8BitMixtape/8Bit-Mixtape-NEO/boards/8Bit-Mixtape-NEO_v1/DIY_Board/8BitMixtape_ANYMA_Edition_22_MASK.pdf

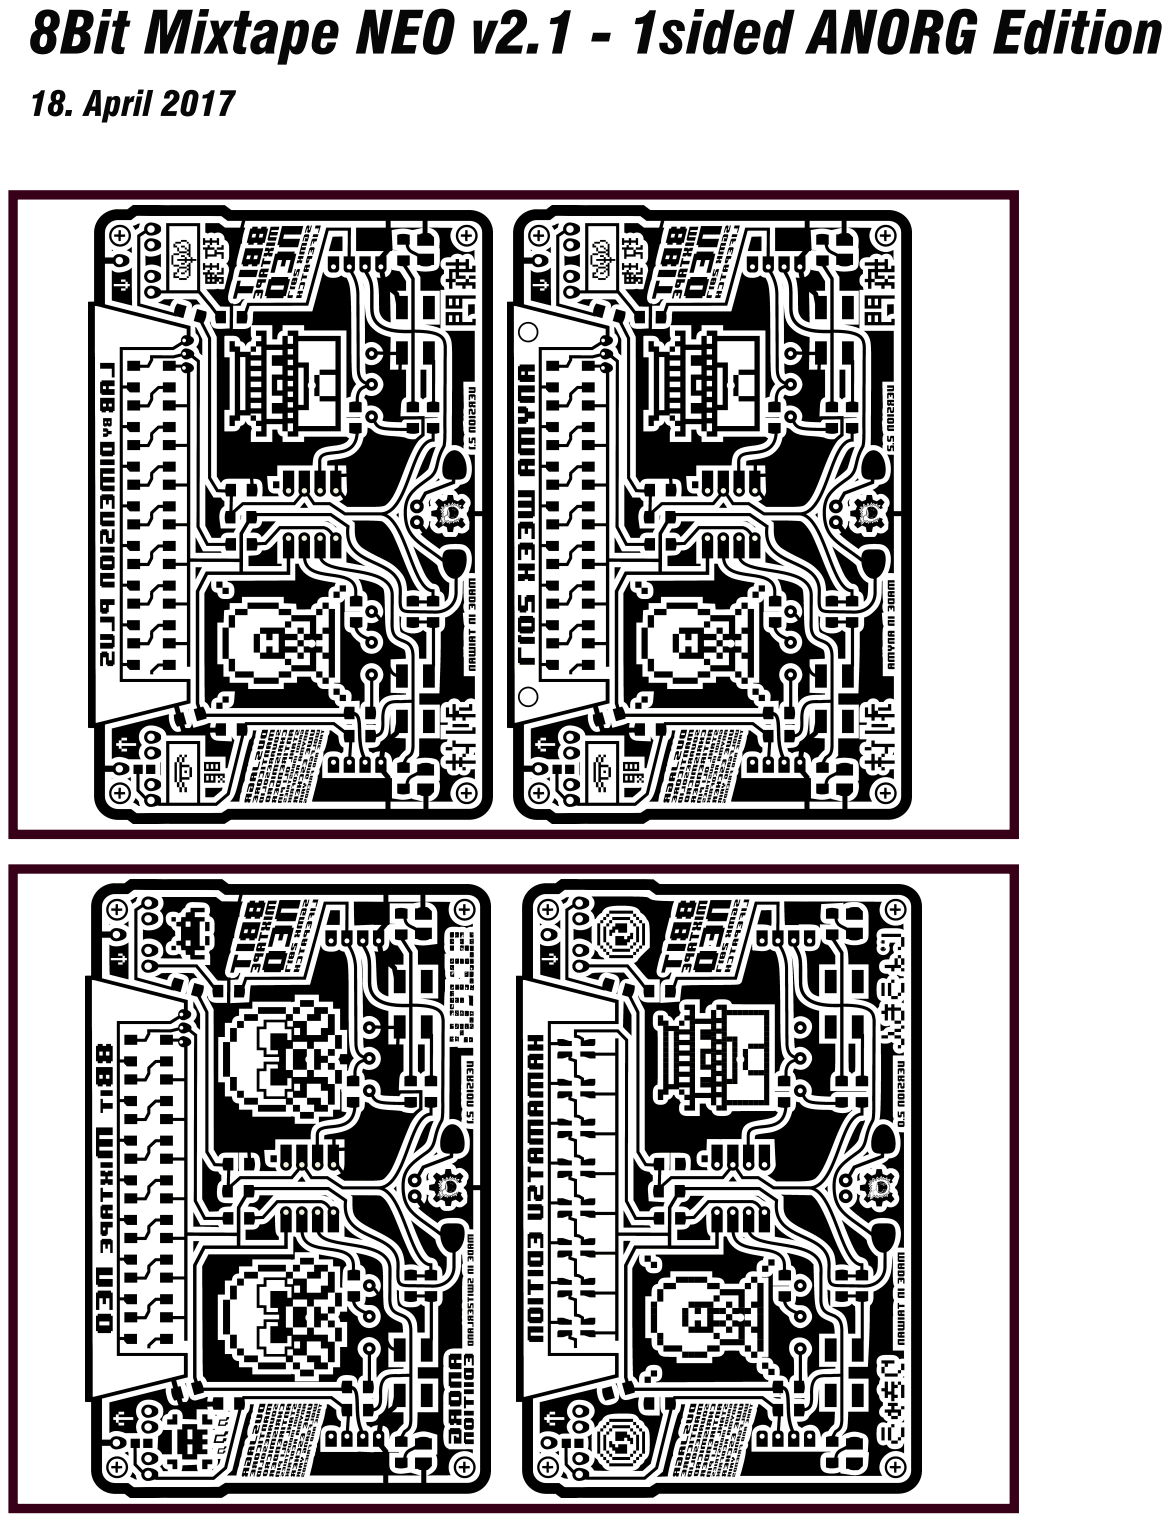
[picture p23: page 1]
