8BitMixtape/8Bit-Mixtape-NEO/boards/8Bit-Mixtape-NEO_v1/DIY_Board/8BitMixtape_Zagreb_Edition_23_MASK.pdf

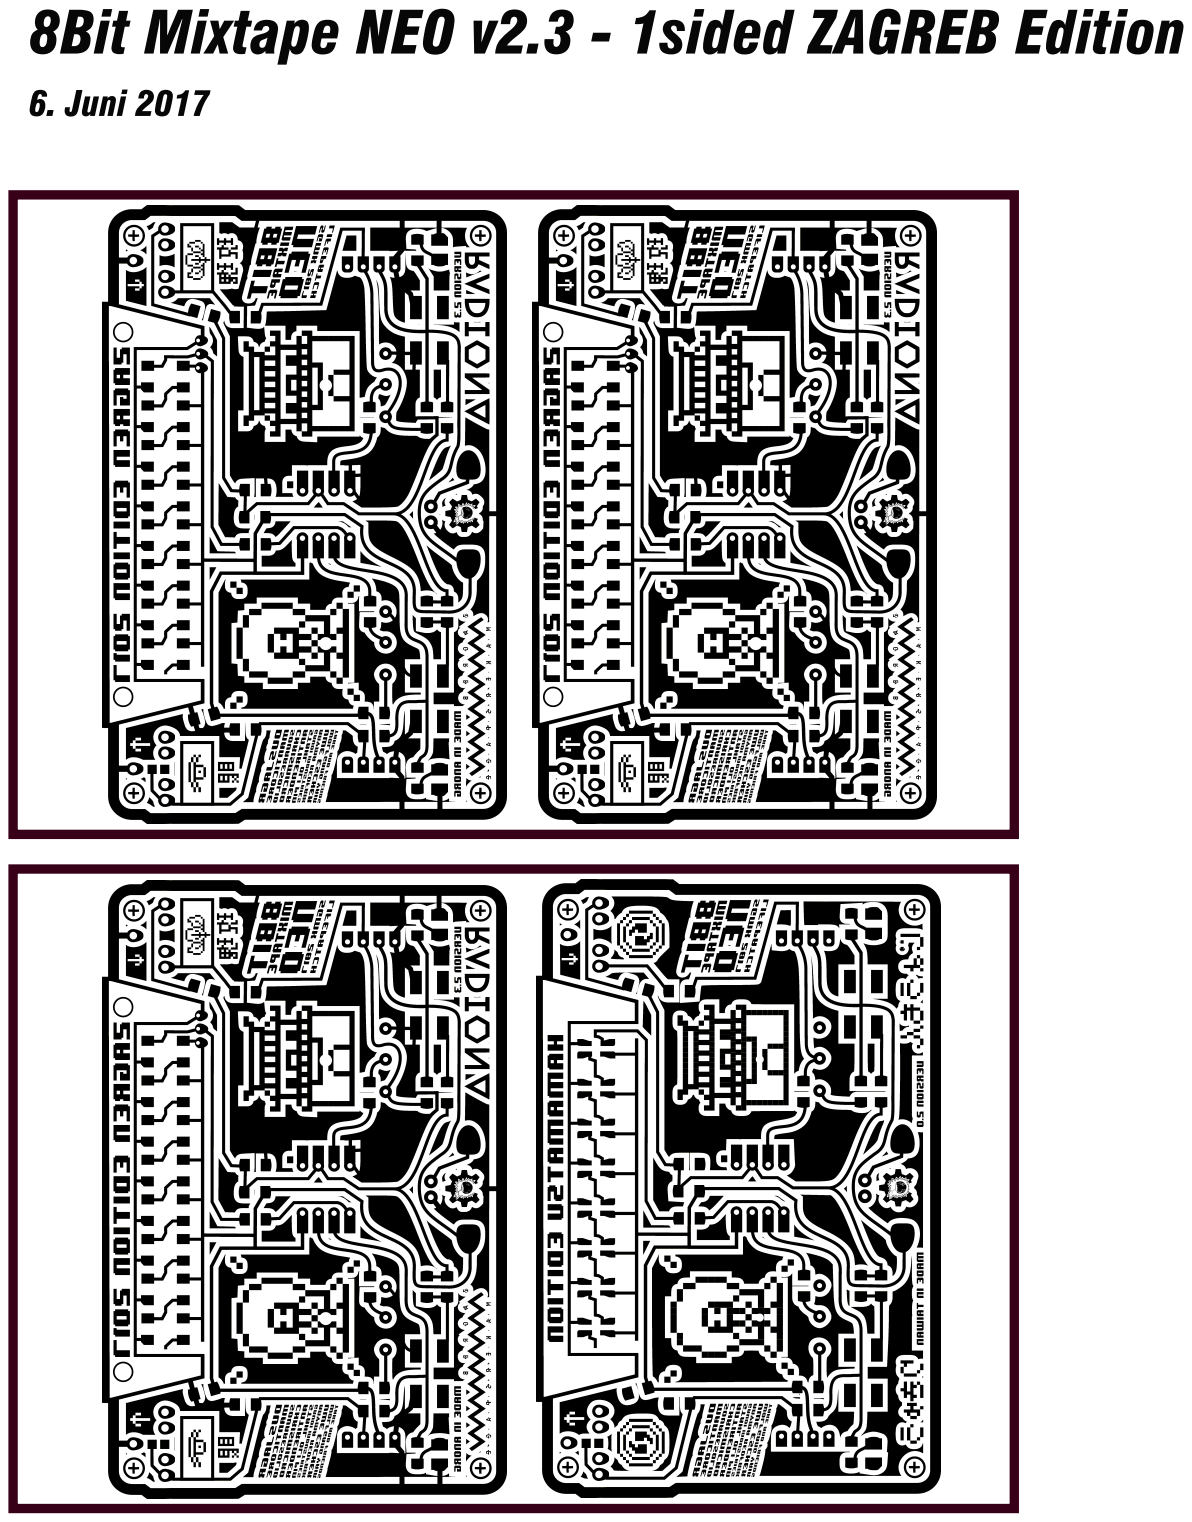
[picture p24: page 1]
