8BitMixtape/8Bit-Mixtape-NEO/boards/8Bit-Mixtape-NEO_v1/DIY_Board/mini_extensions.pdf

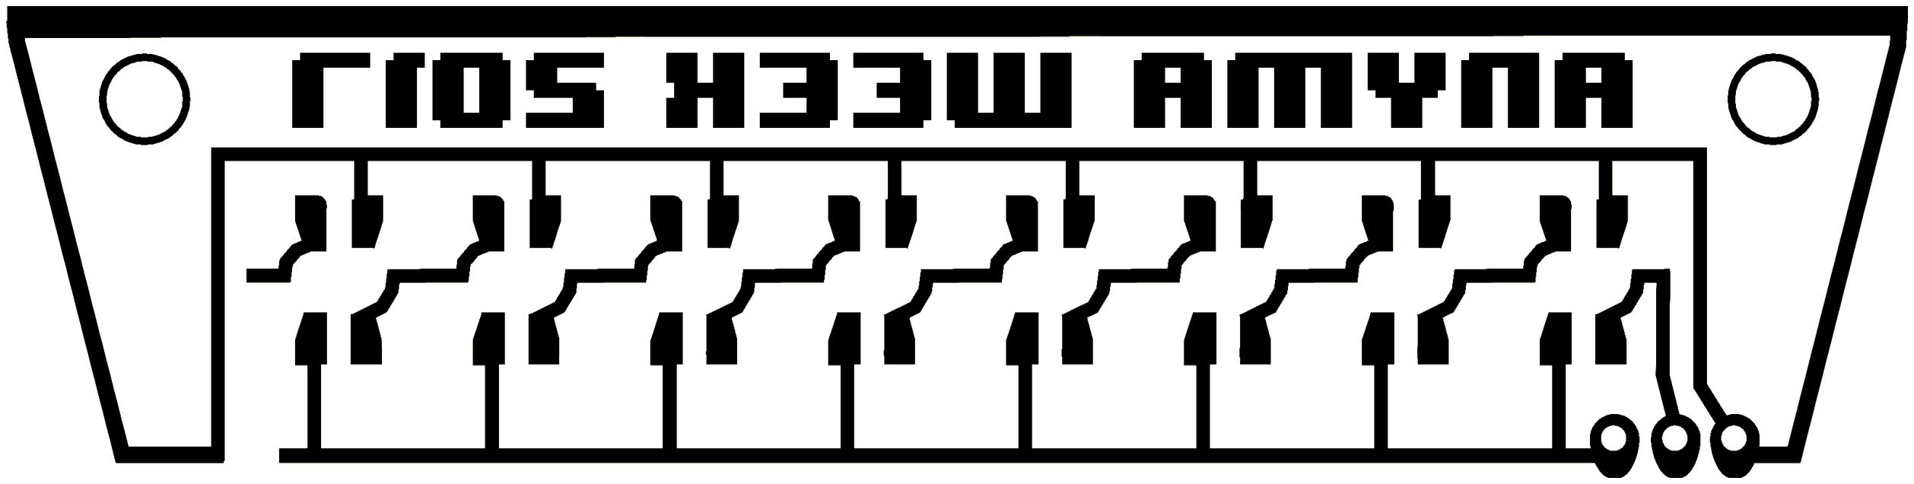
[picture p25: figure]
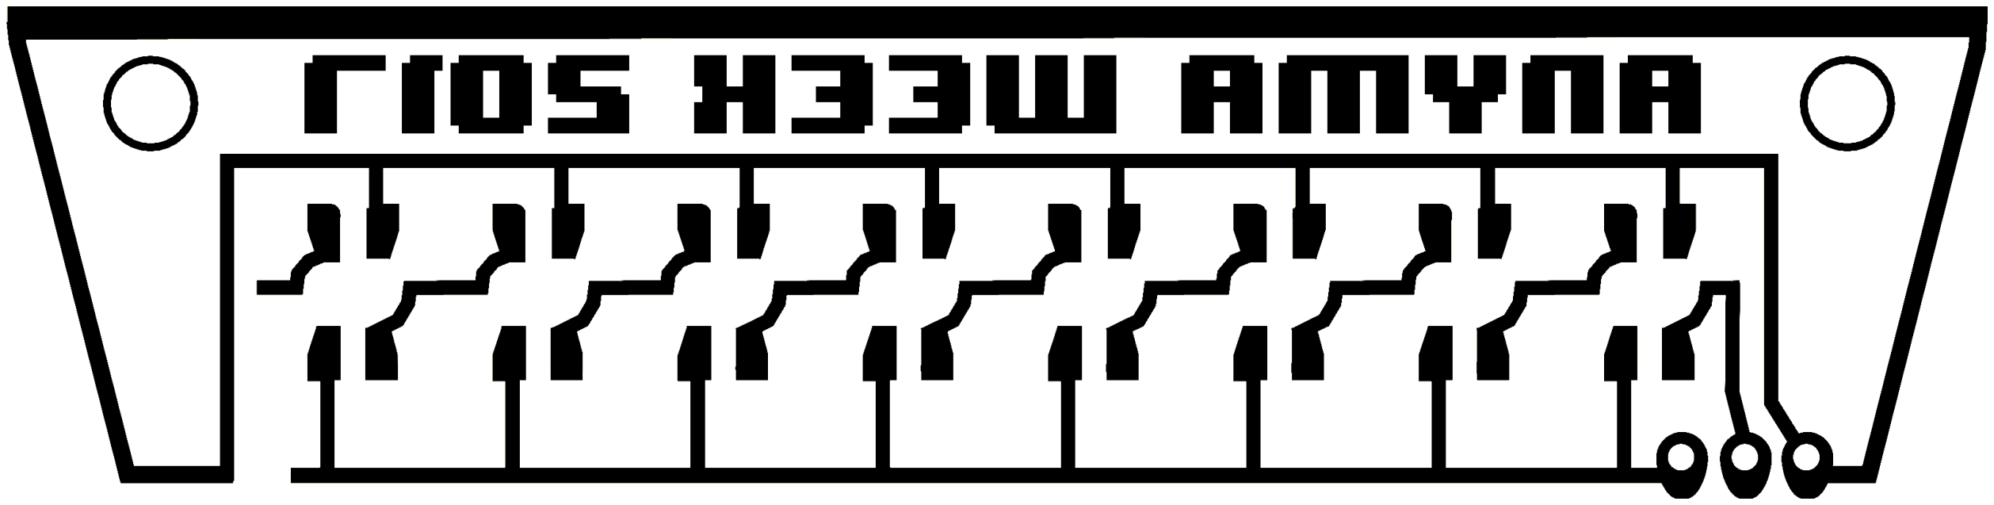
[picture p26: figure]
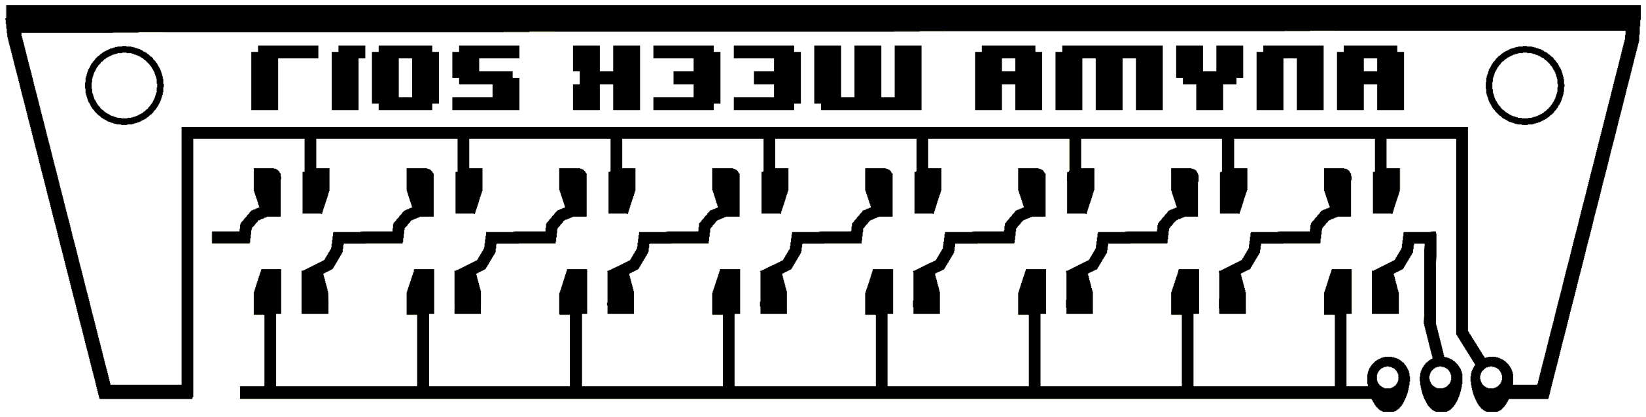
[picture p27: figure]
