8BitMixtape/8Bit-Mixtape-NEO/boards/8Bit-Mixtape-NEO_v1/DIY_Board/8BitMixtape_ANORG_Edition_21_MASK.pdf

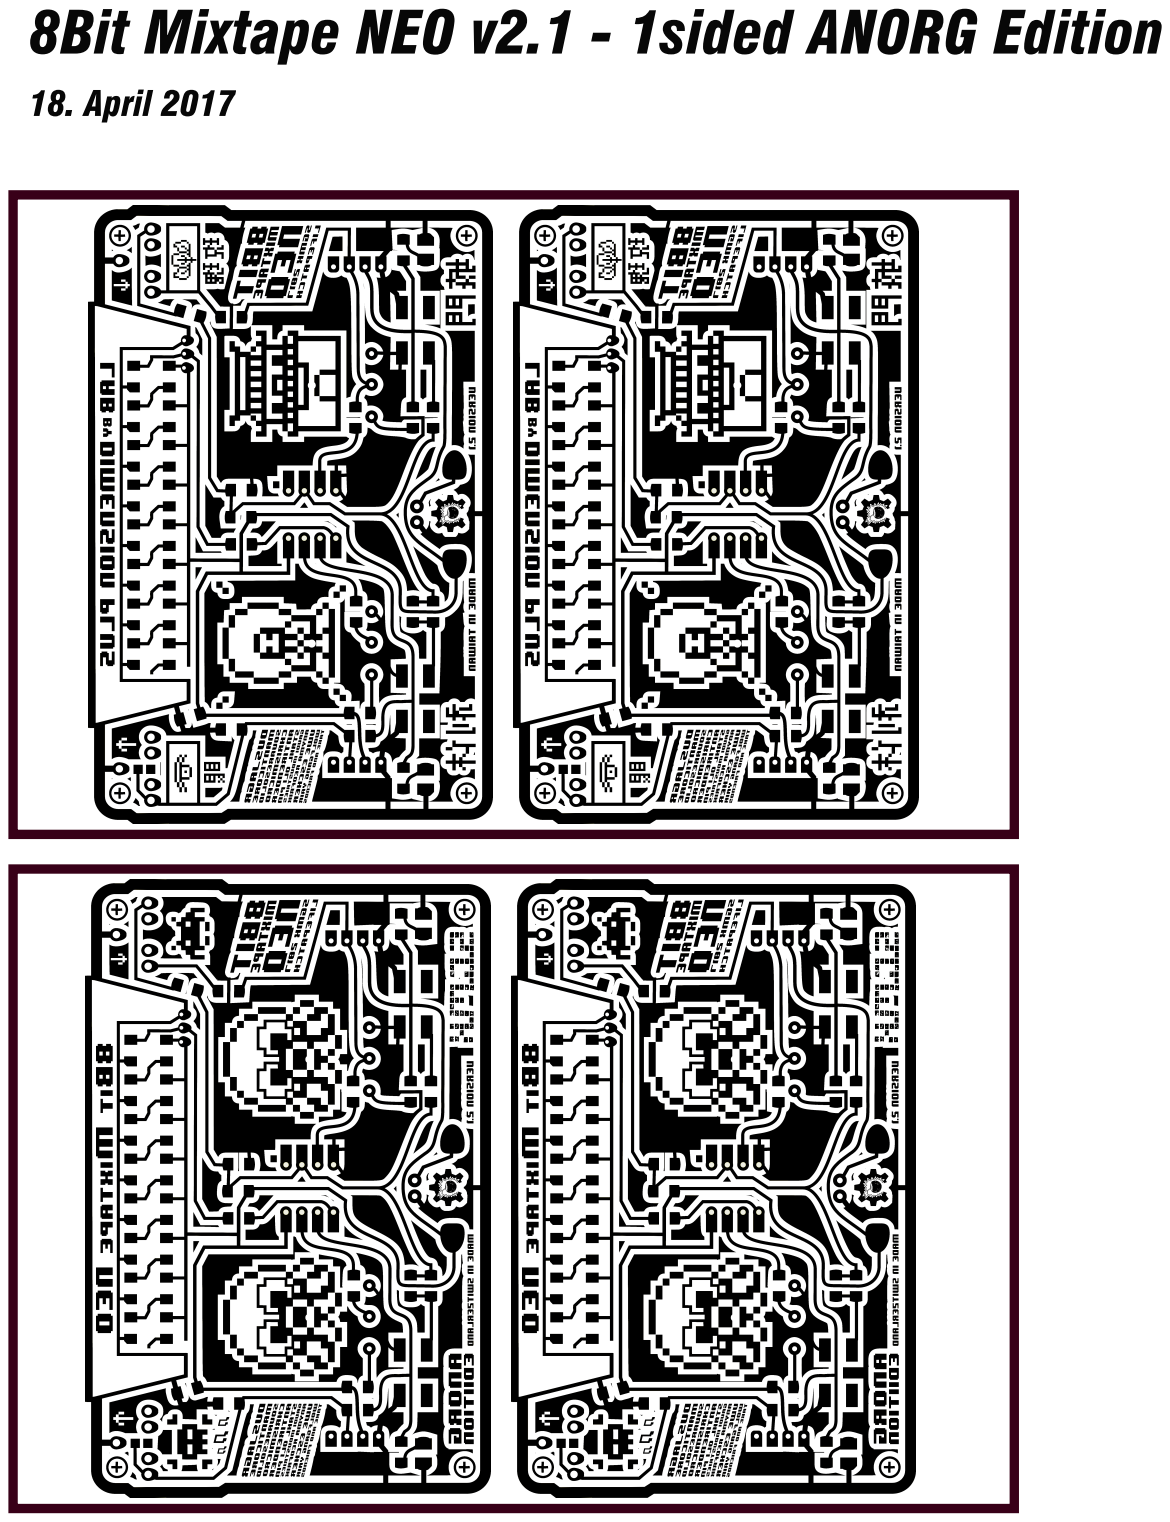
[picture p28: page 1]
