8BitMixtape/8Bit-Mixtape-NEO/boards/8Bit-Mixtape-NEO_v1/DIY_Board/8BitMixtape_Hamamatsu_Edition_20_MASK.pdf

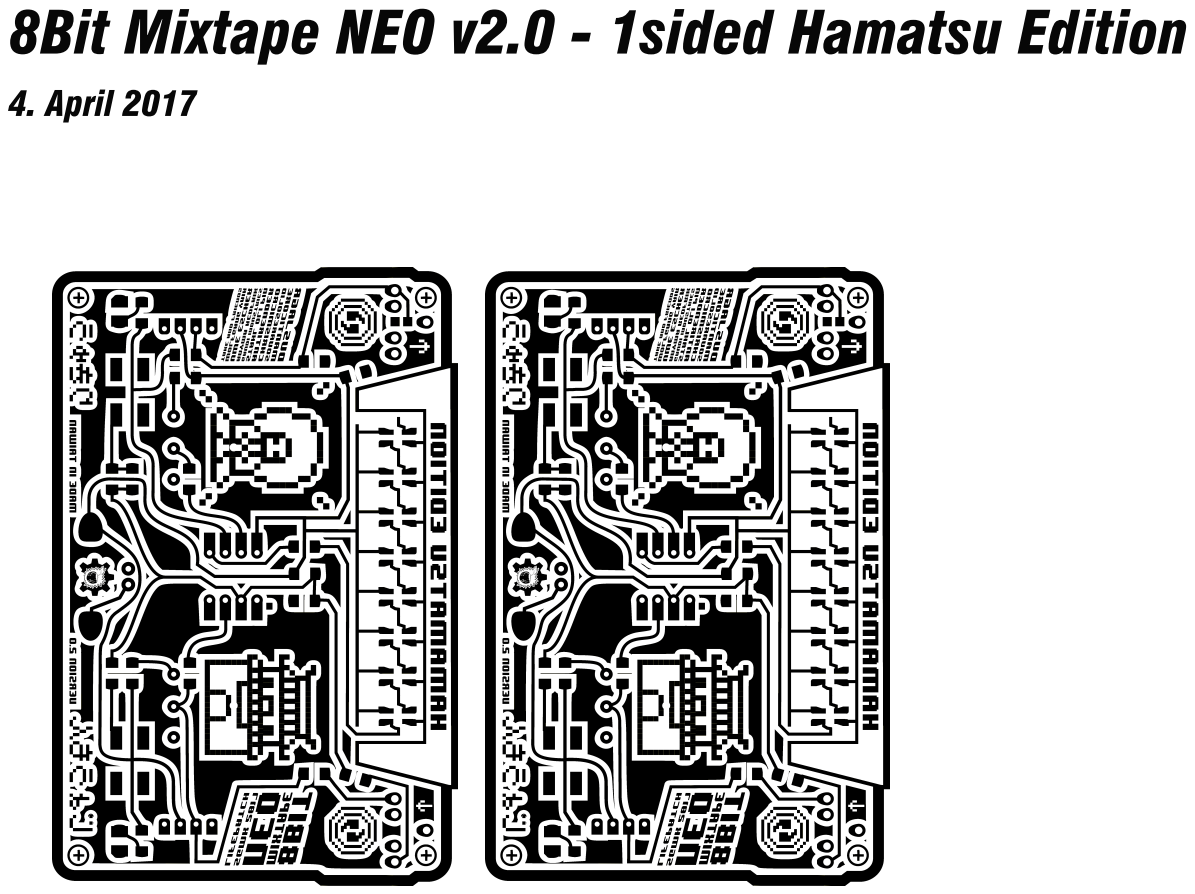
[picture p29: page 1]
