8BitMixtape/8Bit-Mixtape-NEO/boards/8Bit-Mixtape-NEO_v1/DIY_Board/8BitMixtape_Taiwan_Edition_20_MASK.pdf

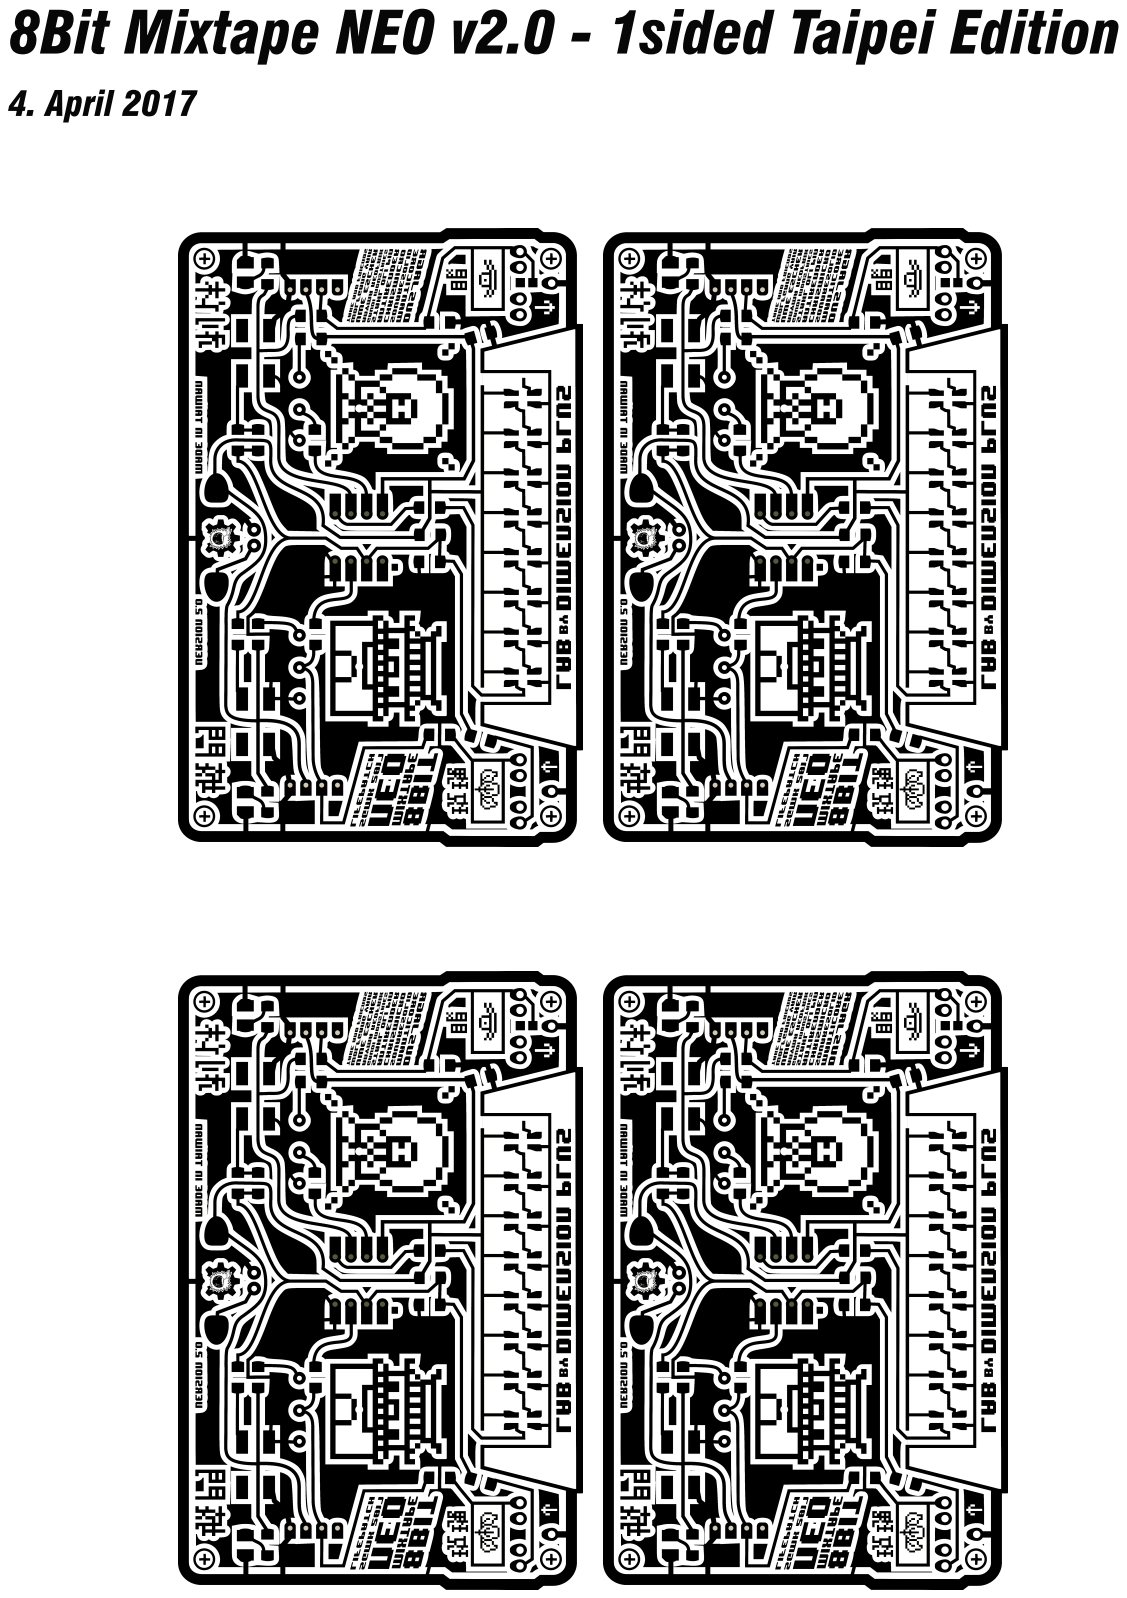
[picture p30: page 1]
