8BitMixtape/8Bit-Mixtape-NEO/boards/8Bit-Mixtape-NEO_v1/DIY_Board/8BitMixtape_Taiwan_Edition_16_MASK.pdf

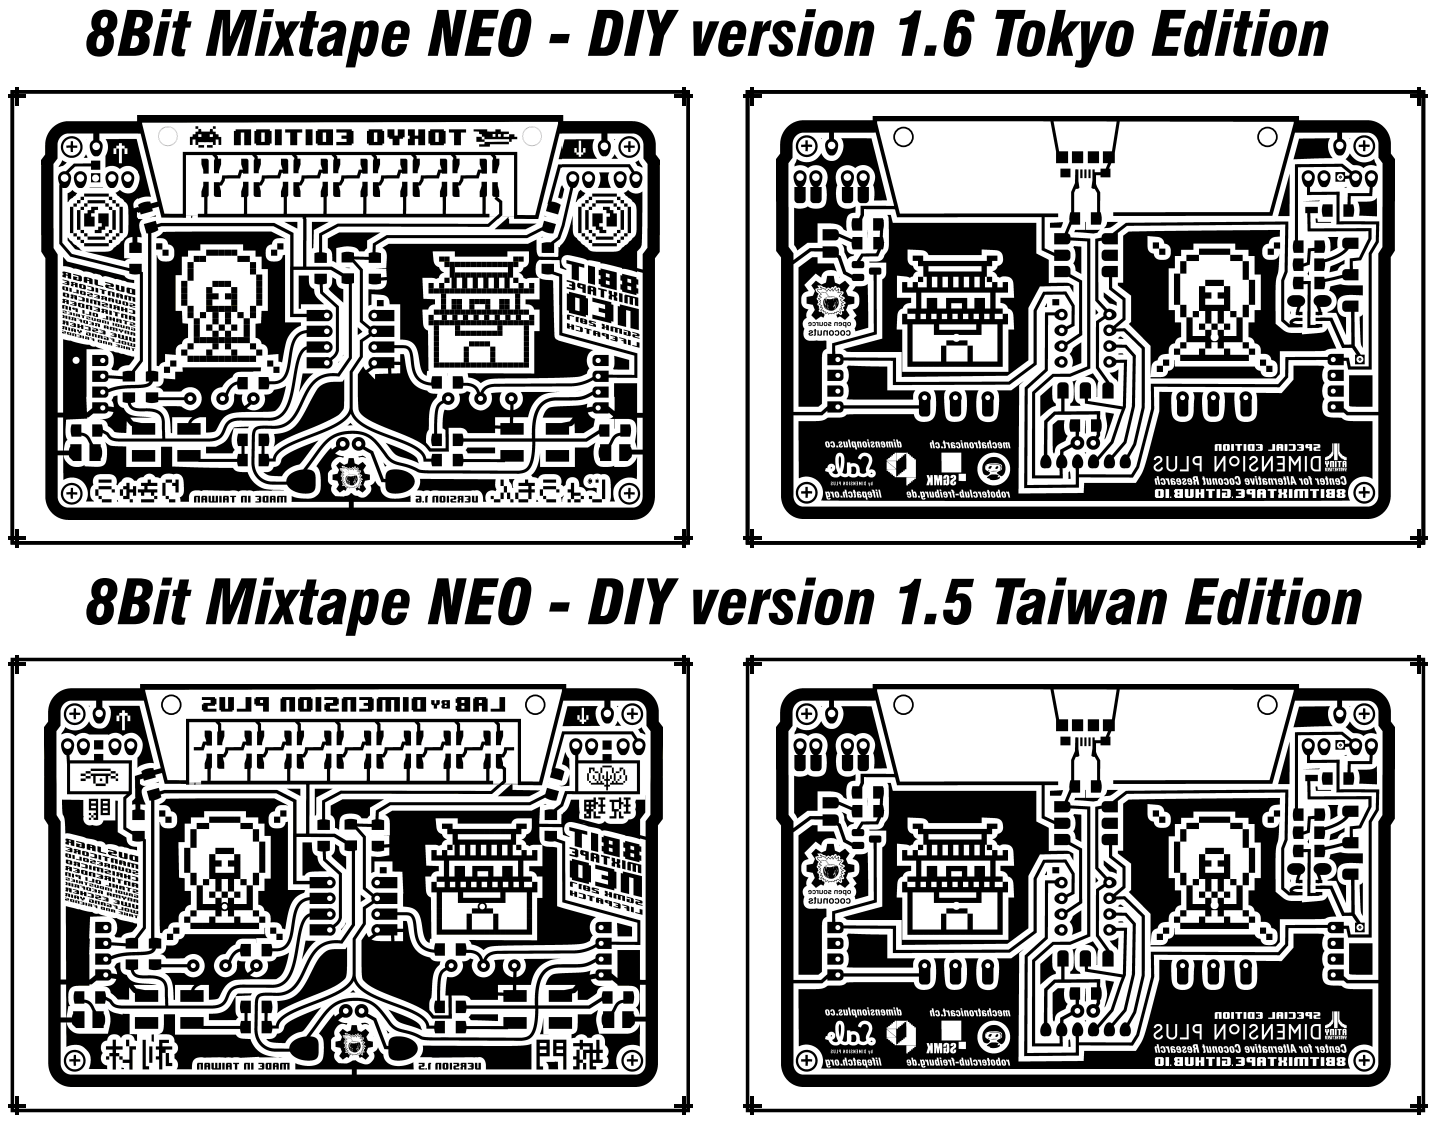
[picture p31: page 1]
