8BitMixtape/8Bit-Mixtape-NEO/boards/8Bit-Mixtape-NEO_v1/DIY_Board/8BitMixtape_Taiwan_Edition_15_MASK.pdf

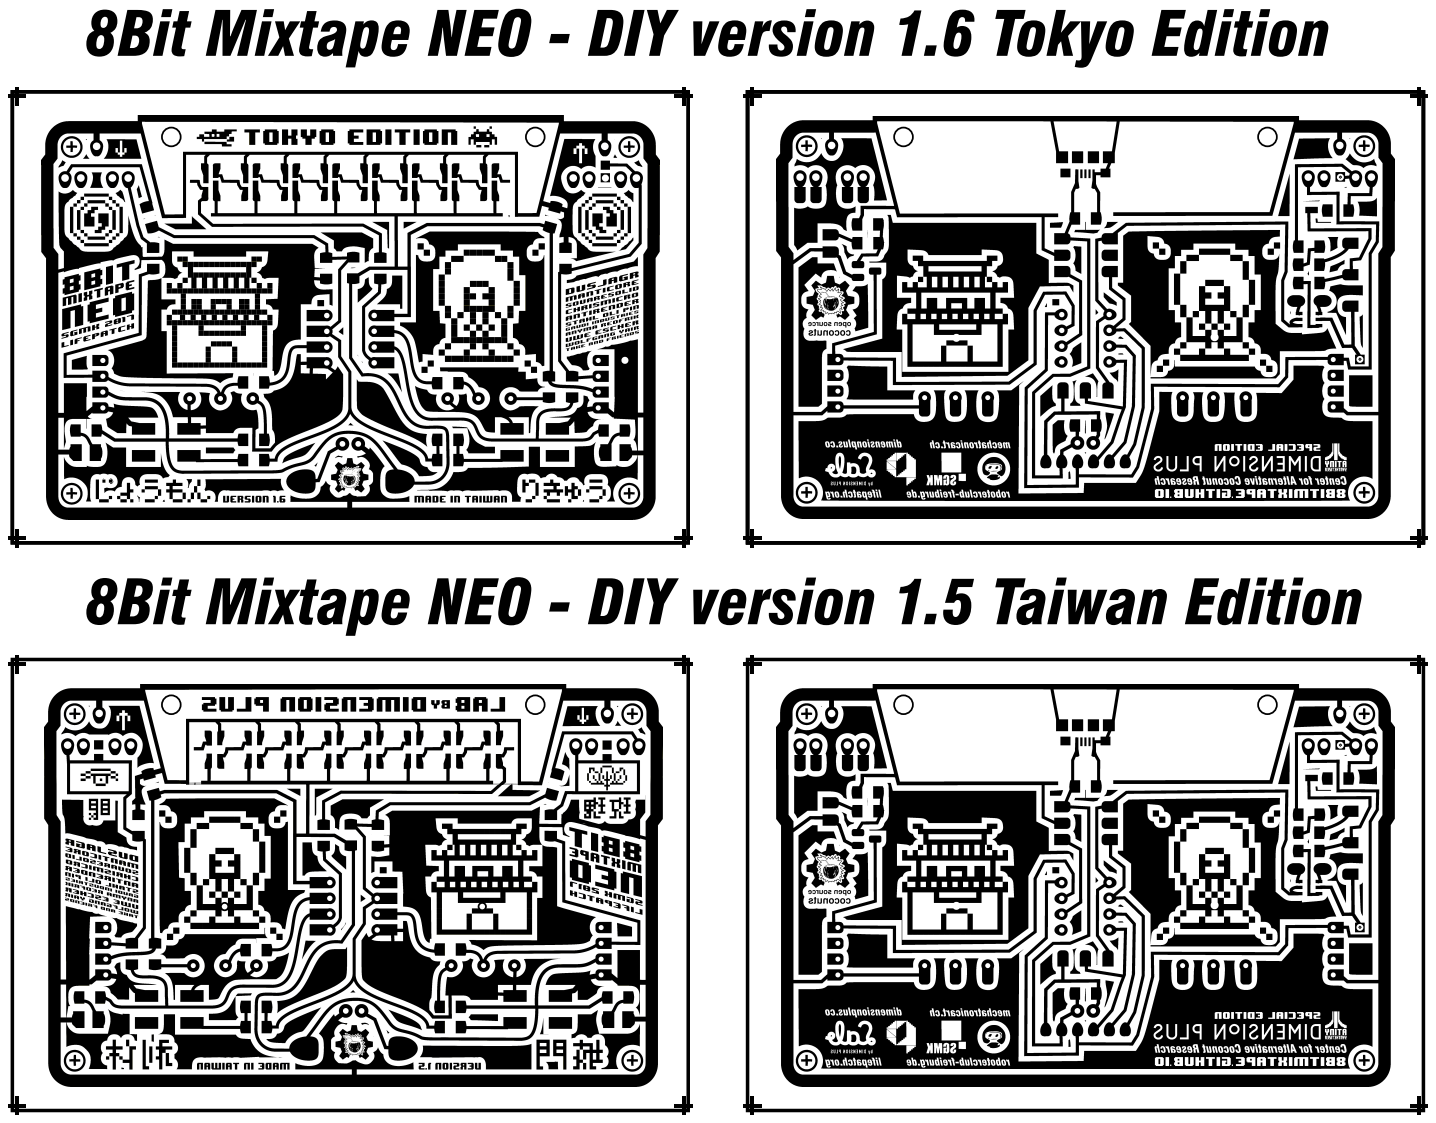
[picture p32: page 1]
