8BitMixtape/8Bit-Mixtape-NEO/boards/8Bit-Mixtape-NEO_v1/DIY_Board/8BitMixtape_Taiwan_Edition_14_MASK.pdf

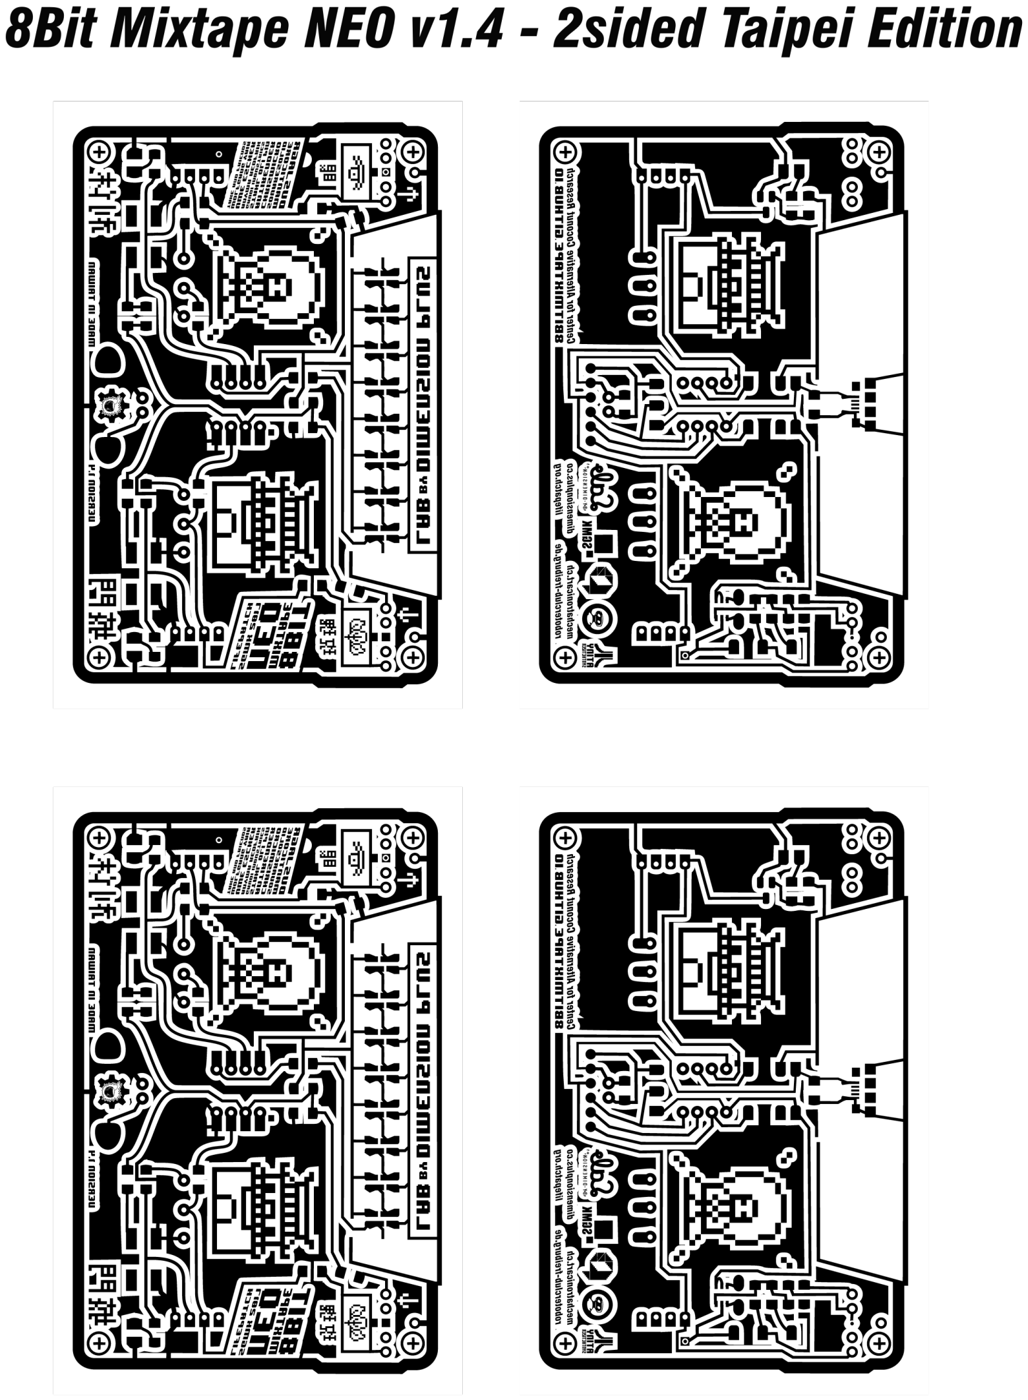
[picture p33: page 1]
