8BitMixtape/8Bit-Mixtape-NEO/8BitMixtapeNEO_v20_TaiwanReady.jpg

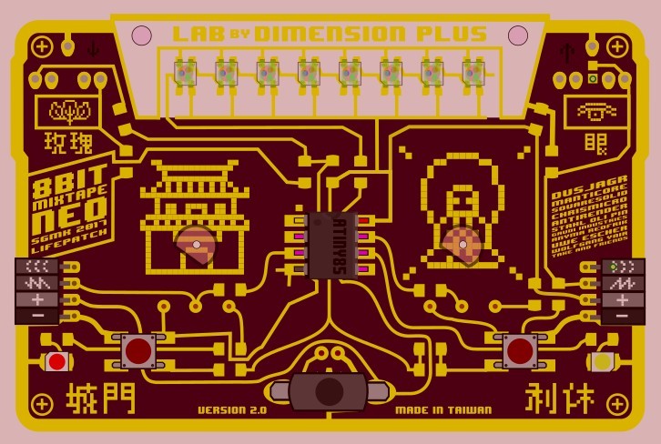
8BitMixtapeNEO_v20_TaiwanReady.jpg
