8BitMixtape/8Bit-Mixtape-NEO/boards/3d-files/Photos/mixTapes_prototypes_cirkulacija2.jpg

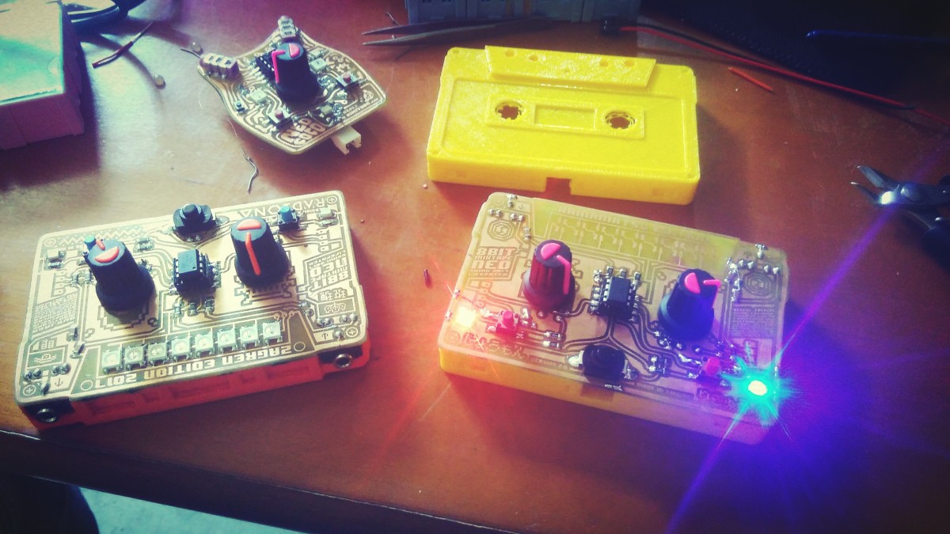
boards/3d-files/Photos/mixTapes_prototypes_cirkulacija2.jpg
