8BitMixtape/8Bit-Mixtape-NEO/boards/3d-files/Photos/Tape_3d_FullCase_Update_v4.jpg

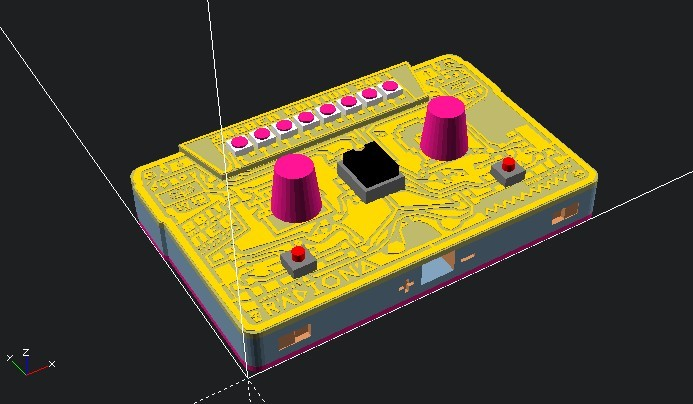
boards/3d-files/Photos/Tape_3d_FullCase_Update_v4.jpg
