8BitMixtape/8Bit-Mixtape-NEO/boards/8Bit-Mixtape-NEO_v1/8BitMixtapeNEO_v10_design.jpg

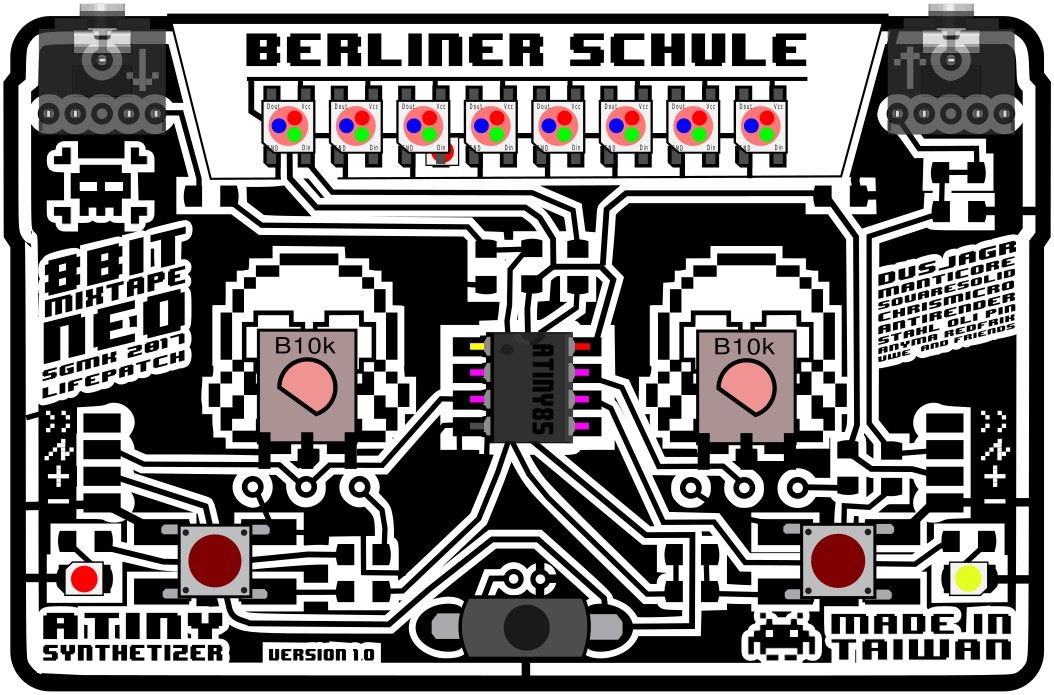
boards/8Bit-Mixtape-NEO_v1/8BitMixtapeNEO_v10_design.jpg
