8BitMixtape/8Bit-Mixtape-NEO/boards/8Bit-Mixtape-NEO_v1/8BitMixtapeNEO_v12_dimension_Black.png

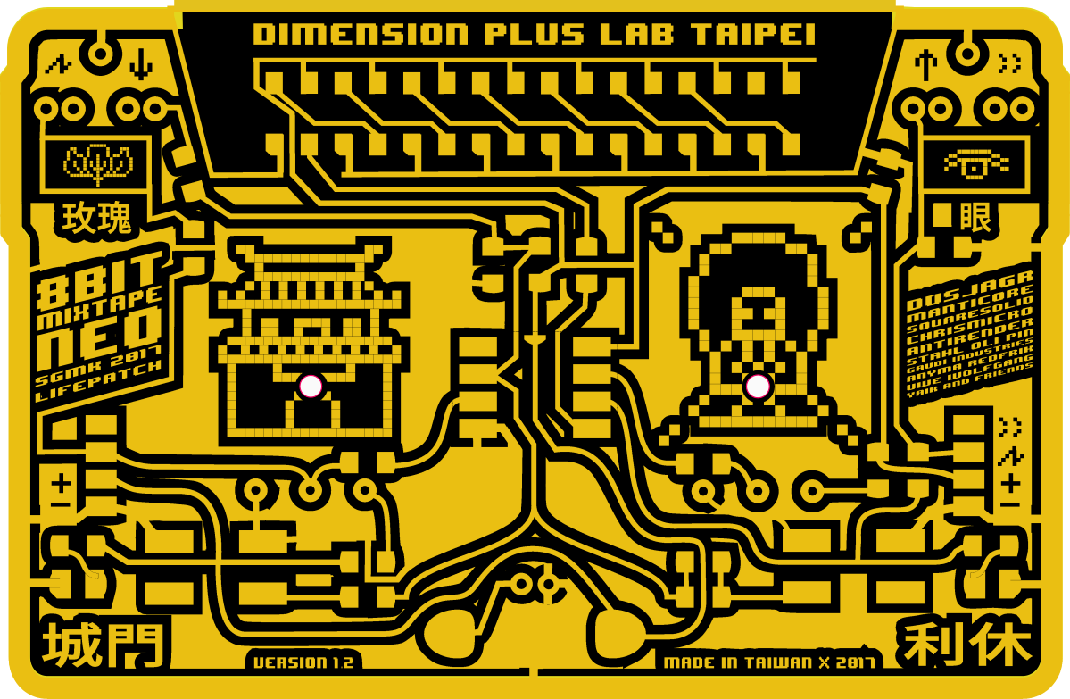
boards/8Bit-Mixtape-NEO_v1/8BitMixtapeNEO_v12_dimension_Black.png
