8BitMixtape/8Bit-Mixtape-NEO/boards/8Bit-Mixtape-NEO_v1/DIY_Board/8BitMixtape_DIY_Edition_27_pure.png

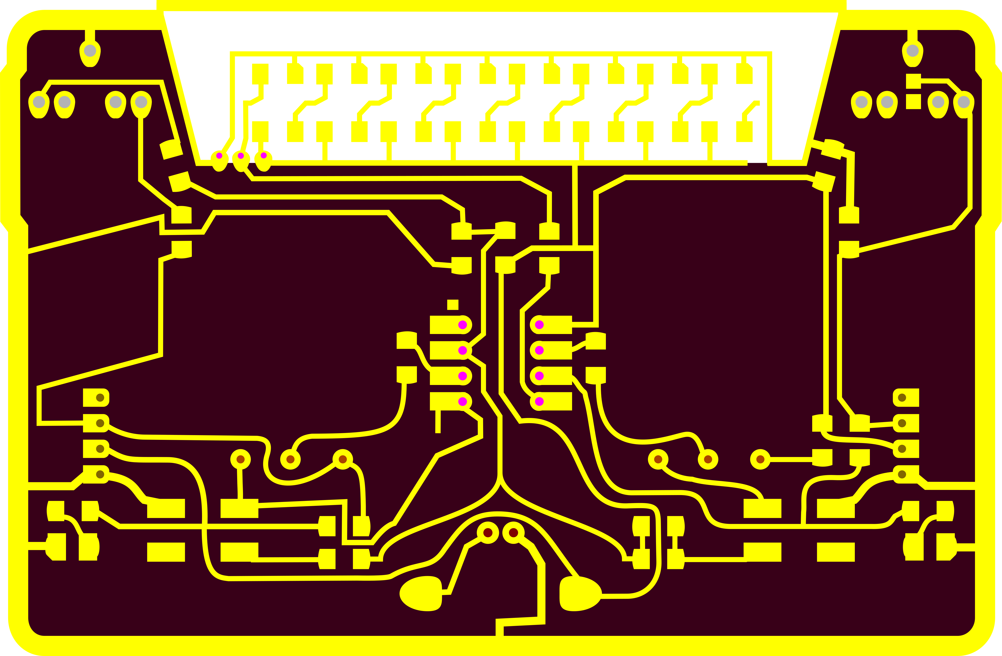
boards/8Bit-Mixtape-NEO_v1/DIY_Board/8BitMixtape_DIY_Edition_27_pure.png
