8BitMixtape/8Bit-Mixtape-NEO/boards/8Bit-Mixtape-NEO_v1/DIY_Board/8BitMixtape_Ucok.png

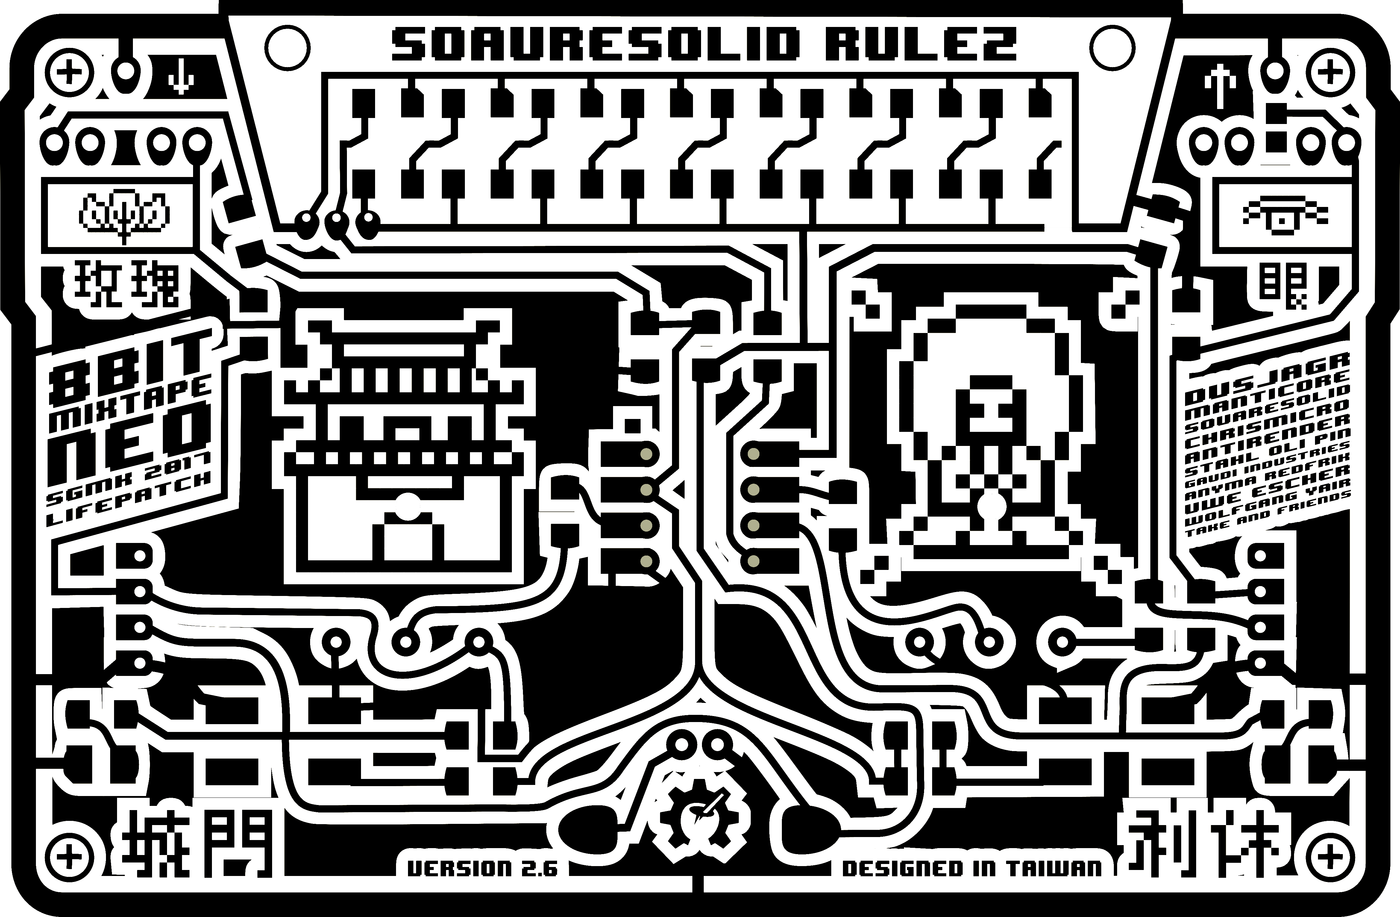
boards/8Bit-Mixtape-NEO_v1/DIY_Board/8BitMixtape_Ucok.png
