8BitMixtape/8Bit-Mixtape-NEO/boards/8Bit-Mixtape-NEO_v1/DIY_Board/MixTape_DP-Style_v20_MASK.png

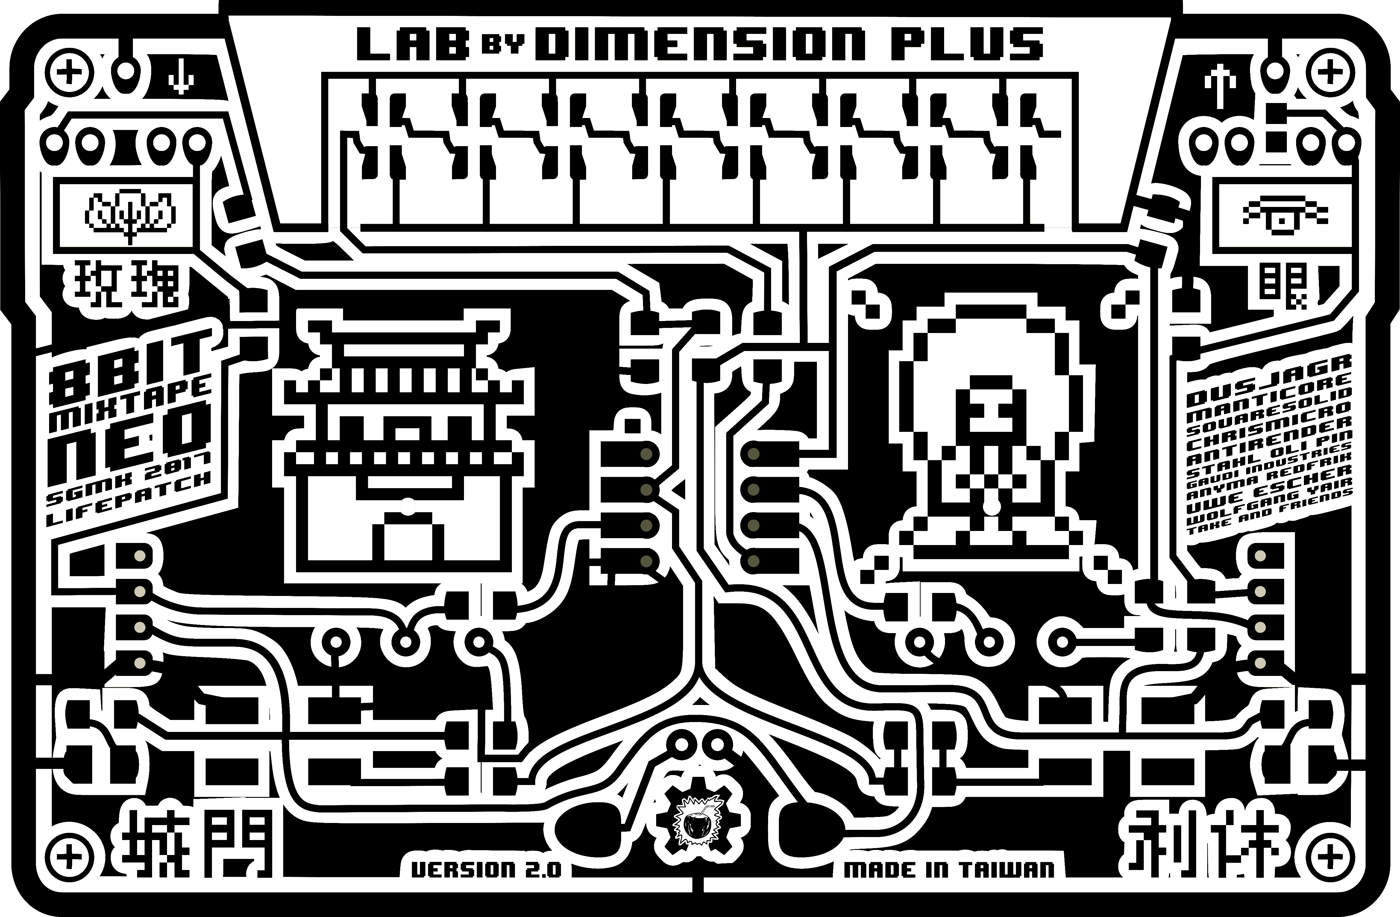
boards/8Bit-Mixtape-NEO_v1/DIY_Board/MixTape_DP-Style_v20_MASK.png
