8BitMixtape/8Bit-Mixtape-NEO/boards/8Bit-Mixtape-NEO_v1/DIY_Board/MixTape_NoStyle_v20.png

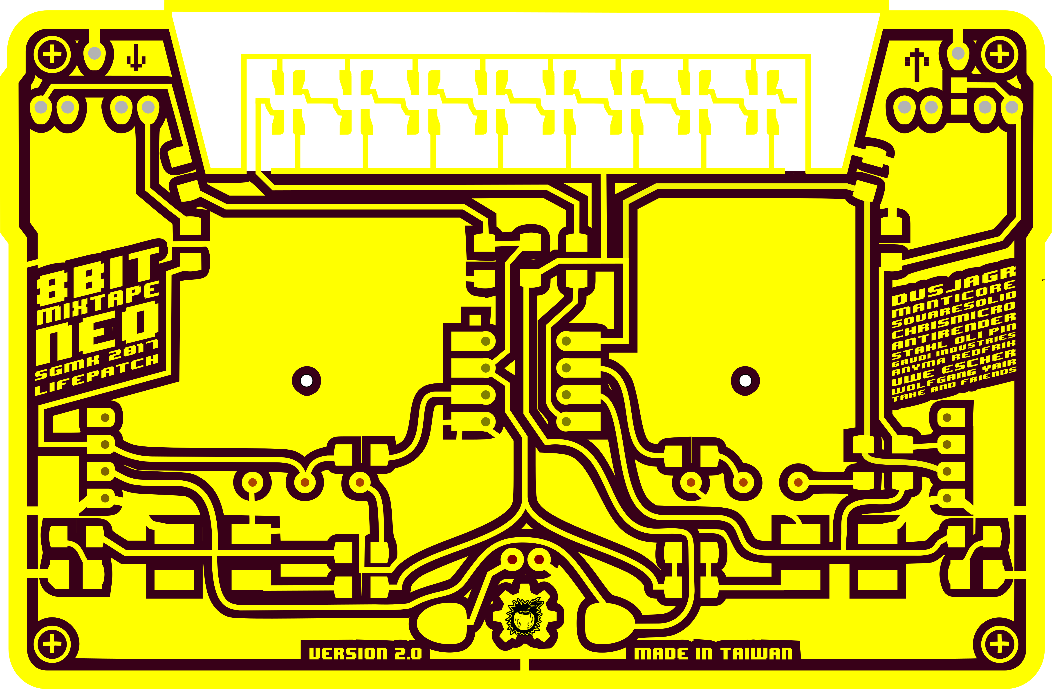
boards/8Bit-Mixtape-NEO_v1/DIY_Board/MixTape_NoStyle_v20.png
