8BitMixtape/8Bit-Mixtape-NEO/boards/8Bit-Mixtape-NEO_v1/DIY_Board/MixTape_Zagreb-Style_v23.png

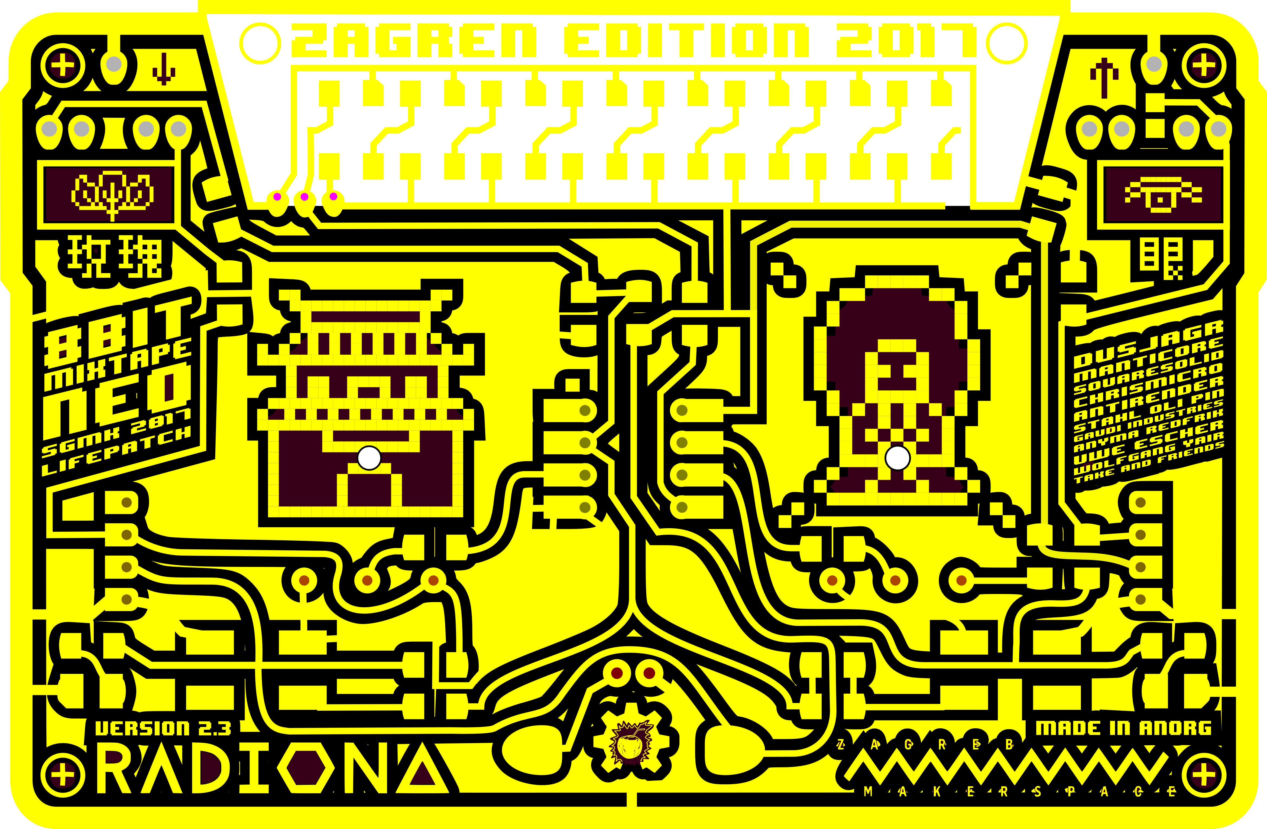
boards/8Bit-Mixtape-NEO_v1/DIY_Board/MixTape_Zagreb-Style_v23.png
