8BitMixtape/8Bit-Mixtape-NEO/boards/8Bit-Mixtape-NEO_v1/DIY_Board/NEO-Mixtape_PixelExtension.png

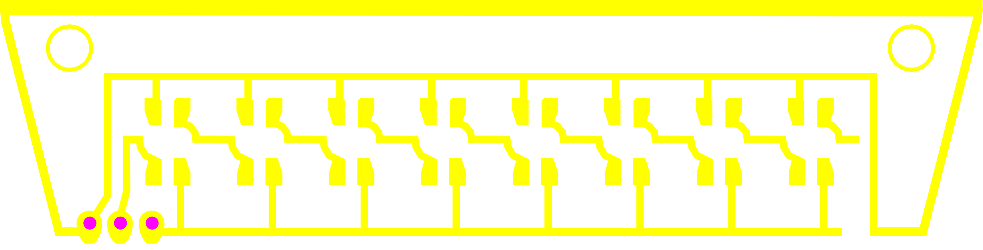
boards/8Bit-Mixtape-NEO_v1/DIY_Board/NEO-Mixtape_PixelExtension.png
