8BitMixtape/8Bit-Mixtape-NEO/boards/8Bit-Mixtape-NEO_v1/MixTape_BackSide_Copper_v20.png

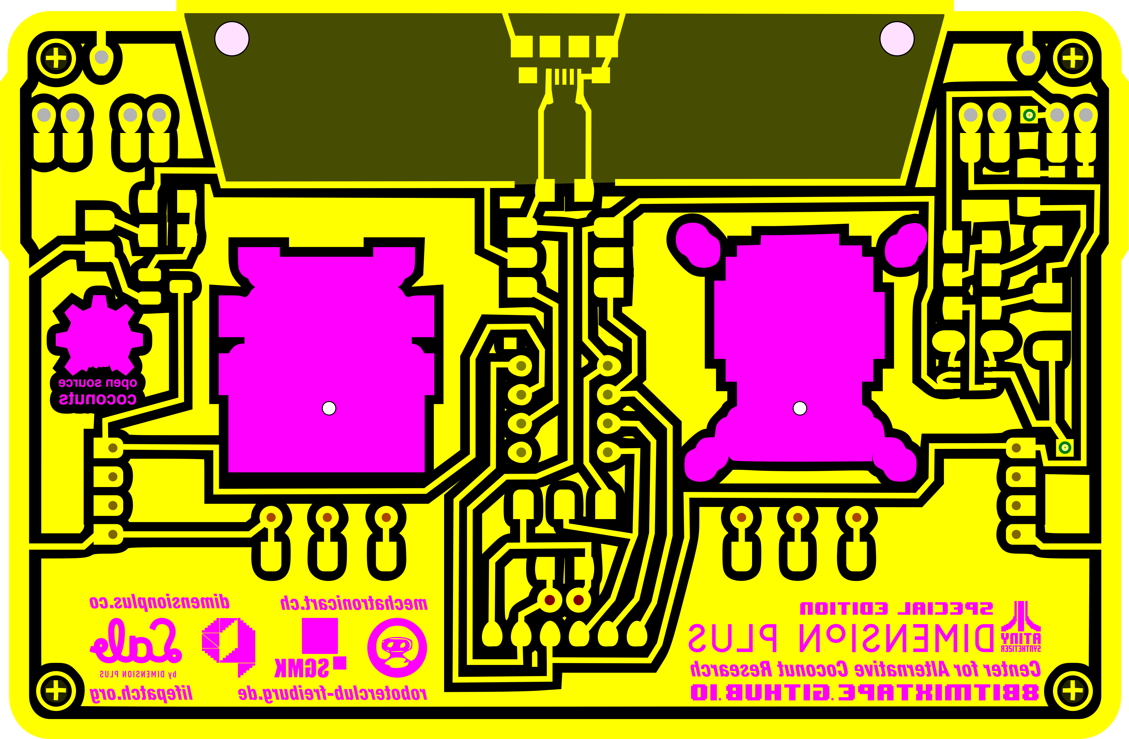
boards/8Bit-Mixtape-NEO_v1/MixTape_BackSide_Copper_v20.png
