8BitMixtape/8Bit-Mixtape-NEO/boards/8Bit-Mixtape-NEO_v1/Robertos_DIL_board.jpg

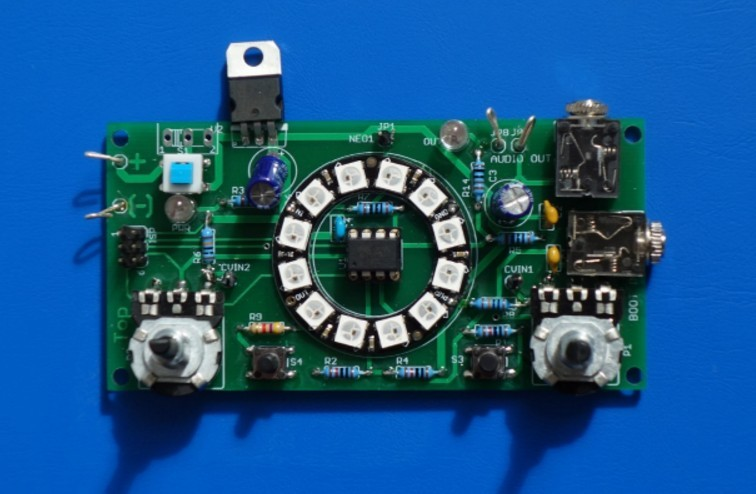
boards/8Bit-Mixtape-NEO_v1/Robertos_DIL_board.jpg
