8BitMixtape/8Bit-Mixtape-NEO/boards/8Bit-Mixtape-NEO_v1/ShenzhenReady/8BitMixtape-NEO_Backside_v10.png

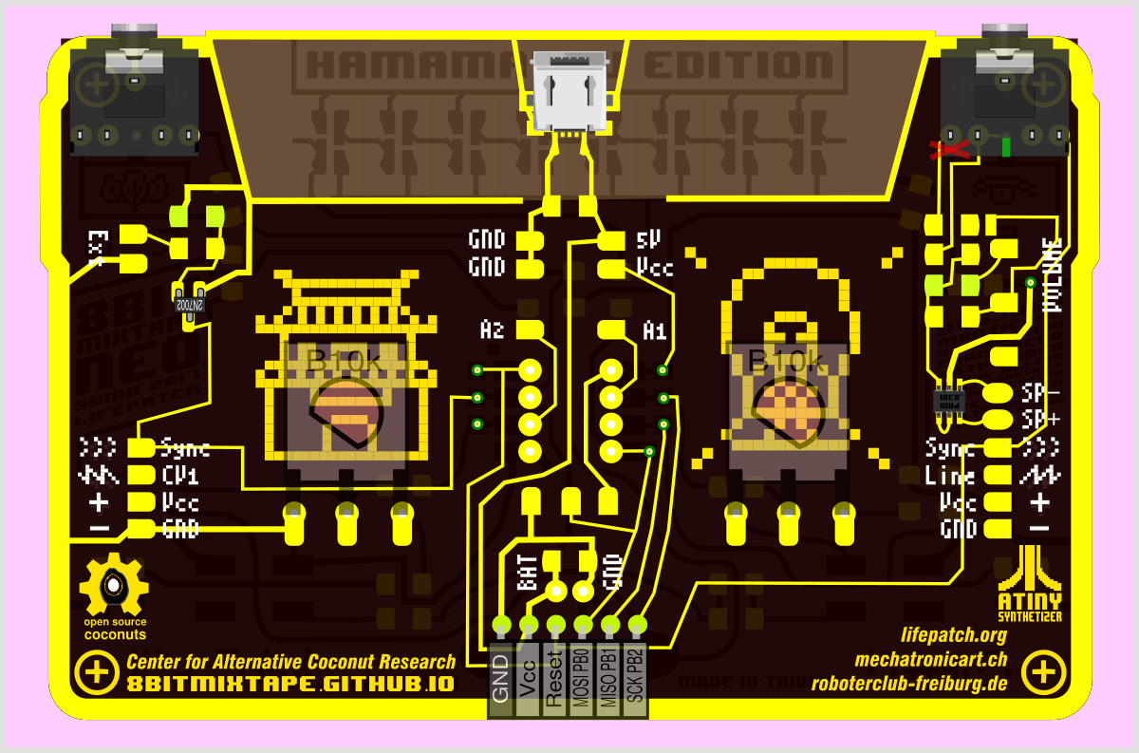
boards/8Bit-Mixtape-NEO_v1/ShenzhenReady/8BitMixtape-NEO_Backside_v10.png
