8BitMixtape/8Bit-Mixtape-NEO/boards/8Bit-Mixtape-NEO_v1/ShenzhenReady/8BitMixtapeNEO_v20_Minimal.jpg

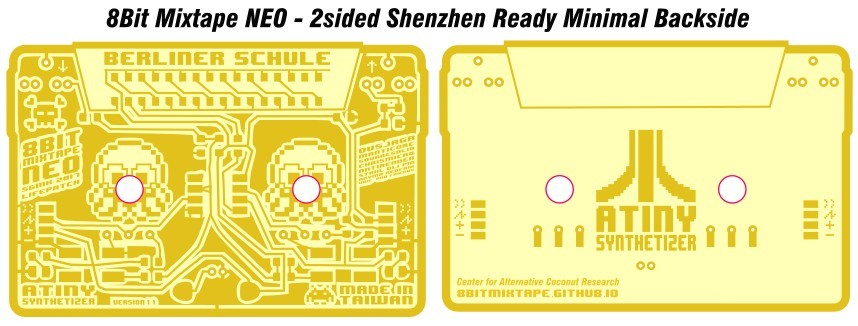
boards/8Bit-Mixtape-NEO_v1/ShenzhenReady/8BitMixtapeNEO_v20_Minimal.jpg
