8BitMixtape/8Bit-Mixtape-NEO/boards/8Bit-Mixtape-NEO_v1/ShenzhenReady/3535_NEO-pixel_Footprint.jpg

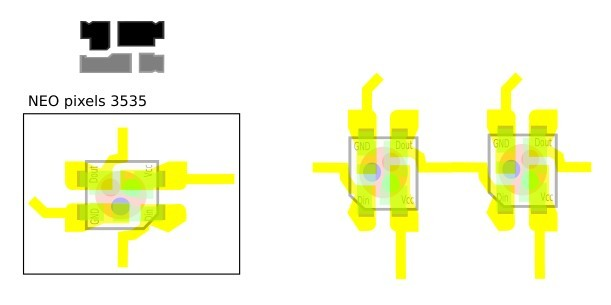
boards/8Bit-Mixtape-NEO_v1/ShenzhenReady/3535_NEO-pixel_Footprint.jpg
