8BitMixtape/8Bit-Mixtape-NEO/boards/8Bit-Mixtape-NEO_v1/ShenzhenReady/BackSide_features_Mixtape-NEO.jpg

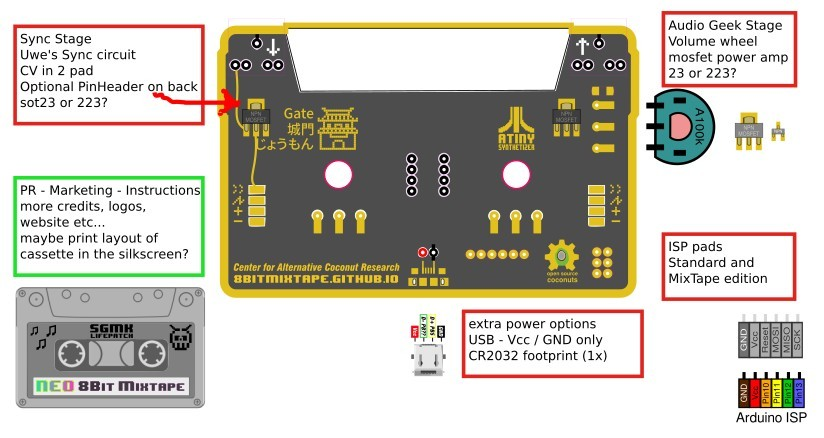
boards/8Bit-Mixtape-NEO_v1/ShenzhenReady/BackSide_features_Mixtape-NEO.jpg
