8BitMixtape/8Bit-Mixtape-NEO/boards/8Bit-Mixtape-NEO_v1/ShenzhenReady/backyard_brains_plug.jpg

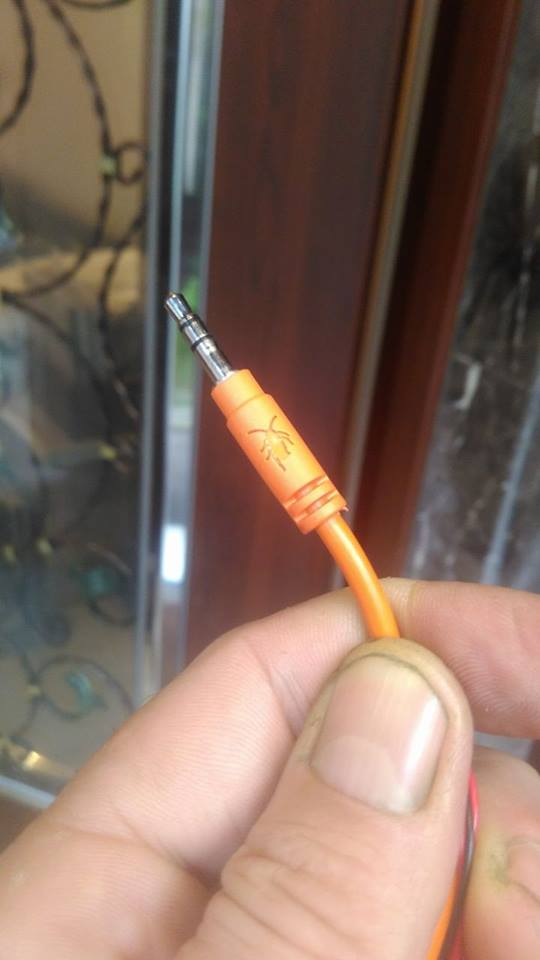
boards/8Bit-Mixtape-NEO_v1/ShenzhenReady/backyard_brains_plug.jpg
