8BitMixtape/8Bit-Mixtape-NEO/boards/8Bit-Mixtape-NEO_v1/ShenzhenReady/Batch003_Berlin/B03_8BitMixtape_BRL_bCu.png

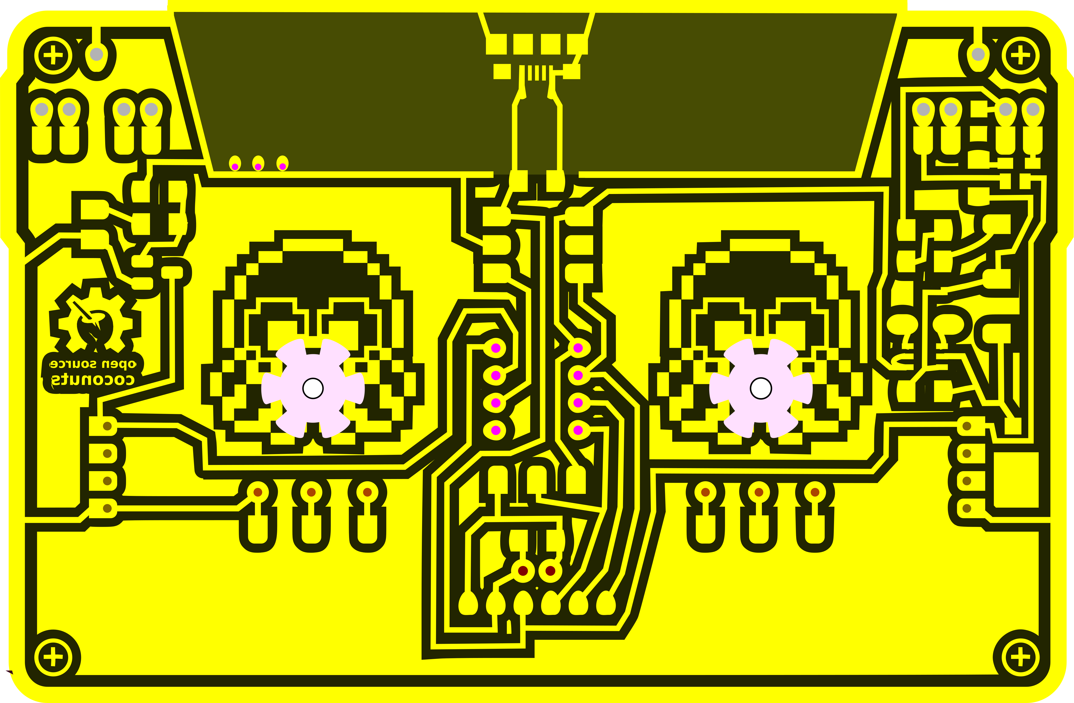
boards/8Bit-Mixtape-NEO_v1/ShenzhenReady/Batch003_Berlin/B03_8BitMixtape_BRL_bCu.png
