8BitMixtape/8Bit-Mixtape-NEO/boards/8Bit-Mixtape-NEO_v1/ShenzhenReady/Cable-geeking_hmmmm.jpg

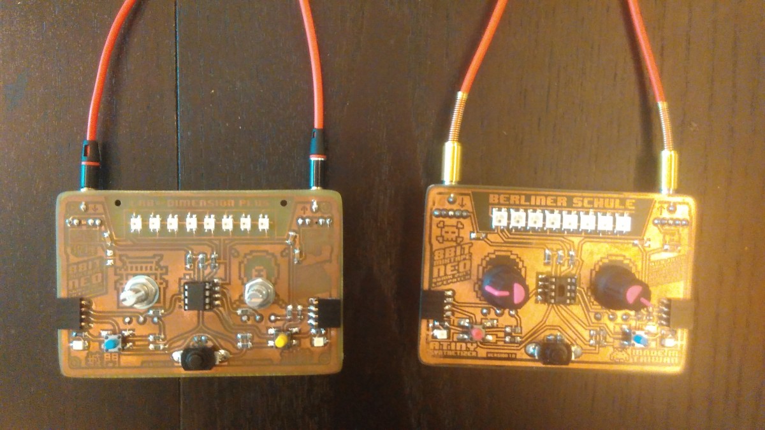
boards/8Bit-Mixtape-NEO_v1/ShenzhenReady/Cable-geeking_hmmmm.jpg
