8BitMixtape/8Bit-Mixtape-NEO/boards/8Bit-Mixtape-NEO_v1/ShenzhenReady/credits_section.jpg

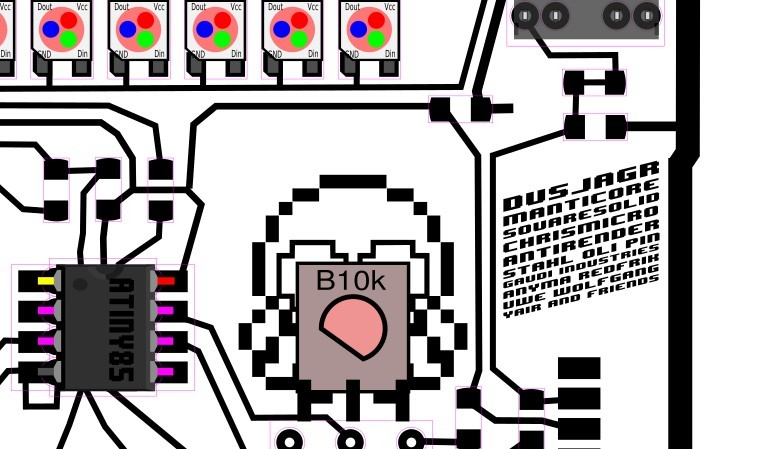
boards/8Bit-Mixtape-NEO_v1/ShenzhenReady/credits_section.jpg
