8BitMixtape/8Bit-Mixtape-NEO/boards/8Bit-Mixtape-NEO_v1/ShenzhenReady/IMG_20170319_165920.jpg

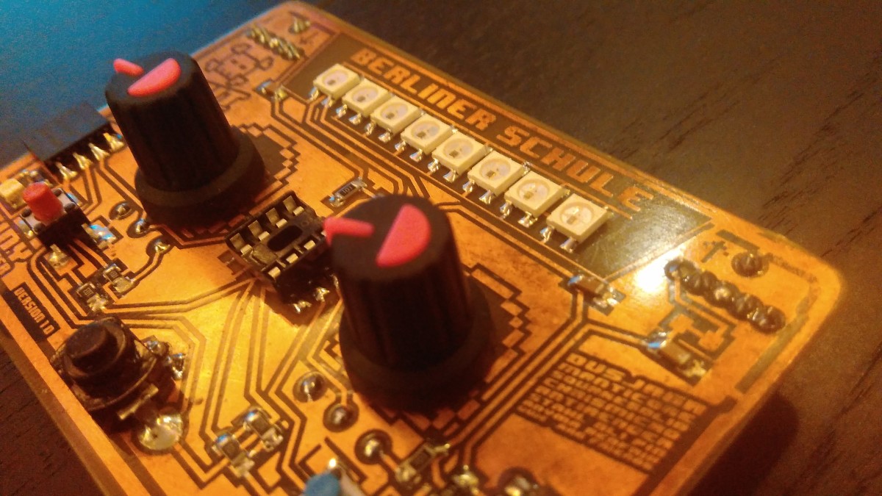
boards/8Bit-Mixtape-NEO_v1/ShenzhenReady/IMG_20170319_165920.jpg
