8BitMixtape/8Bit-Mixtape-NEO/boards/8Bit-Mixtape-NEO_v1/ShenzhenReady/Pad_Size_comparison_overview.jpg

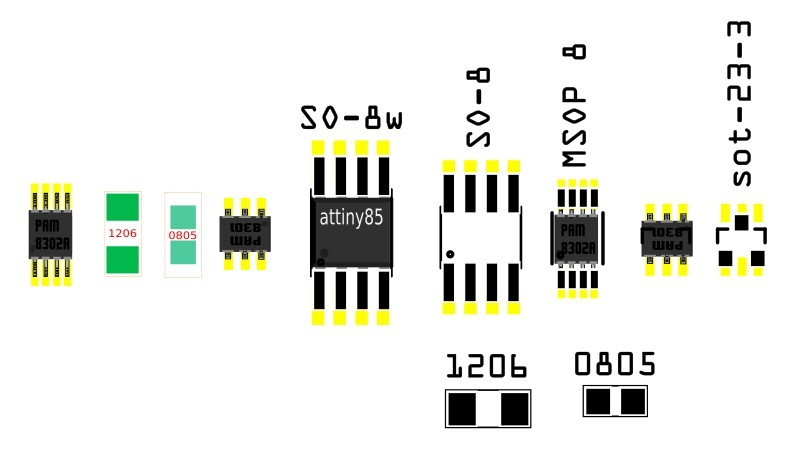
boards/8Bit-Mixtape-NEO_v1/ShenzhenReady/Pad_Size_comparison_overview.jpg
