8BitMixtape/8Bit-Mixtape-NEO/boards/8Bit-Mixtape-NEO_v1/ShenzhenReady/PCBway_settings.jpg

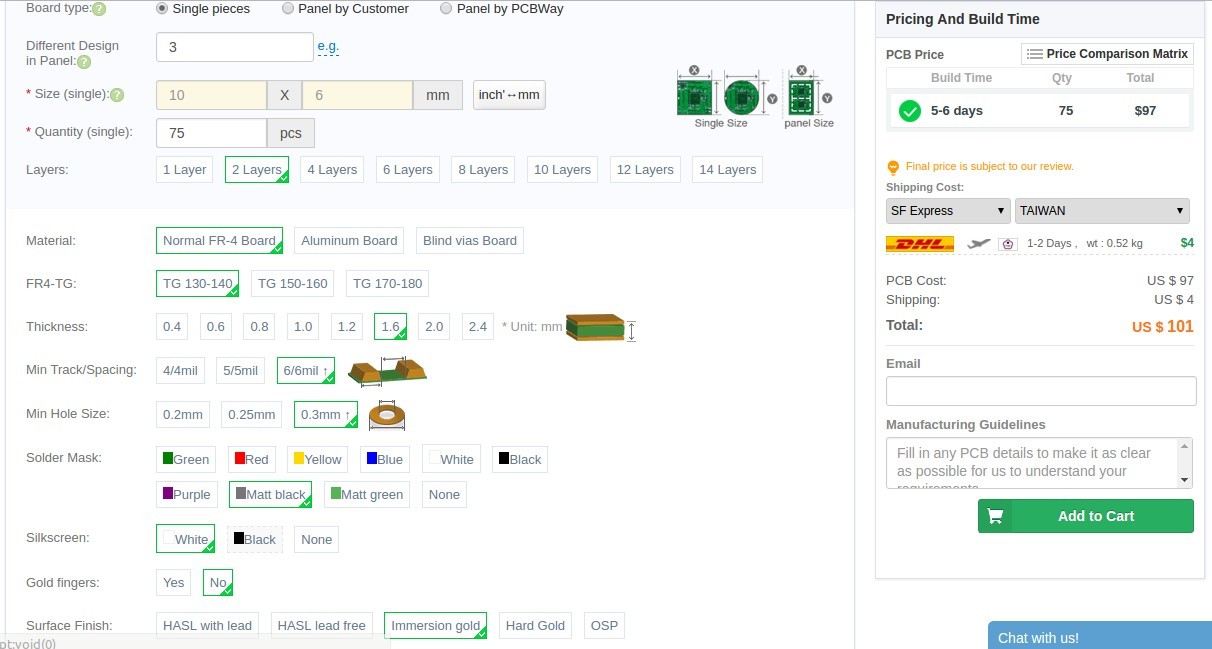
boards/8Bit-Mixtape-NEO_v1/ShenzhenReady/PCBway_settings.jpg
