8BitMixtape/8Bit-Mixtape-NEO/boards/8Bit-Mixtape-NEO_v1/ShenzhenReady/plugology_in_colors_30cents.jpg

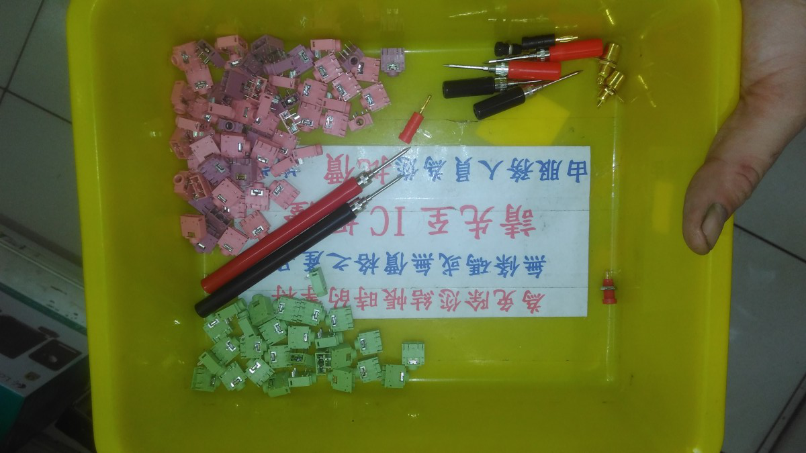
boards/8Bit-Mixtape-NEO_v1/ShenzhenReady/plugology_in_colors_30cents.jpg
