8BitMixtape/8Bit-Mixtape-NEO/boards/8Bit-Mixtape-NEO_v1/ShenzhenReady/ShinY-PCB.jpg

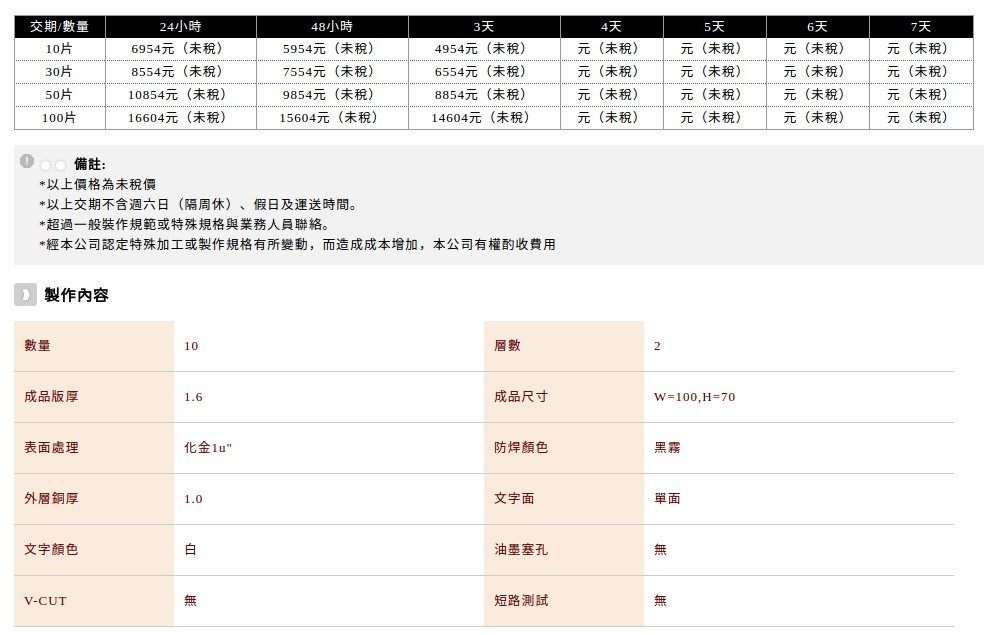
boards/8Bit-Mixtape-NEO_v1/ShenzhenReady/ShinY-PCB.jpg
