8BitMixtape/8Bit-Mixtape-NEO/boards/8Bit-Mixtape-NEO_v1/TaiwanReady/MixTape_BackSide_Copper_v20_Inv_export.png

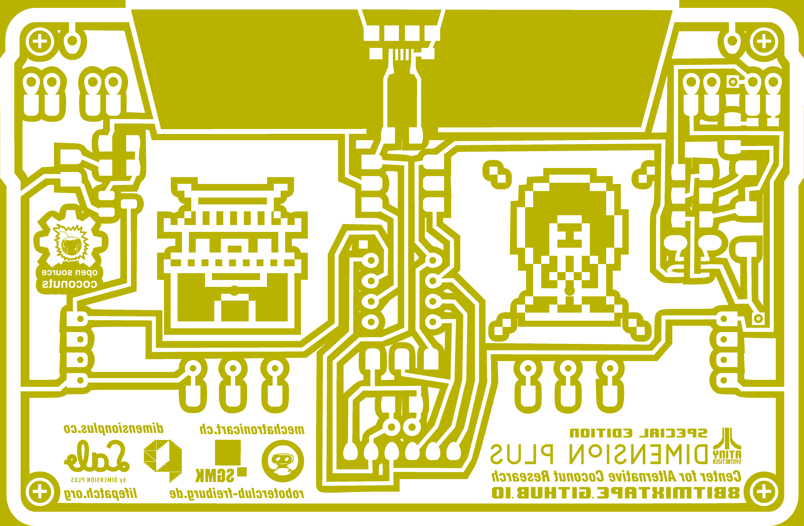
boards/8Bit-Mixtape-NEO_v1/TaiwanReady/MixTape_BackSide_Copper_v20_Inv_export.png
