8BitMixtape/8Bit-Mixtape-NEO/boards/8Bit-NEO_Euro-Rack/8Bit-NEO_EuroRack_designDraft_01.png

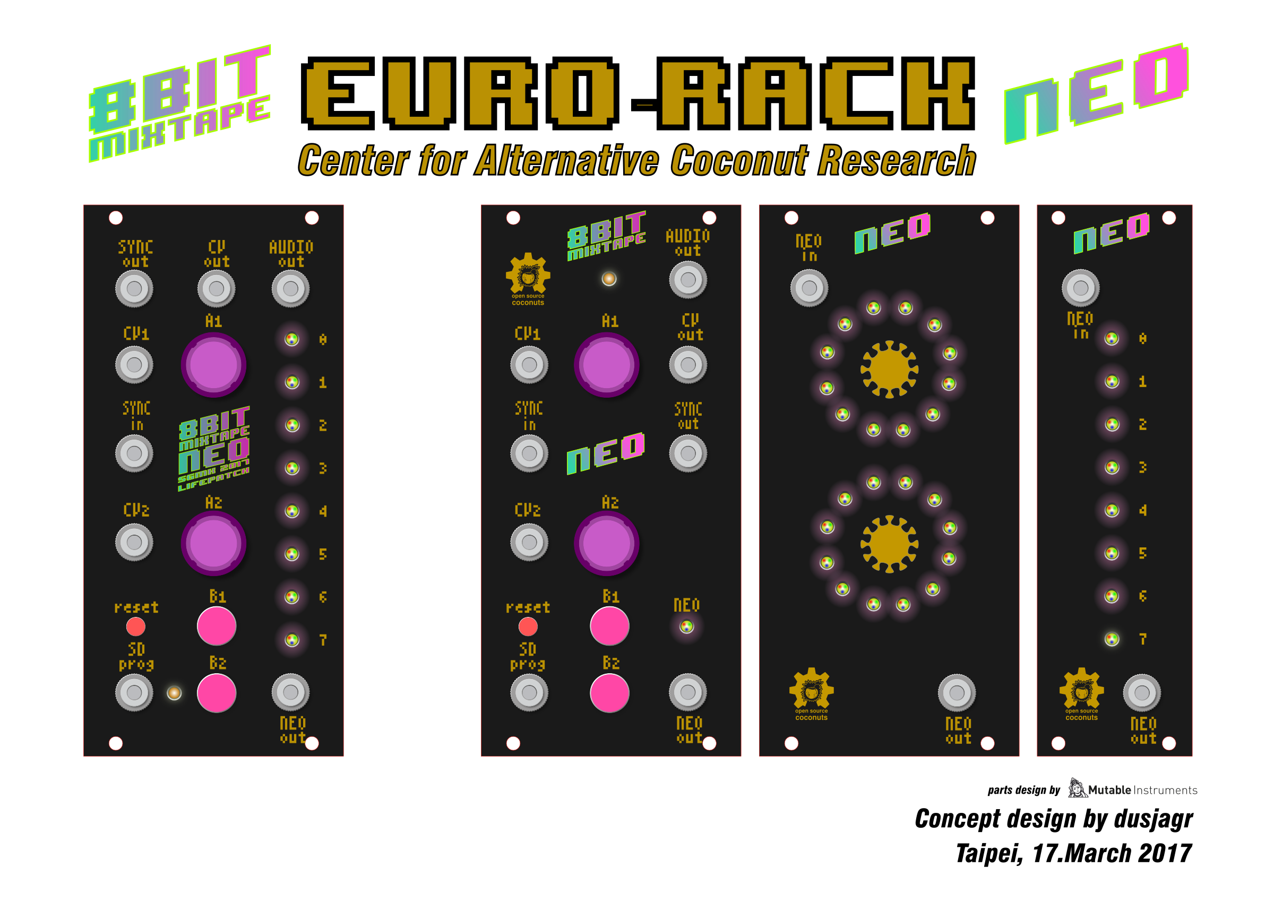
boards/8Bit-NEO_Euro-Rack/8Bit-NEO_EuroRack_designDraft_01.png
