8BitMixtape/8Bit-Mixtape-NEO/boards/DIMI-8/DIMI-8_chistli.png

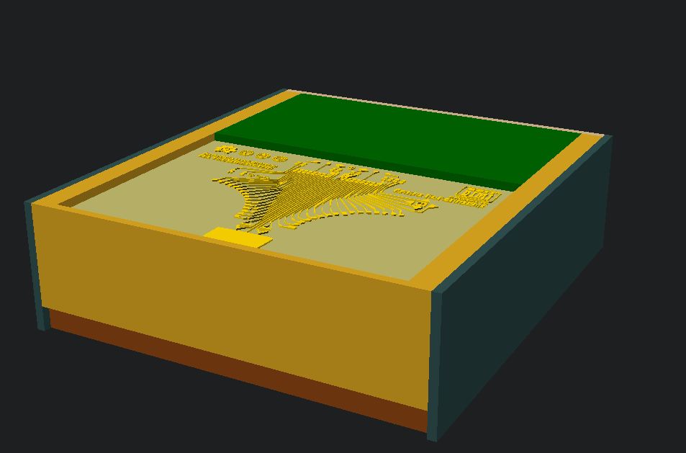
boards/DIMI-8/DIMI-8_chistli.png
