8BitMixtape/8Bit-Mixtape-NEO/boards/DIMI-8/DIMI-8_chistli_1stPrototype.jpg

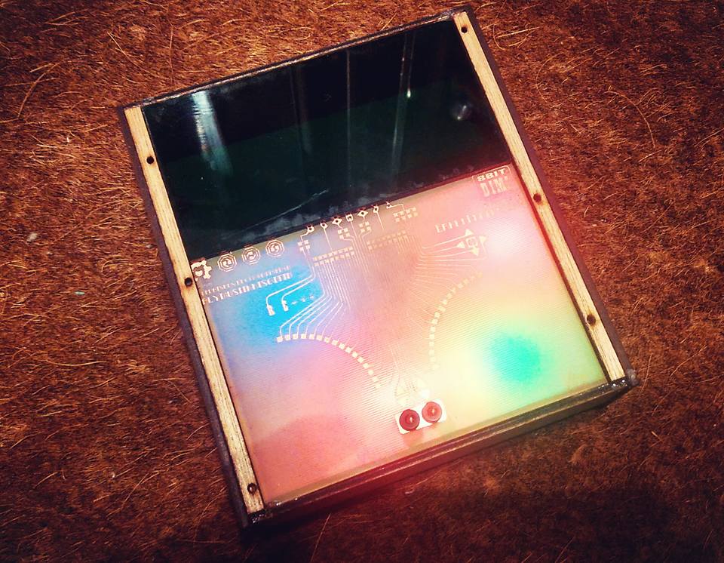
boards/DIMI-8/DIMI-8_chistli_1stPrototype.jpg
