8BitMixtape/8Bit-Mixtape-NEO/boards/DIMI-8/DIMI-8_draft_v03.png

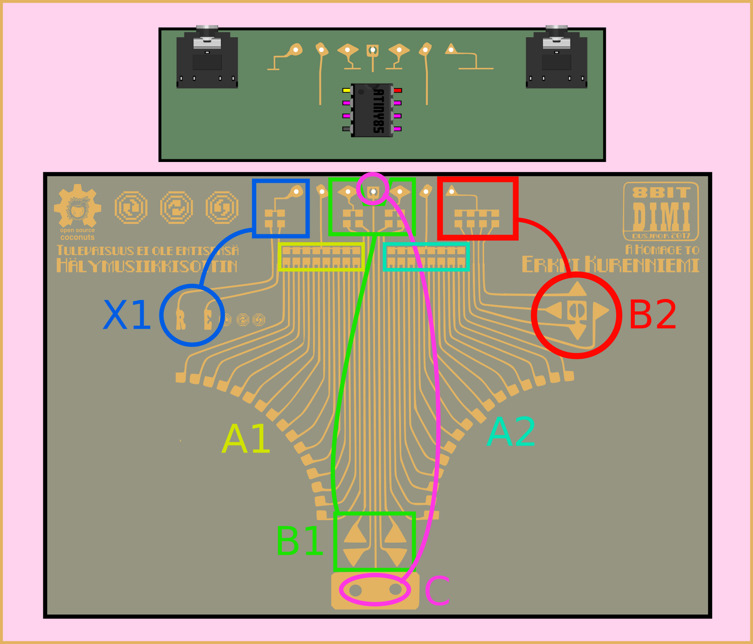
boards/DIMI-8/DIMI-8_draft_v03.png
