8BitMixtape/8Bit-Mixtape-NEO/boards/DIMI-8/DIMI-8_MASK_v02.png

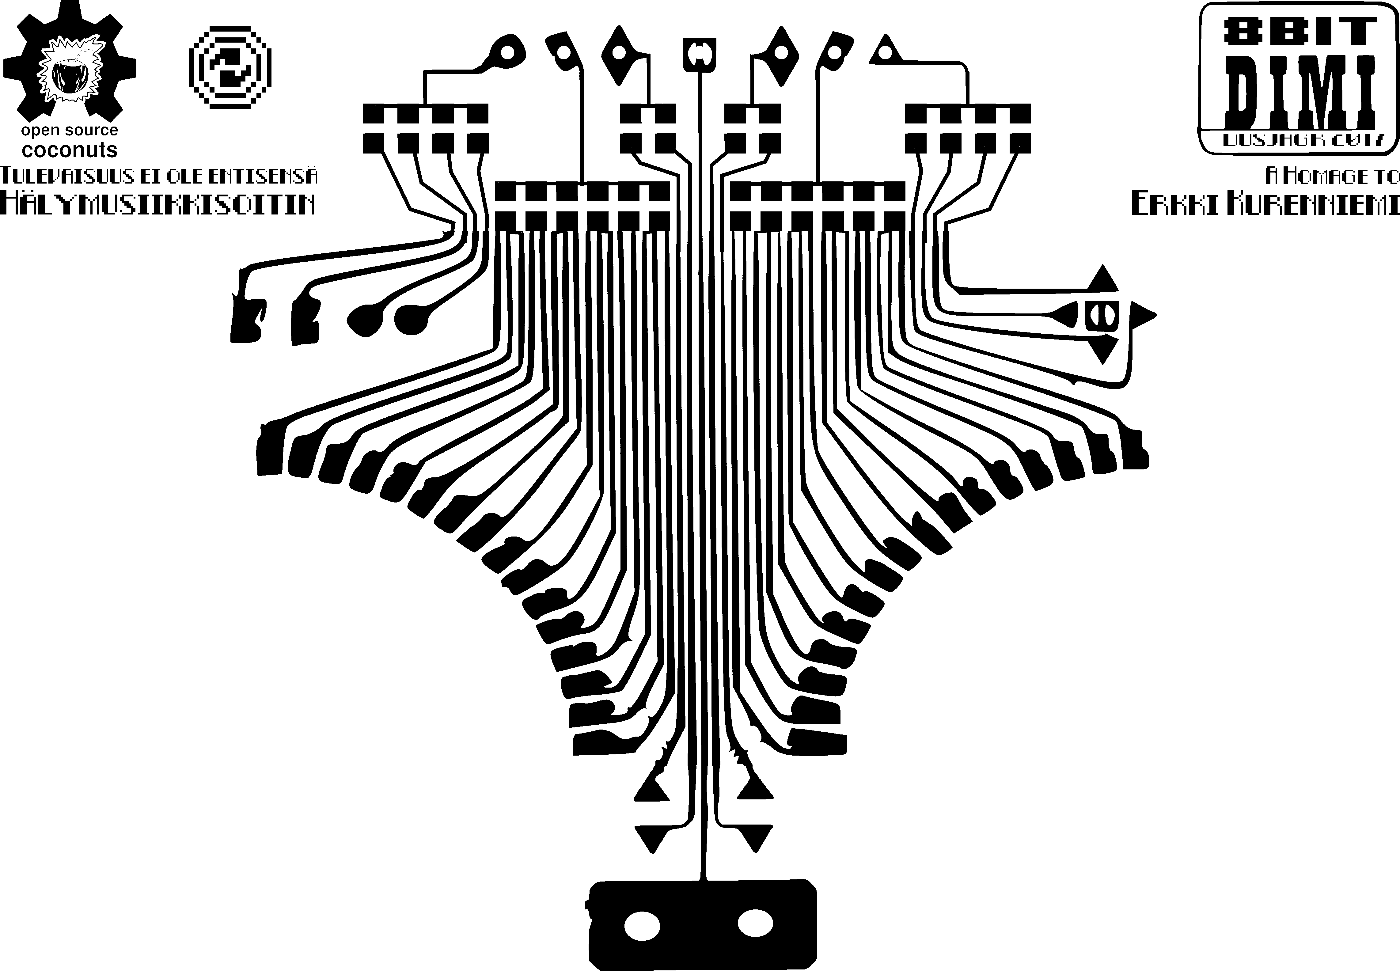
boards/DIMI-8/DIMI-8_MASK_v02.png
