8BitMixtape/8Bit-Mixtape-NEO/boards/DIMI-8/DIMI-original.jpg

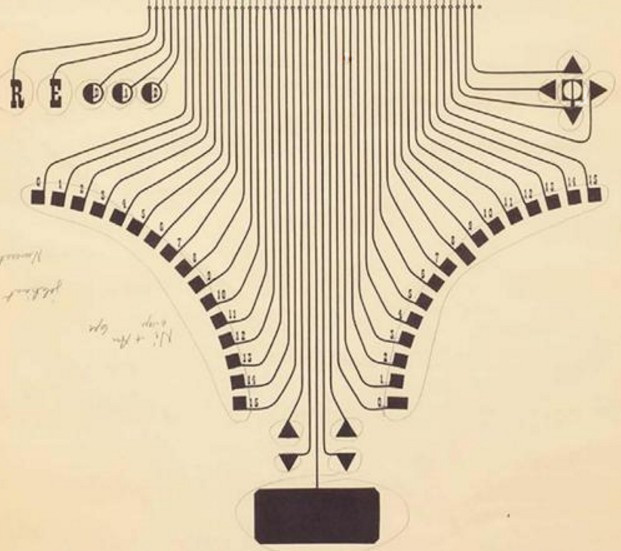
boards/DIMI-8/DIMI-original.jpg
