8BitMixtape/8Bit-Mixtape-NEO/boards/DIMI-8/DIMIs_Secret.png

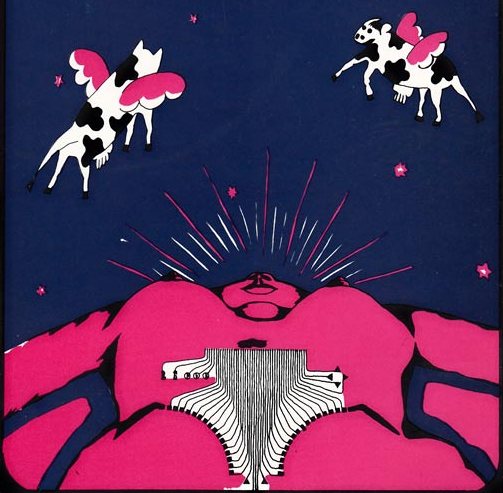
boards/DIMI-8/DIMIs_Secret.png
