8BitMixtape/8Bit-Mixtape-NEO/boards/DIMI-8/Erkki_06.jpg

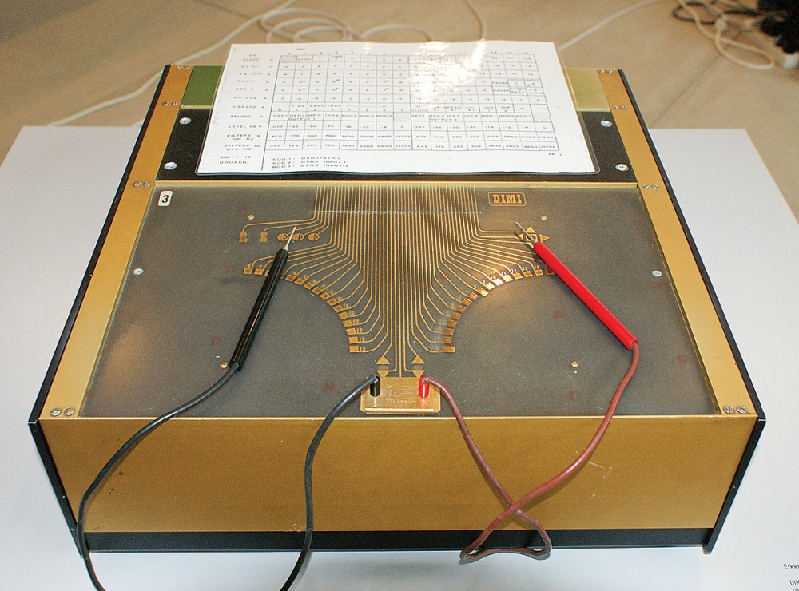
boards/DIMI-8/Erkki_06.jpg
