8BitMixtape/8Bit-Mixtape-NEO/boards/DIMI-8/juuso-erkki.jpg

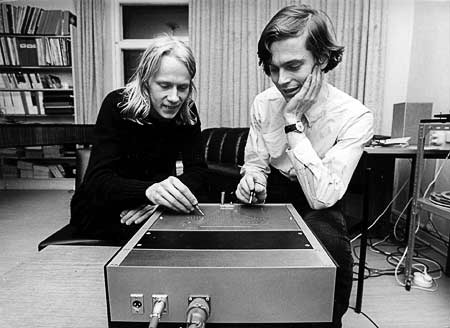
boards/DIMI-8/juuso-erkki.jpg
