8BitMixtape/8Bit-Mixtape-NEO/boards/DIMI-8/PAM8302_diagram.jpg

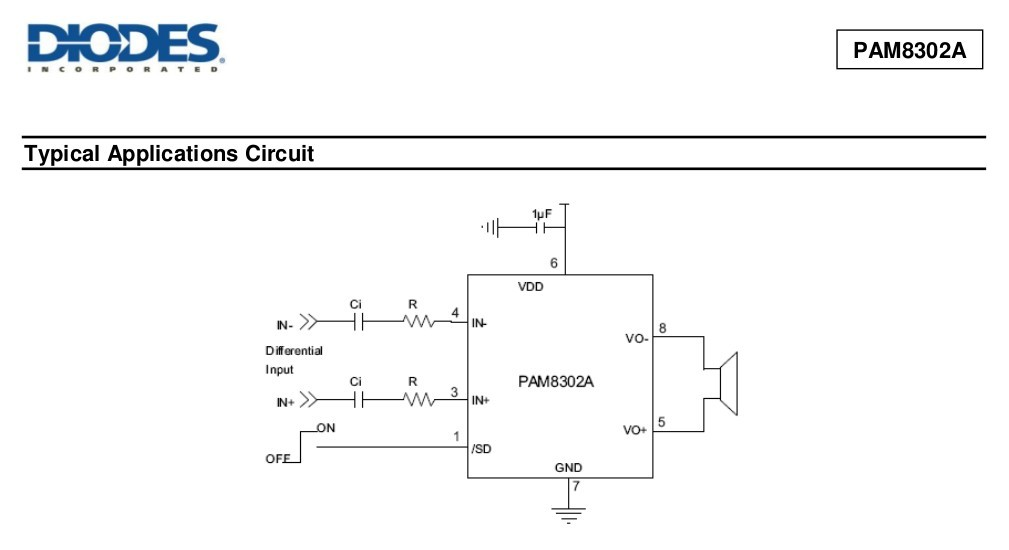
boards/DIMI-8/PAM8302_diagram.jpg
