8BitMixtape/8Bit-Mixtape-NEO/boards/DIMI-8/X5176_label_01.jpg

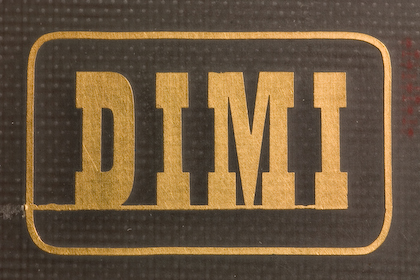
boards/DIMI-8/X5176_label_01.jpg
