8BitMixtape/8Bit-Mixtape-NEO/boards/DIMI-8/youtube_pinkSynth.jpg

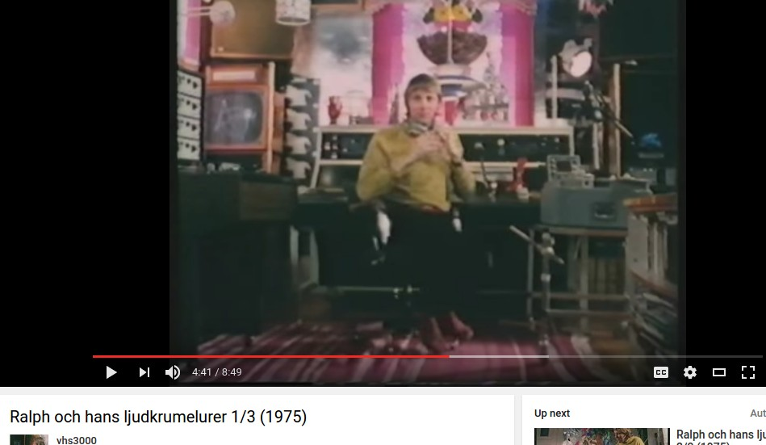
boards/DIMI-8/youtube_pinkSynth.jpg
