8BitMixtape/8Bit-Mixtape-NEO/boards/FirstPrototype_Neo03/attiny_prototyping_tokyoHotel.jpg

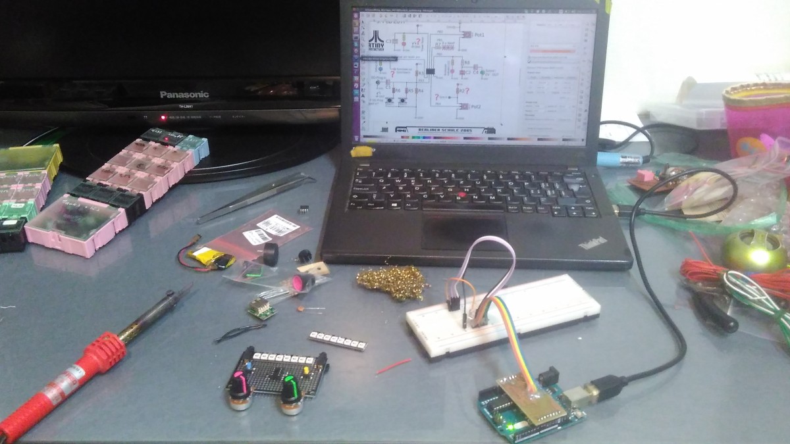
boards/FirstPrototype_Neo03/attiny_prototyping_tokyoHotel.jpg
