8BitMixtape/8Bit-Mixtape-NEO/boards/images_schematics/8Bit-MixTape_schematics2.png

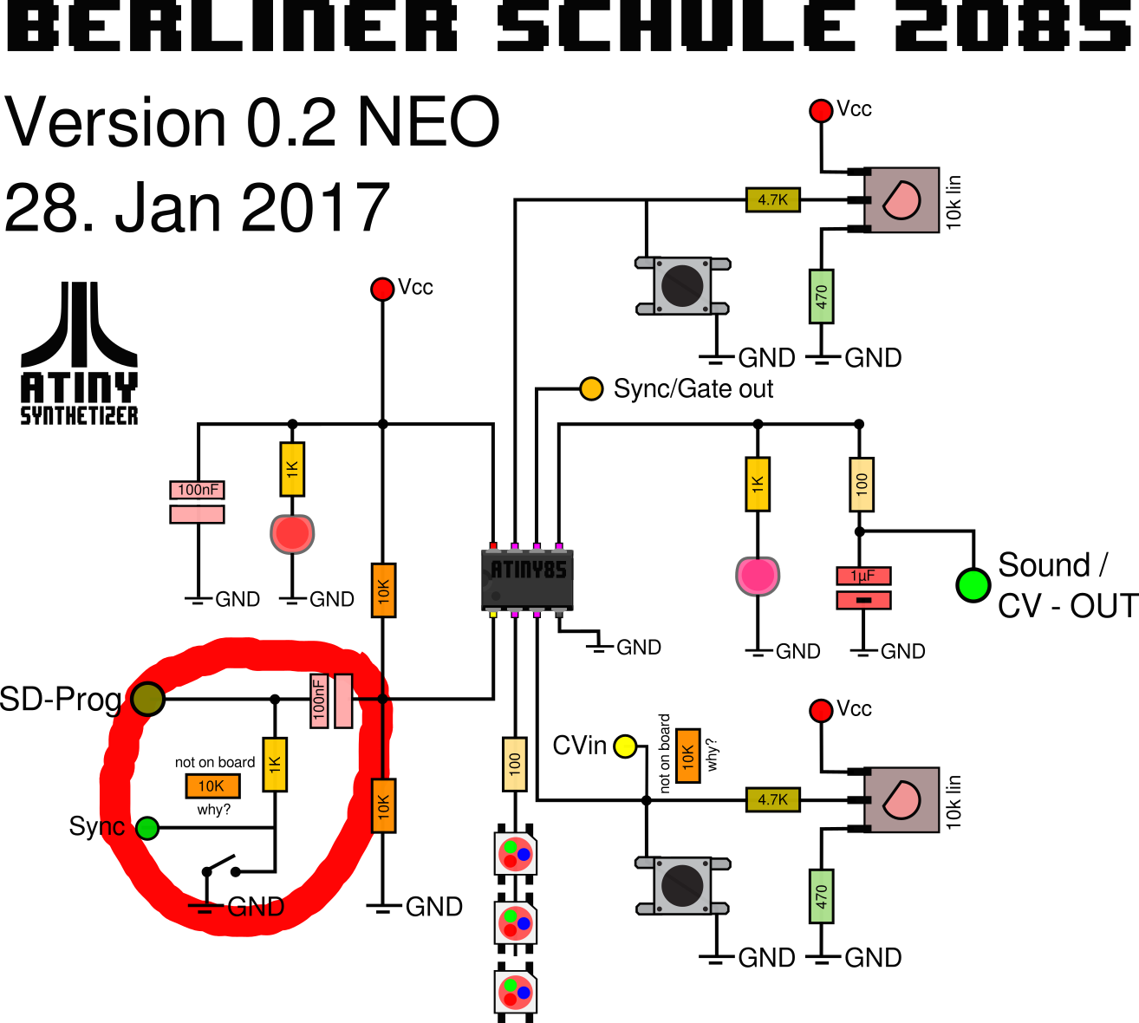
boards/images_schematics/8Bit-MixTape_schematics2.png
