8BitMixtape/8Bit-Mixtape-NEO/boards/images_schematics/8BitMixTapeClone.PNG

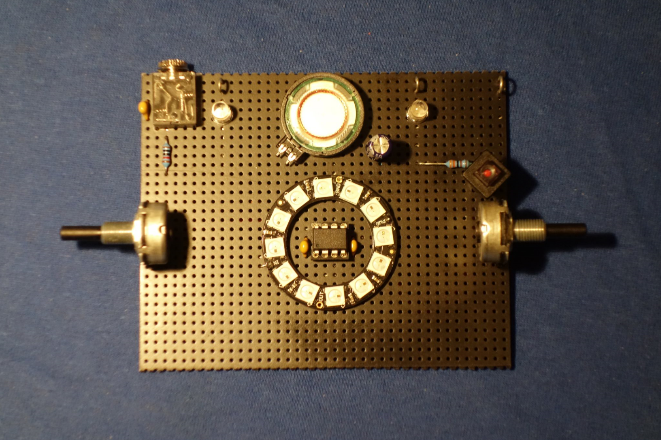
boards/images_schematics/8BitMixTapeClone.PNG
