8BitMixtape/8Bit-Mixtape-NEO/boards/images_schematics/85SoundProg_MixTape_V03-NEO_RedChicken.jpg

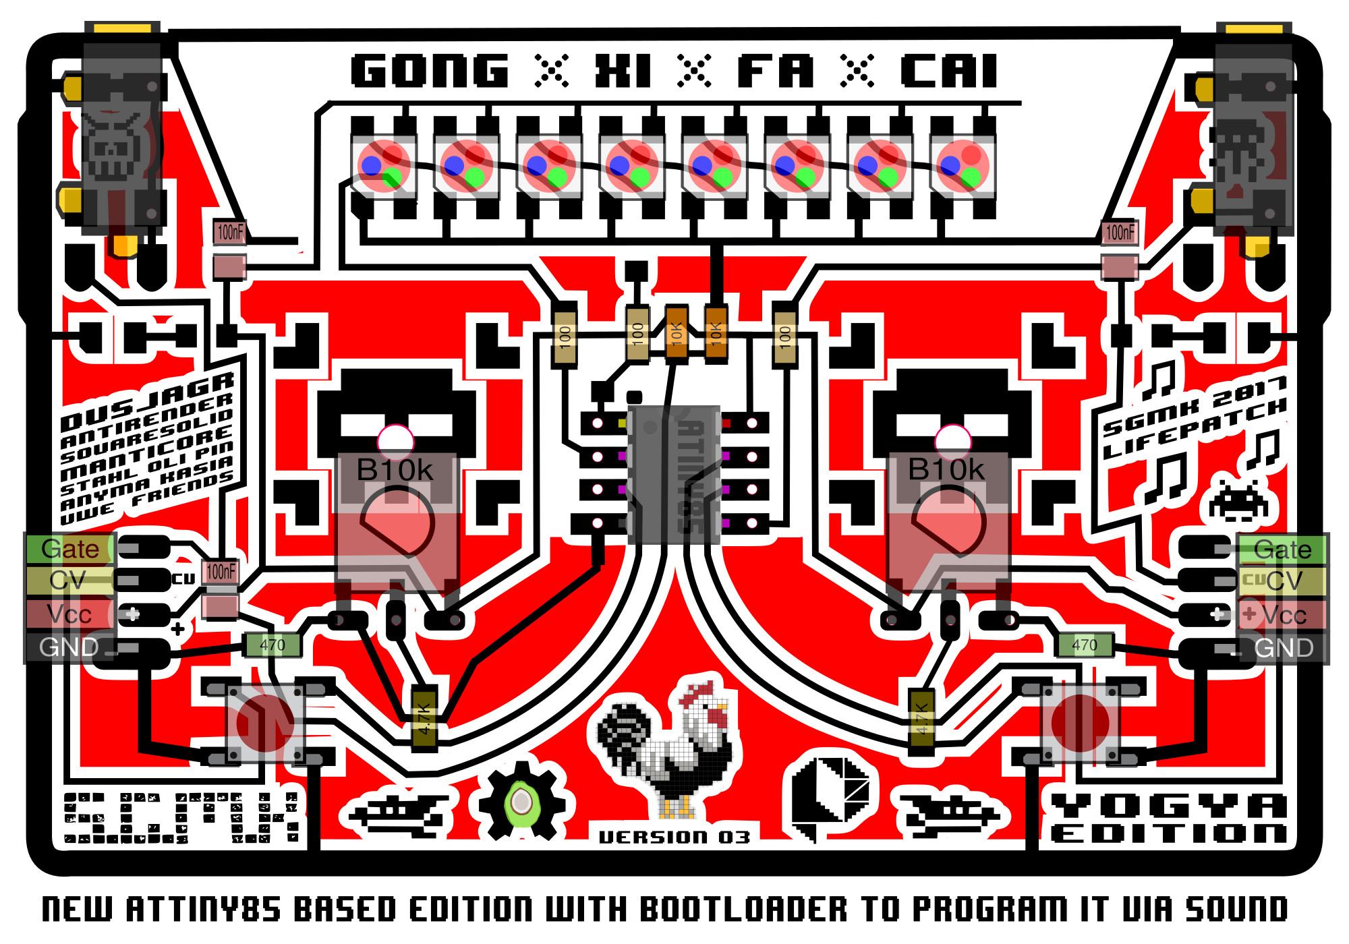
boards/images_schematics/85SoundProg_MixTape_V03-NEO_RedChicken.jpg
