8BitMixtape/8Bit-Mixtape-NEO/boards/images_schematics/advanced_plugology_breakfast.jpg

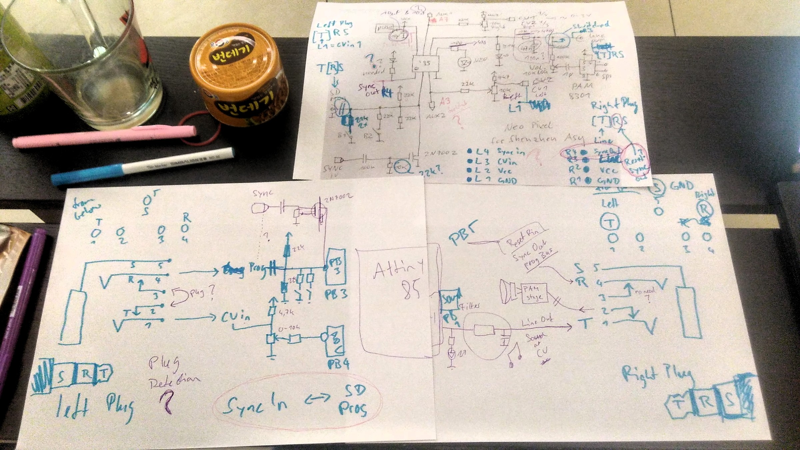
boards/images_schematics/advanced_plugology_breakfast.jpg
