8BitMixtape/8Bit-Mixtape-NEO/boards/images_schematics/advanced_plugology_v13.jpg

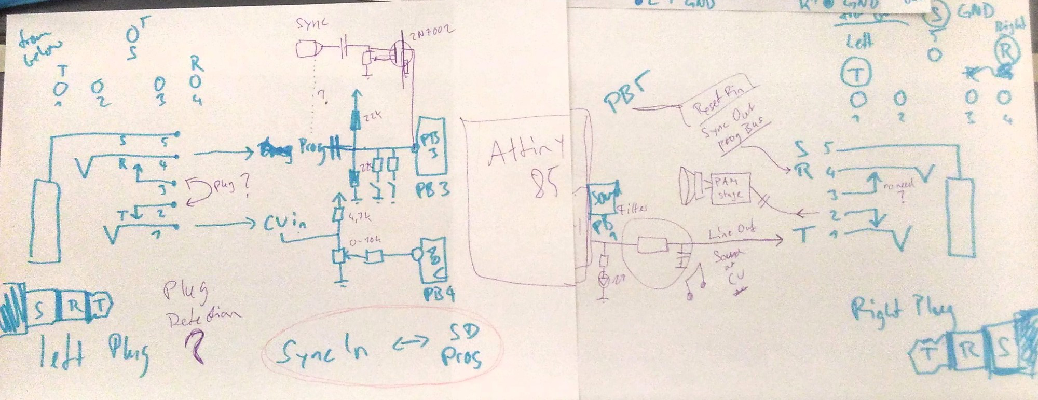
boards/images_schematics/advanced_plugology_v13.jpg
