8BitMixtape/8Bit-Mixtape-NEO/boards/images_schematics/dusjagr_prototype_tokyo.jpg

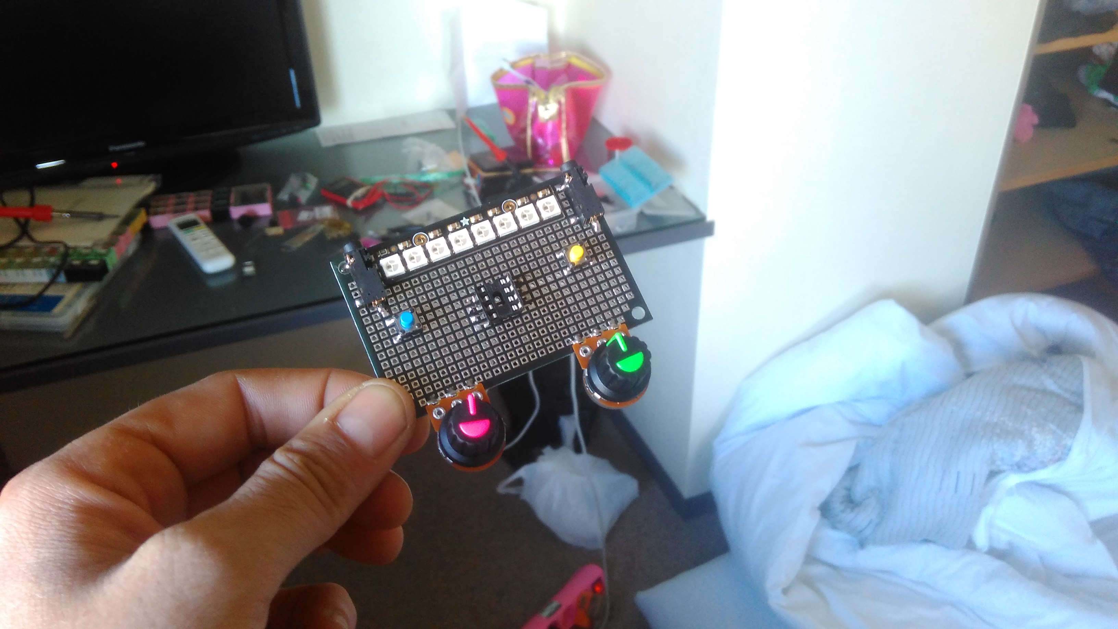
boards/images_schematics/dusjagr_prototype_tokyo.jpg
