8BitMixtape/8Bit-Mixtape-NEO/boards/images_schematics/EtchingBoards_ChineseStyle.jpg

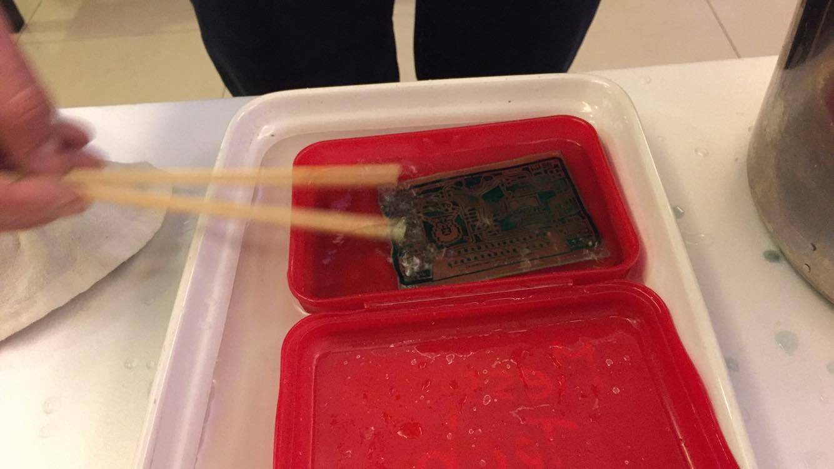
boards/images_schematics/EtchingBoards_ChineseStyle.jpg
