8BitMixtape/8Bit-Mixtape-NEO/boards/images_schematics/kicad_geeking.jpg

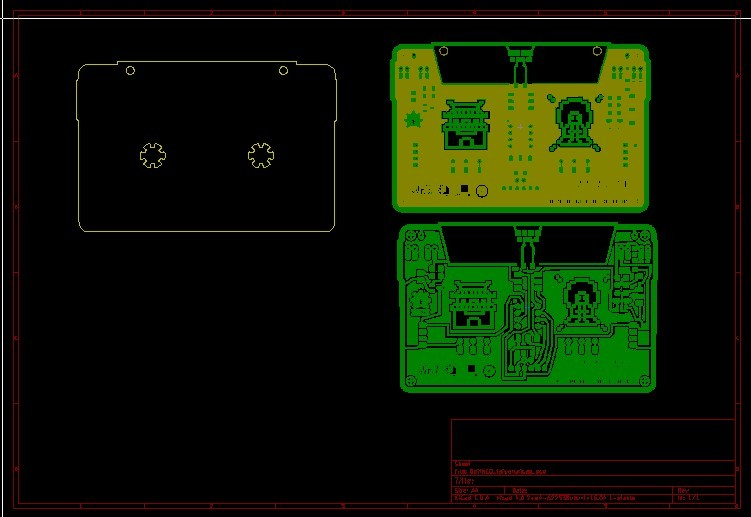
boards/images_schematics/kicad_geeking.jpg
