8BitMixtape/8Bit-Mixtape-NEO/boards/images_schematics/NeoCoco_ZagrebPride.jpg

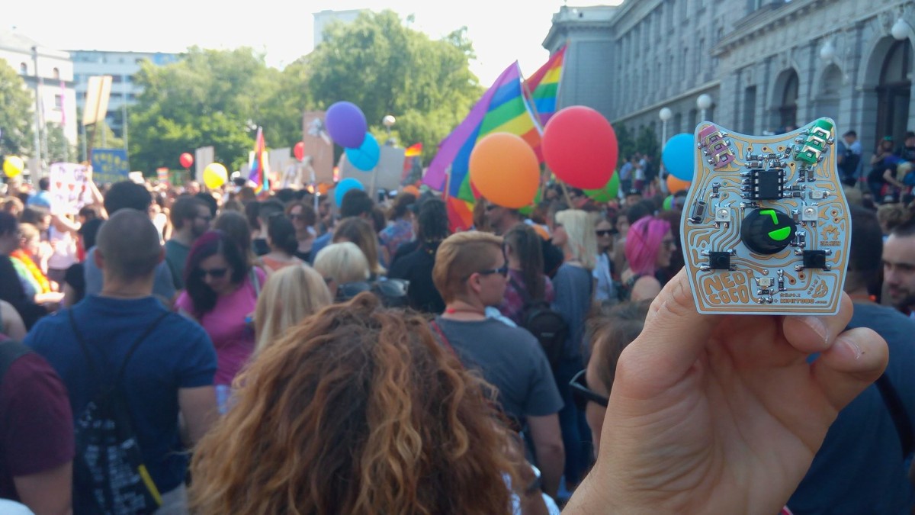
boards/images_schematics/NeoCoco_ZagrebPride.jpg
