8BitMixtape/8Bit-Mixtape-NEO/boards/images_schematics/NeopixelV095_uwe_updates.jpg

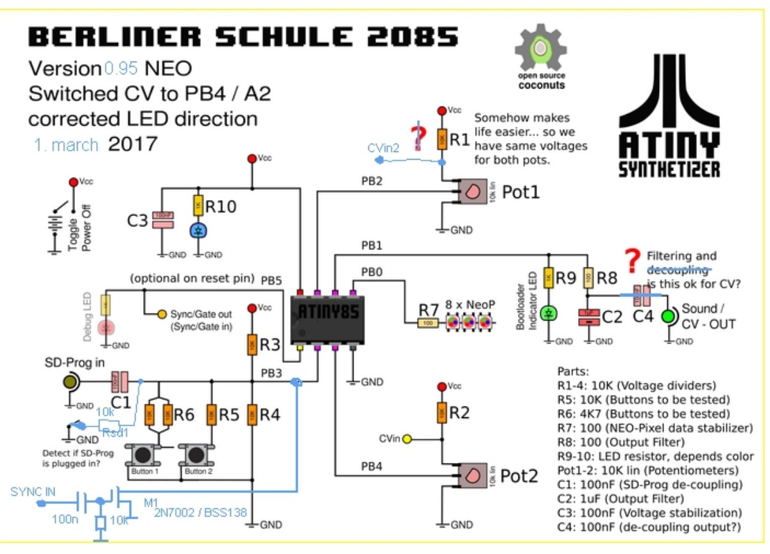
boards/images_schematics/NeopixelV095_uwe_updates.jpg
