8BitMixtape/8Bit-Mixtape-NEO/boards/images_schematics/NeopixelV096_schematics.jpg

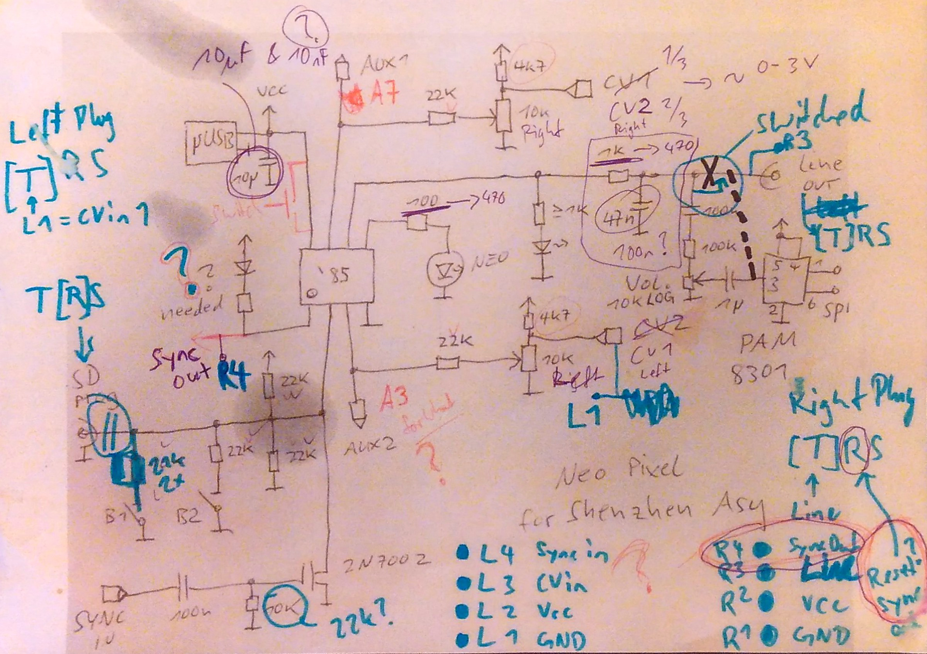
boards/images_schematics/NeopixelV096_schematics.jpg
