8BitMixtape/8Bit-Mixtape-NEO/boards/images_schematics/NEOshenzSCH_Uwe_v1_2.jpg

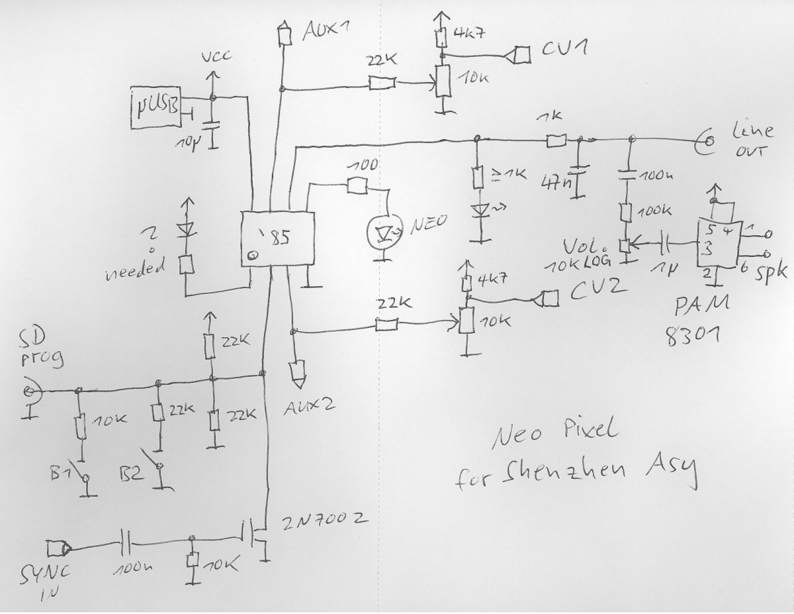
boards/images_schematics/NEOshenzSCH_Uwe_v1_2.jpg
