8BitMixtape/8Bit-Mixtape-NEO/boards/images_schematics/Schematic_v096_8BitMixtape-NEO.png

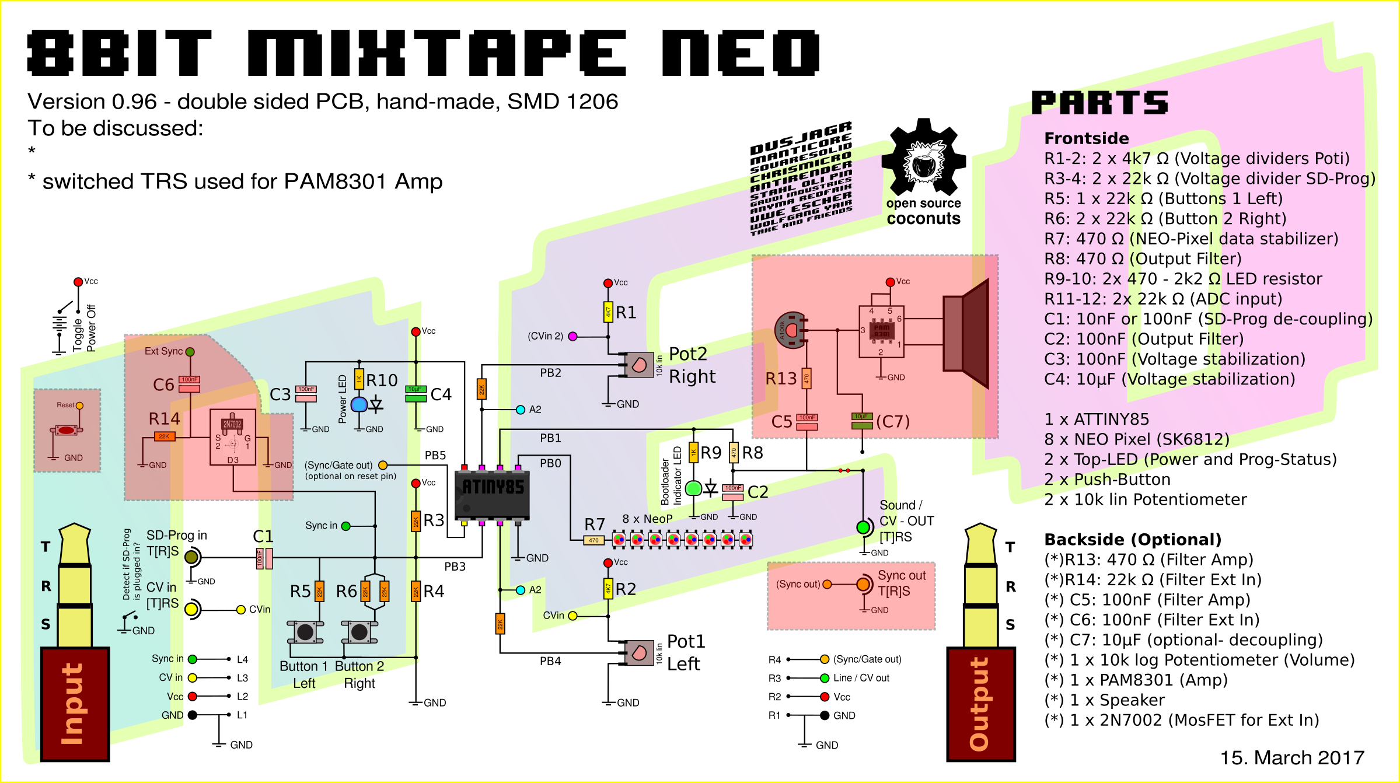
boards/images_schematics/Schematic_v096_8BitMixtape-NEO.png
