8BitMixtape/8Bit-Mixtape-NEO/boards/images_schematics/Schematics_85SoundProg_MixTape_V09.png

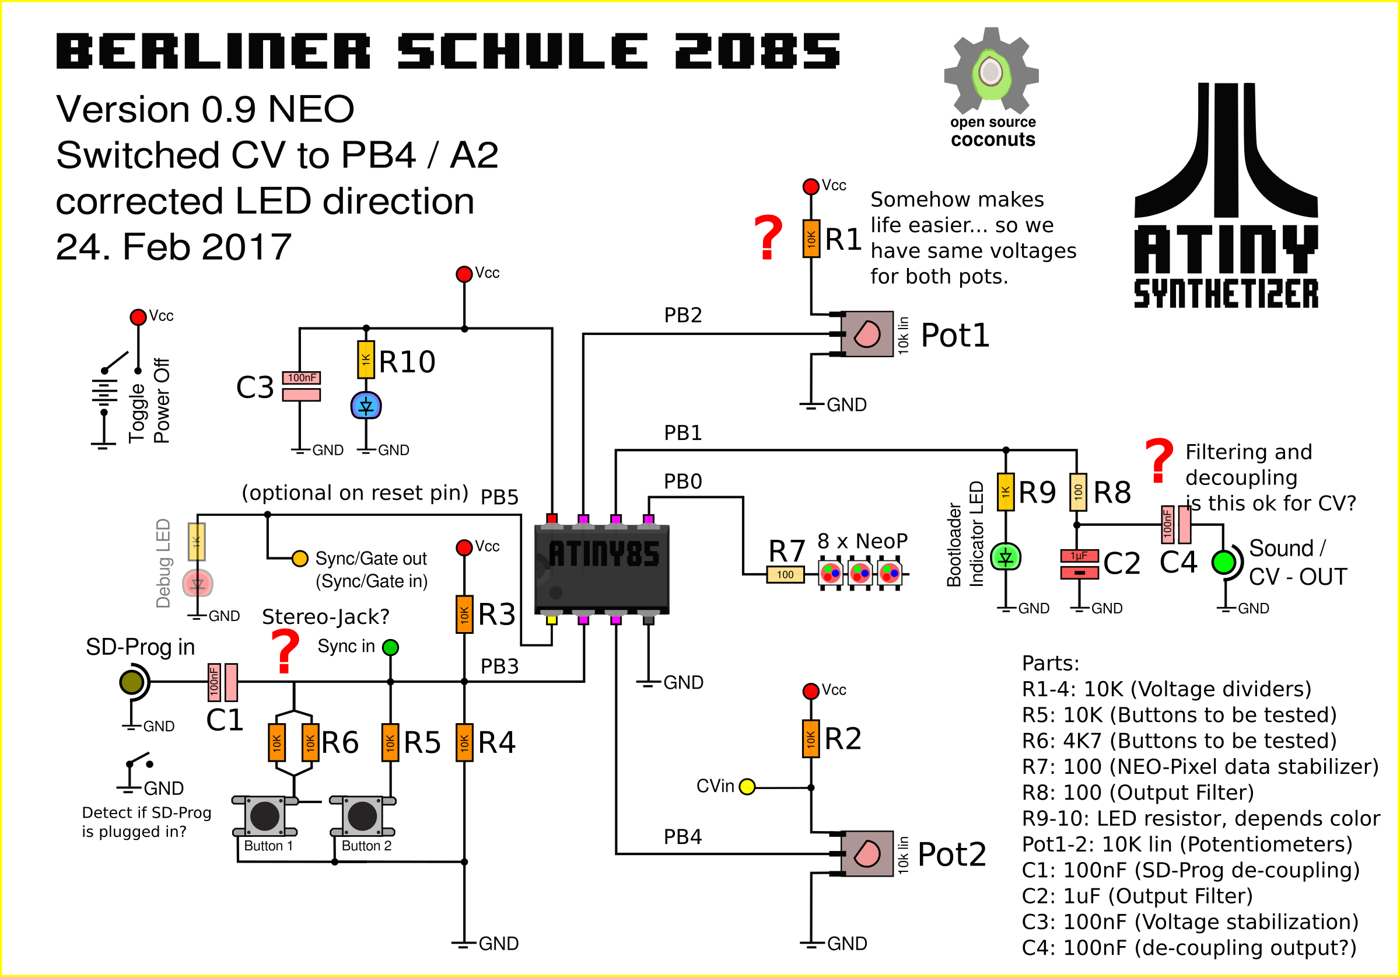
boards/images_schematics/Schematics_85SoundProg_MixTape_V09.png
