8BitMixtape/8Bit-Mixtape-NEO/boards/images_schematics/SelfMade_NEO-Coconnuts.png

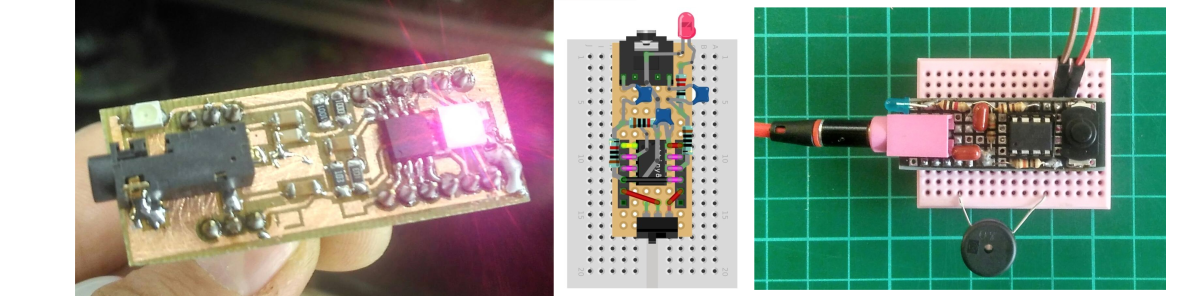
boards/images_schematics/SelfMade_NEO-Coconnuts.png
