8BitMixtape/8Bit-Mixtape-NEO/boards/NEO-Coconut/Eschers_garlampli_gold.png

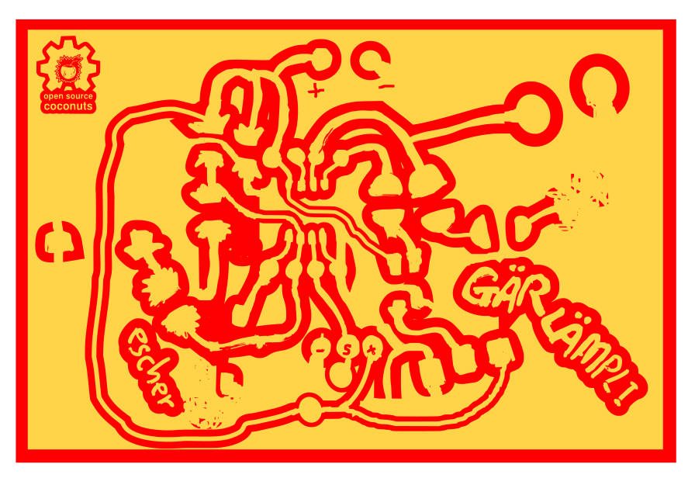
boards/NEO-Coconut/Eschers_garlampli_gold.png
