8BitMixtape/8Bit-Mixtape-NEO/boards/NEO-Coconut/Eschers_GärLämpli.jpg

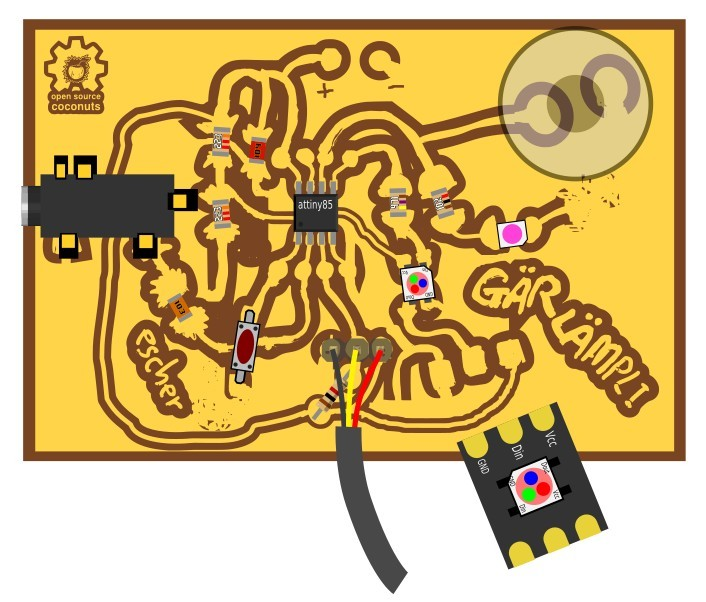
boards/NEO-Coconut/Eschers_GärLämpli.jpg
