8BitMixtape/8Bit-Mixtape-NEO/boards/NEO-Coconut/Gär_Lämpli_prototype.jpg

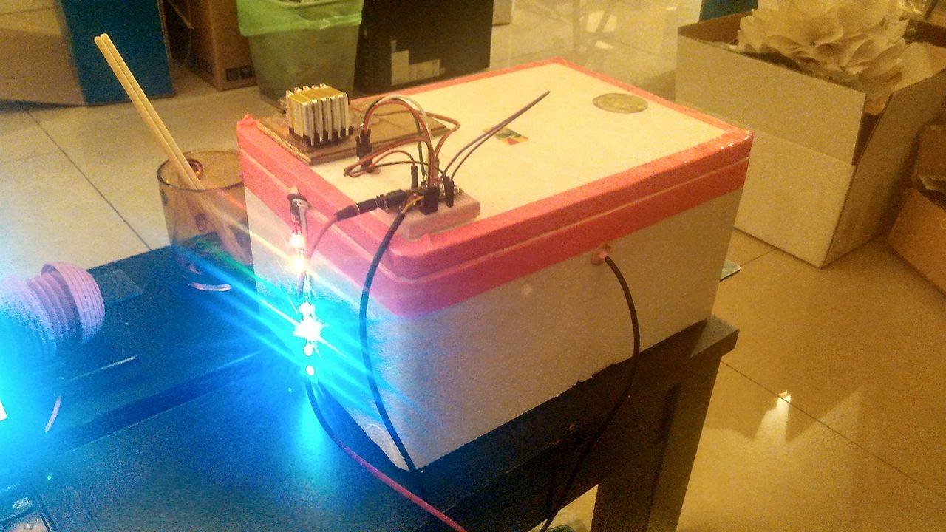
boards/NEO-Coconut/Gär_Lämpli_prototype.jpg
