8BitMixtape/8Bit-Mixtape-NEO/boards/NEO-Coconut/GärLämpli_laminates_schematics.png

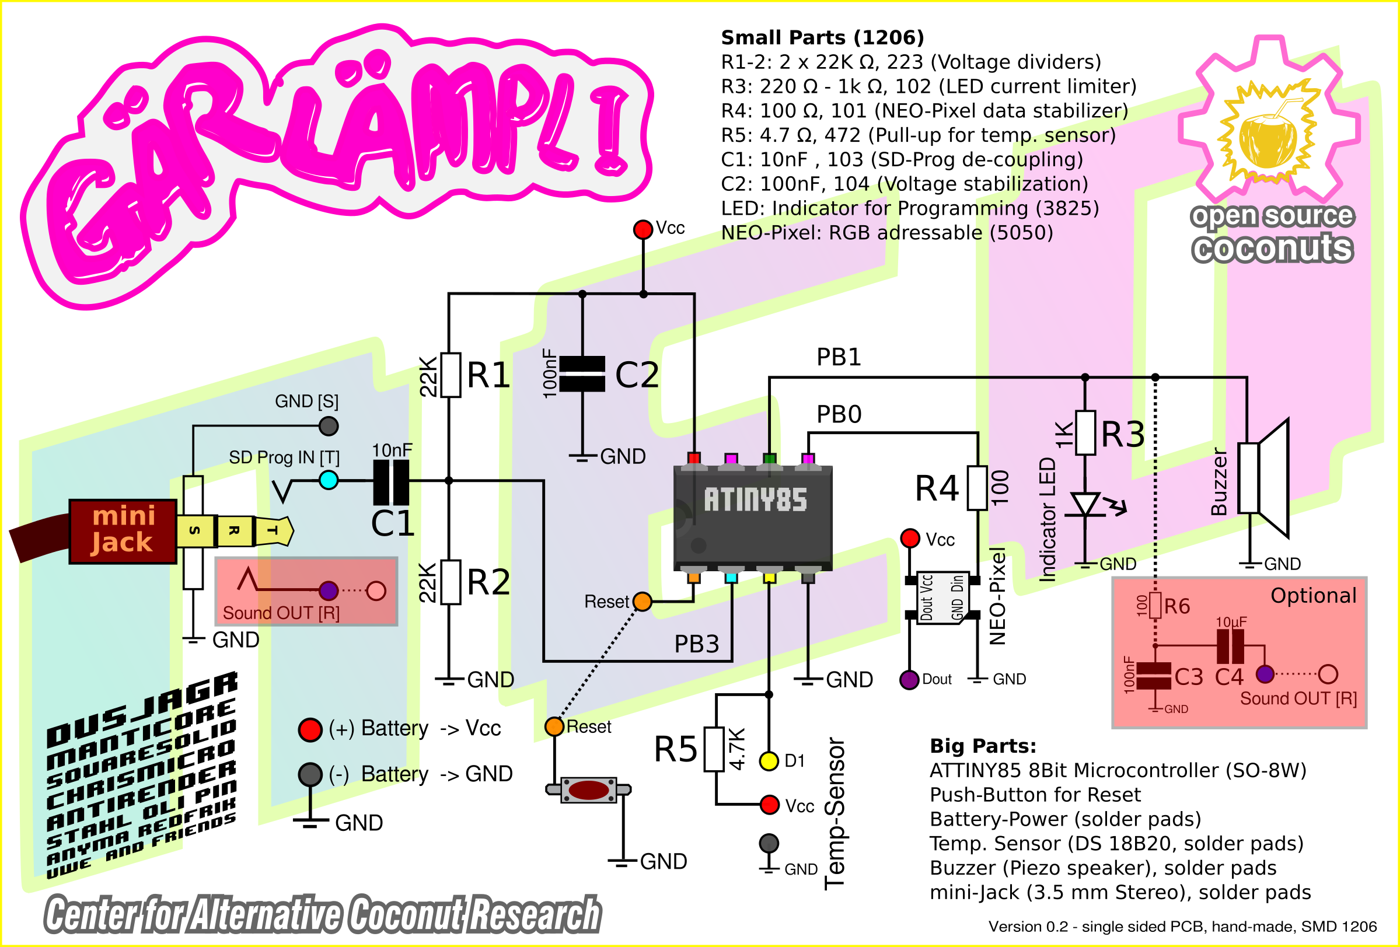
boards/NEO-Coconut/GärLämpli_laminates_schematics.png
