8BitMixtape/8Bit-Mixtape-NEO/boards/NEO-Coconut/GärLämpli_rescalings.png

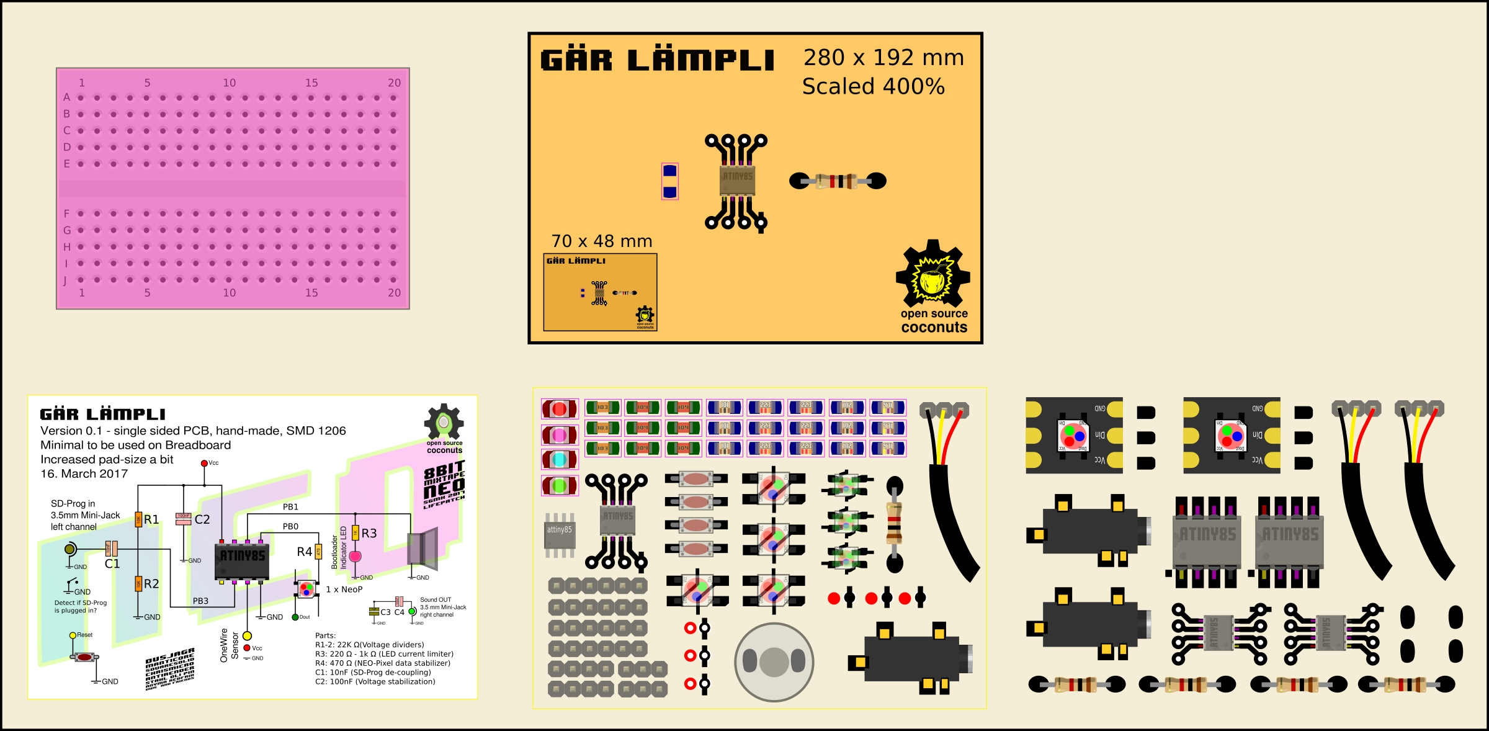
boards/NEO-Coconut/GärLämpli_rescalings.png
