8BitMixtape/8Bit-Mixtape-NEO/boards/NEO-Coconut/Jessies_garlampli_MASK.jpg

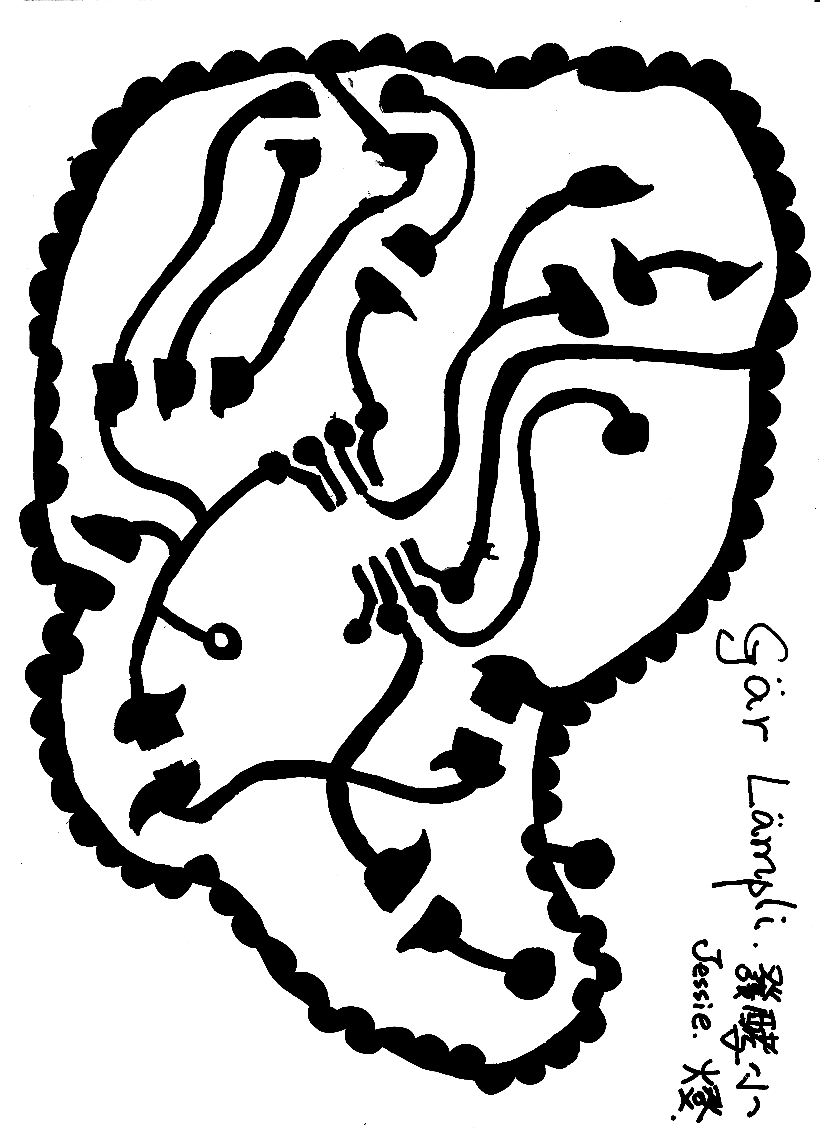
boards/NEO-Coconut/Jessies_garlampli_MASK.jpg
