8BitMixtape/8Bit-Mixtape-NEO/boards/NEO_overview_boards.jpg

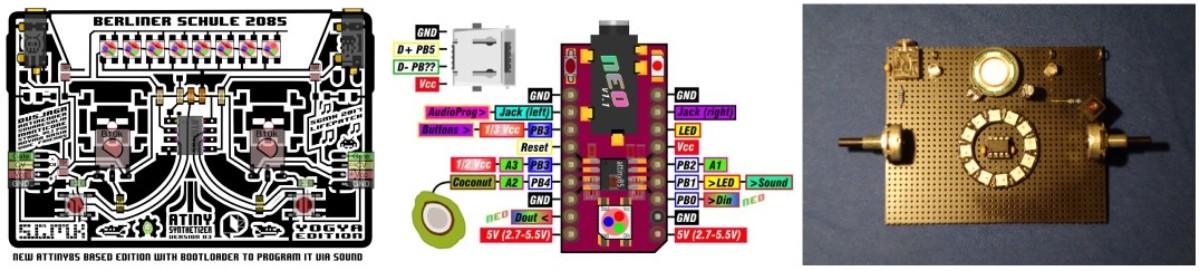
boards/NEO_overview_boards.jpg
