8BitMixtape/8Bit-Mixtape-NEO/boards/packaging/mixtape_packaging_box_02.jpg

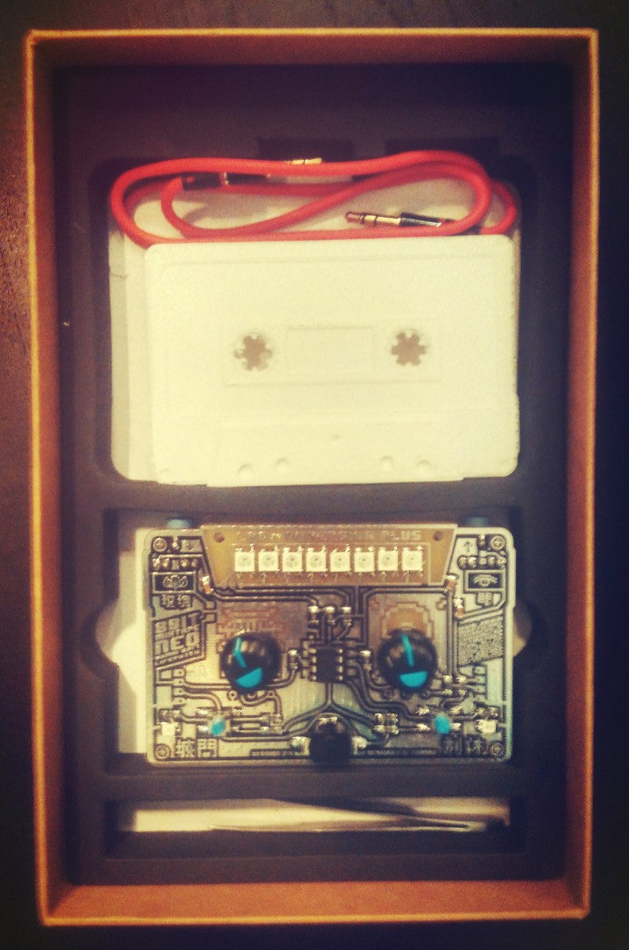
boards/packaging/mixtape_packaging_box_02.jpg
