8BitMixtape/8Bit-Mixtape-NEO/boards/packaging/mixtape_SMD-Kit_package.jpg

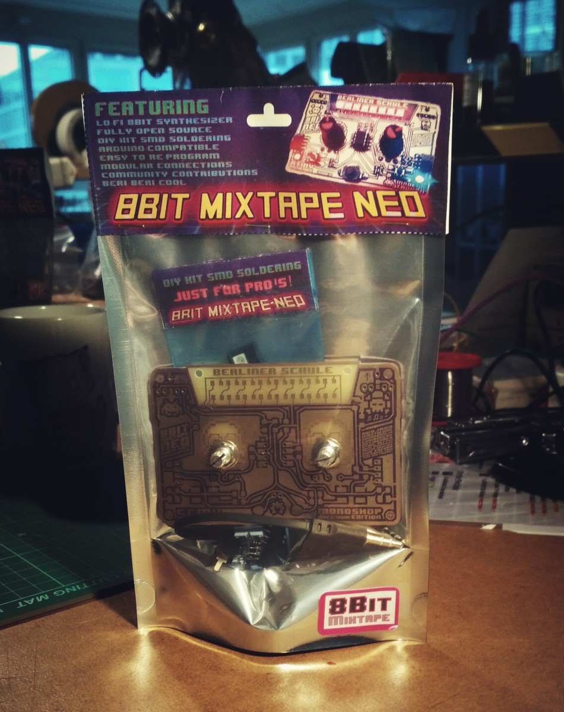
boards/packaging/mixtape_SMD-Kit_package.jpg
