8BitMixtape/8Bit-Mixtape-NEO/boards/packaging/Mixtape_TutliTopSleeve.jpg

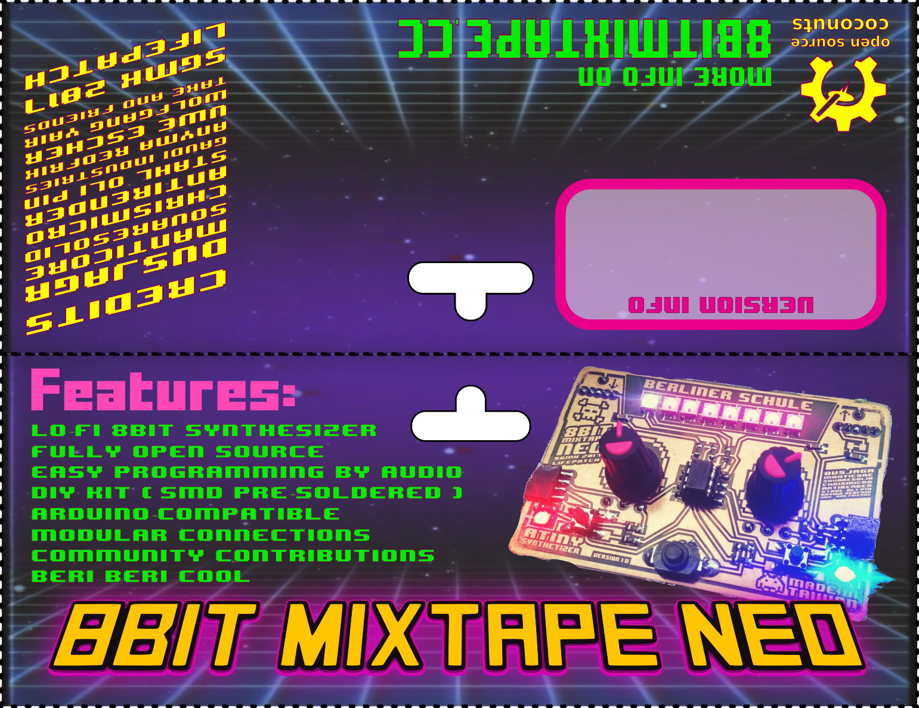
boards/packaging/Mixtape_TutliTopSleeve.jpg
