8BitMixtape/8Bit-Mixtape-NEO/Code/_053_IrqPcControlSynth/java/miniSynth.PNG

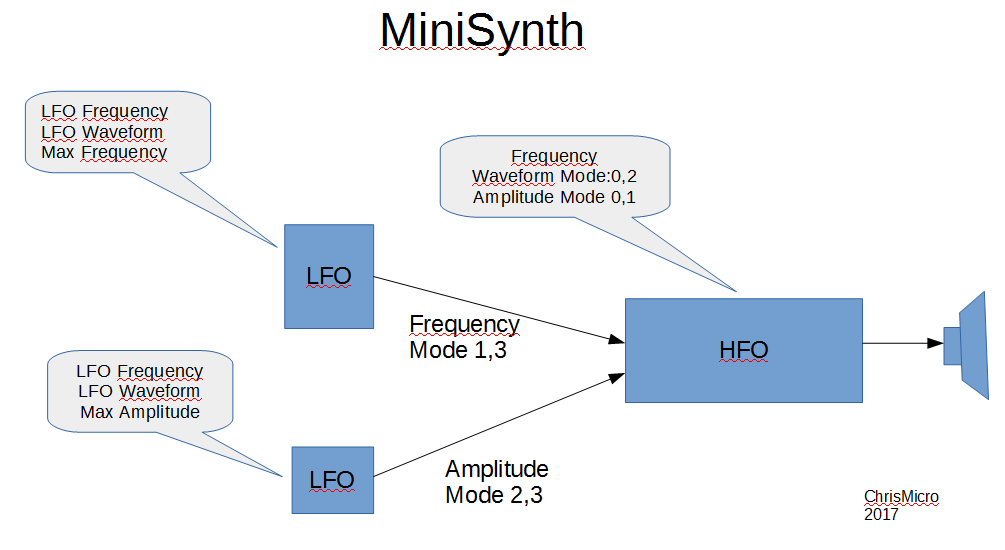
Code/_053_IrqPcControlSynth/java/miniSynth.PNG
