8BitMixtape/8Bit-Mixtape-NEO/Code/hex2wav_asciiART2.jpg

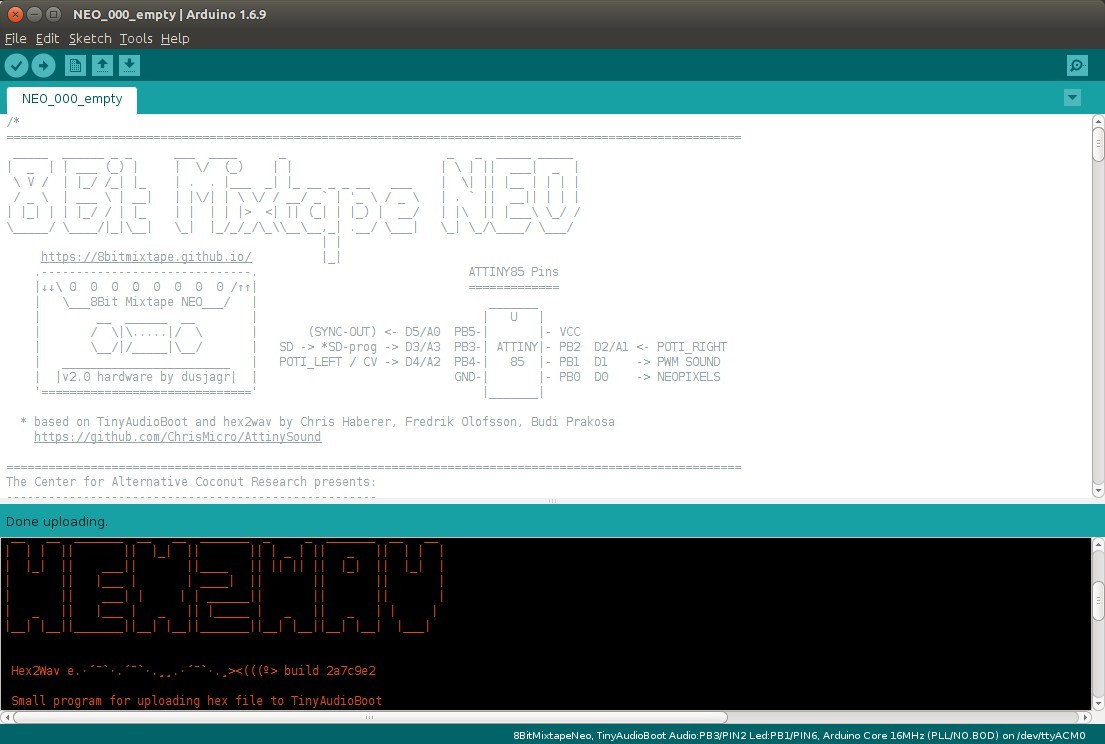
Code/hex2wav_asciiART2.jpg
