8BitMixtape/8Bit-Mixtape-NEO/Code/hex2wav_asciiART.png

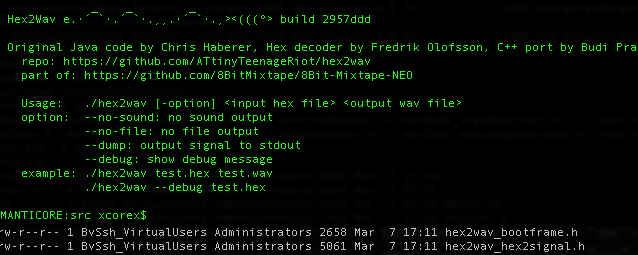
Code/hex2wav_asciiART.png
