8BitMixtape/8Bit-Mixtape-NEO/boards/3d-files/MixTape_Case_VerMar19_05.stl

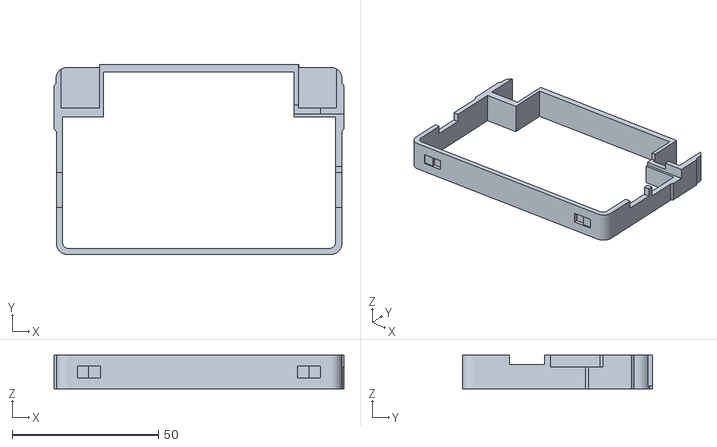
[picture p160: CAD file, 2019-04-11]
boards/3d-files/MixTape_Case_VerMar19_05.stl
99.0 x 64.8 x 11.5
