8BitMixtape/8Bit-Mixtape-NEO/boards/8Bit-NEO-Casing-Manticore-Build/3D_mixTape_Rahmli top.stl

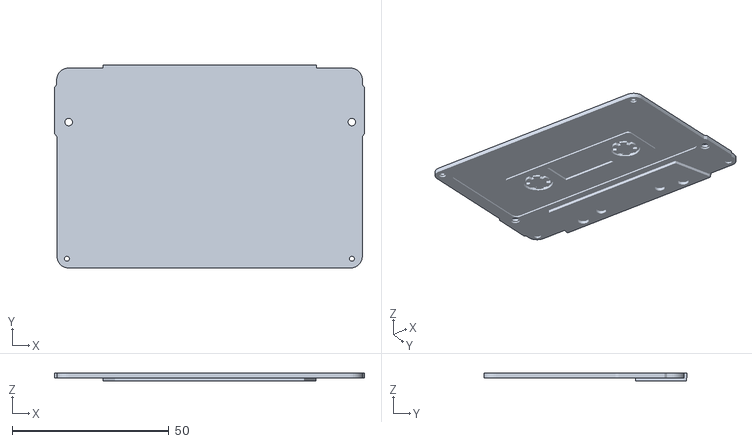
[picture p161: CAD file, 2018-01-22]
boards/8Bit-NEO-Casing-Manticore-Build/3D_mixTape_Rahmli top.stl
99.0 x 64.8 x 2.60
