8BitMixtape/8Bit-Mixtape-NEO/boards/DIMI-8/interace_anyma.dxf

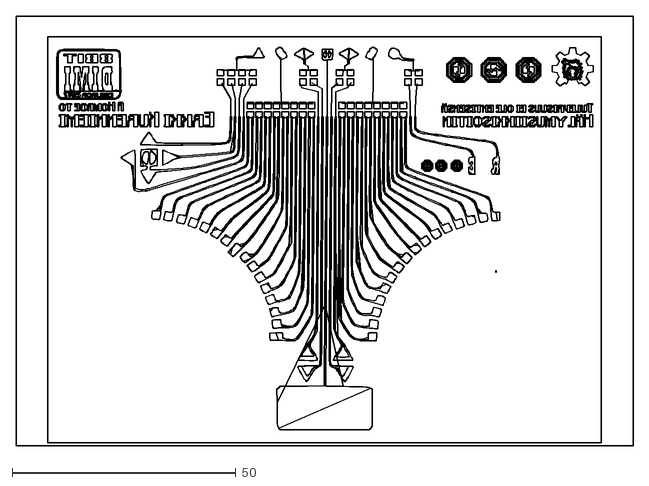
[picture p162: CAD file, 2017-06-10]
boards/DIMI-8/interace_anyma.dxf
138.0 x 96.0
