8BitMixtape/8Bit-Mixtape-NEO/boards/DIMI-8/unagi_border.dxf

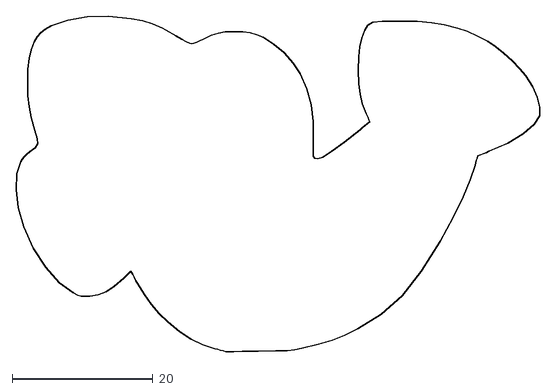
[picture p163: CAD file, 2017-04-11]
boards/DIMI-8/unagi_border.dxf
74.4 x 47.6
