8BitMixtape/8Bit-Mixtape-NEO/boards/3d-files/MixTape_Top_VerMar19_05.stl

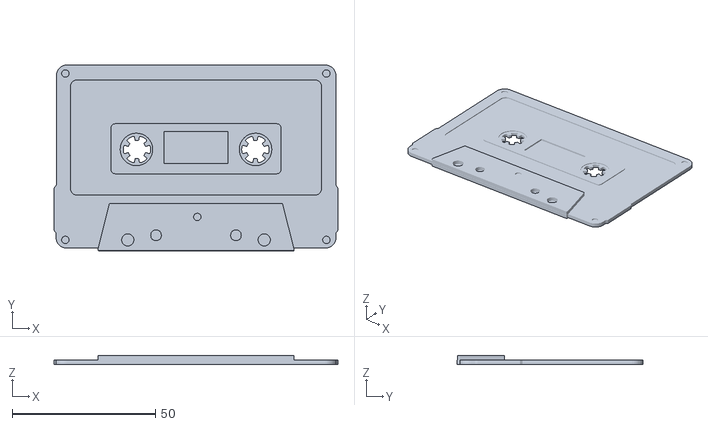
[picture p164: CAD file, 2019-04-11]
boards/3d-files/MixTape_Top_VerMar19_05.stl
99.0 x 64.8 x 3.10
