8BitMixtape/8Bit-Mixtape-NEO/boards/DIMI-8/interace.dxf

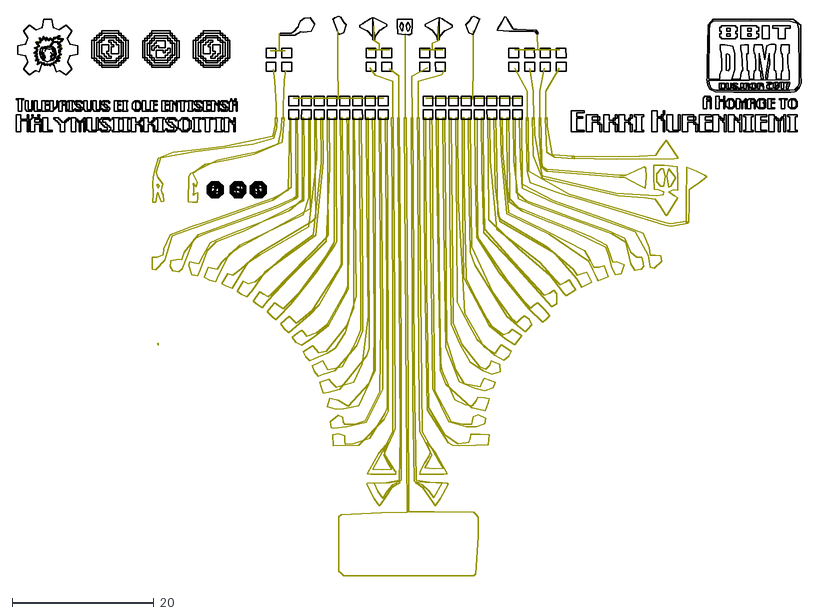
[picture p165: CAD file, 2017-04-11]
boards/DIMI-8/interace.dxf
110.8 x 79.0
