8BitMixtape/8Bit-Mixtape-NEO/boards/DIMI-8/DIMI_chistli.dxf

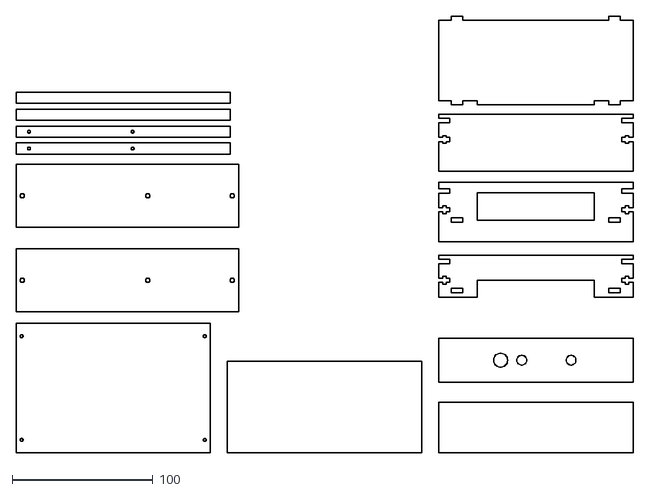
[picture p166: CAD file, 2017-04-11]
boards/DIMI-8/DIMI_chistli.dxf
438.0 x 310.0
