8BitMixtape/8Bit-Mixtape-NEO/boards/8Bit-NEO-Casing-Manticore-Build/3D_mixTape_ModelParts.stl

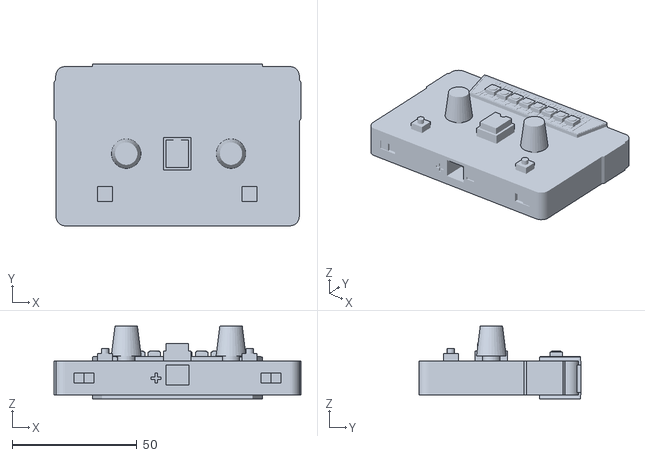
[picture p167: CAD file, 2017-06-18]
boards/8Bit-NEO-Casing-Manticore-Build/3D_mixTape_ModelParts.stl
99.0 x 64.8 x 29.2
