8BitMixtape/8Bit-Mixtape-NEO/boards/DIMI-8/garlampli.dxf

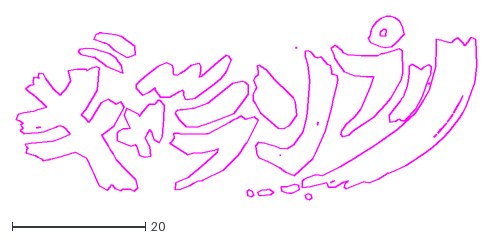
[picture p168: CAD file, 2017-04-11]
boards/DIMI-8/garlampli.dxf
69.1 x 27.6
