8BitMixtape/8Bit-Mixtape-NEO/boards/3d-files/3D_MixTape_Frame_VerDez18_03.stl

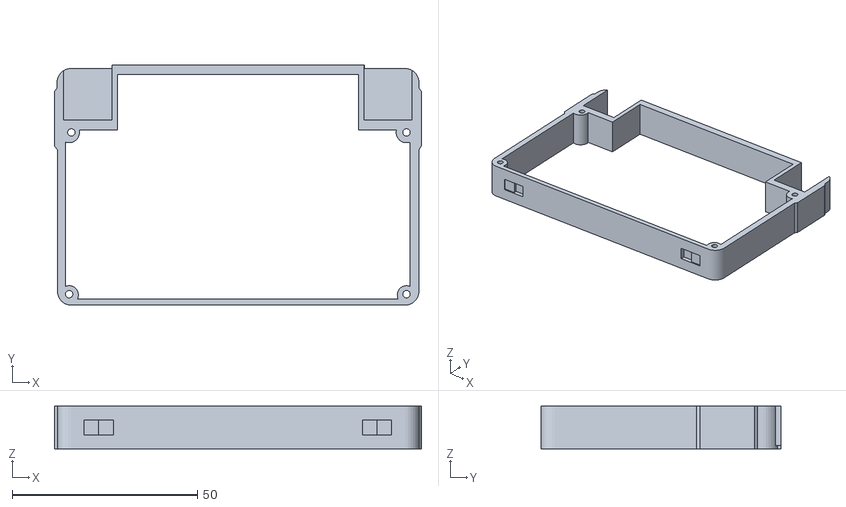
[picture p169: CAD file, 2018-12-10]
boards/3d-files/3D_MixTape_Frame_VerDez18_03.stl
99.0 x 64.8 x 11.5
