8BitMixtape/8Bit-Mixtape-NEO/boards/8Bit-NEO-Casing-Manticore-Build/mixtape_case_3D_MidRect.dxf

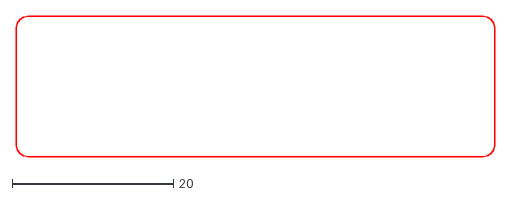
[picture p170: CAD file, 2017-06-15]
boards/8Bit-NEO-Casing-Manticore-Build/mixtape_case_3D_MidRect.dxf
59.3 x 17.4
