8BitMixtape/8Bit-Mixtape-NEO/boards/8Bit-NEO-Casing-Manticore-Build/mixtape_case_3D_bottom.dxf

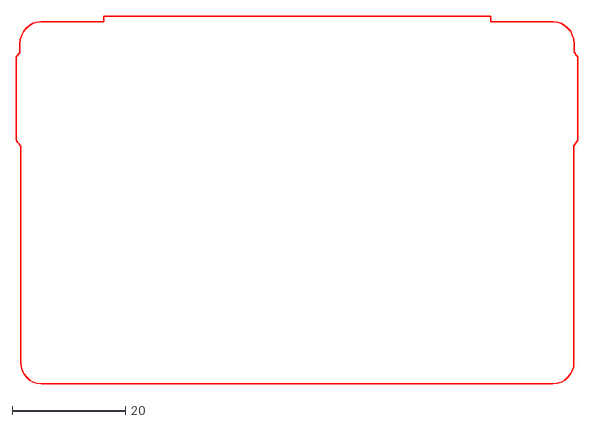
[picture p171: CAD file, 2017-06-15]
boards/8Bit-NEO-Casing-Manticore-Build/mixtape_case_3D_bottom.dxf
99.0 x 64.8
