8BitMixtape/8Bit-Mixtape-NEO/boards/8Bit-NEO-Casing-Manticore-Build/mixtape_case_3D_NutWheels.dxf

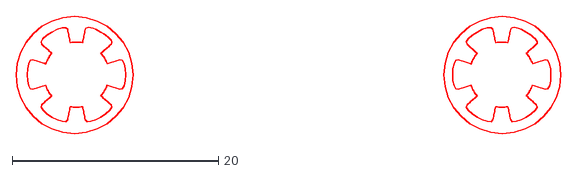
[picture p172: CAD file, 2017-06-15]
boards/8Bit-NEO-Casing-Manticore-Build/mixtape_case_3D_NutWheels.dxf
52.9 x 11.4
