8BitMixtape/8Bit-Mixtape-NEO/boards/8Bit-NEO-Casing-Manticore-Build/mixtape_case_3D_Holes.dxf

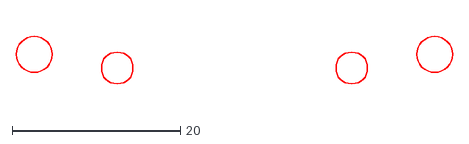
[picture p173: CAD file, 2017-06-15]
boards/8Bit-NEO-Casing-Manticore-Build/mixtape_case_3D_Holes.dxf
51.8 x 5.60
