8BitMixtape/8Bit-Mixtape-NEO/boards/8Bit-NEO-Casing-Manticore-Build/3D_mixTape_Frame_v03_95.stl

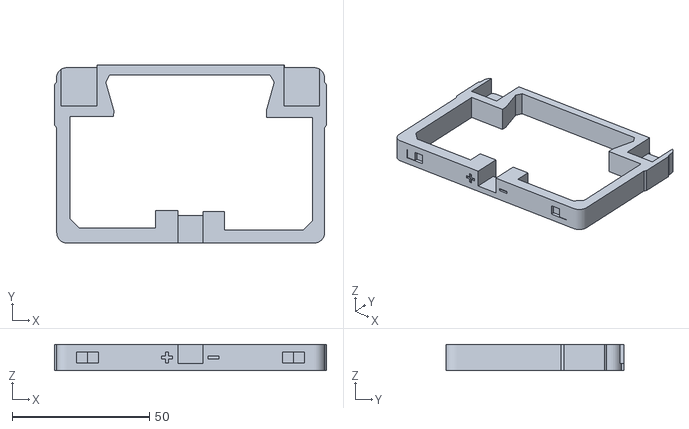
[picture p174: CAD file, 2017-06-15]
boards/8Bit-NEO-Casing-Manticore-Build/3D_mixTape_Frame_v03_95.stl
99.0 x 64.8 x 9.50
