8BitMixtape/8Bit-Mixtape-NEO/boards/8Bit-NEO-Casing-Manticore-Build/mixtape_case_3D_BigRect.dxf

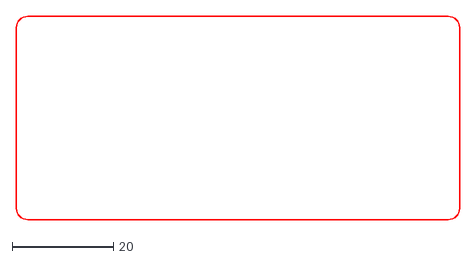
[picture p175: CAD file, 2017-06-15]
boards/8Bit-NEO-Casing-Manticore-Build/mixtape_case_3D_BigRect.dxf
87.5 x 40.2
