8BitMixtape/8Bit-Mixtape-NEO/boards/8Bit-NEO-Casing-Manticore-Build/mixtape_case_3D_PCB_TrapezBoard.dxf

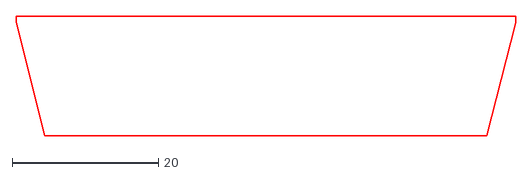
[picture p176: CAD file, 2017-06-15]
boards/8Bit-NEO-Casing-Manticore-Build/mixtape_case_3D_PCB_TrapezBoard.dxf
68.2 x 16.4
