8BitMixtape/8Bit-Mixtape-NEO/boards/8Bit-NEO-Casing-Manticore-Build/mixtape_case_3D_PCB_TrapezCircuit.dxf

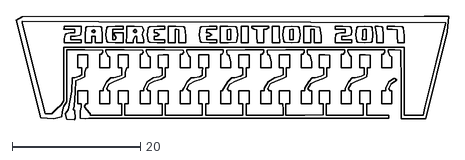
[picture p178: CAD file, 2017-06-15]
boards/8Bit-NEO-Casing-Manticore-Build/mixtape_case_3D_PCB_TrapezCircuit.dxf
67.4 x 16.2
