8BitMixtape/8Bit-Mixtape-NEO/boards/8Bit-Mixtape-NEO_v1/ShenzhenReady/Designs_for_Manufacturing_black.png

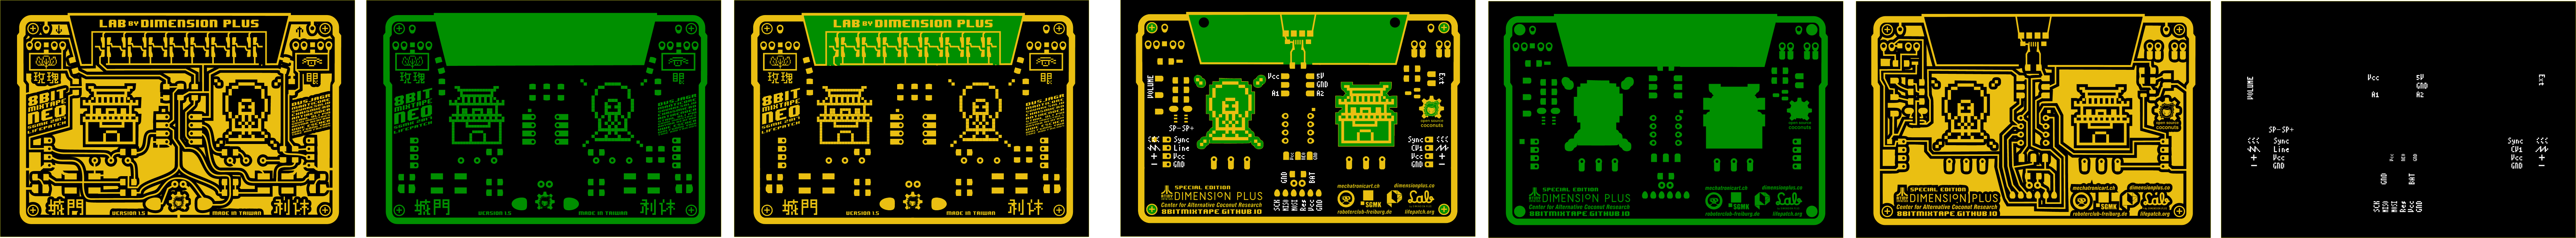
boards/8Bit-Mixtape-NEO_v1/ShenzhenReady/Designs_for_Manufacturing_black.png
