8BitMixtape/8Bit-Mixtape-NEO/boards/8Bit-Mixtape-NEO_v1/ShenzhenReady/SolderMask_geeking2.jpg

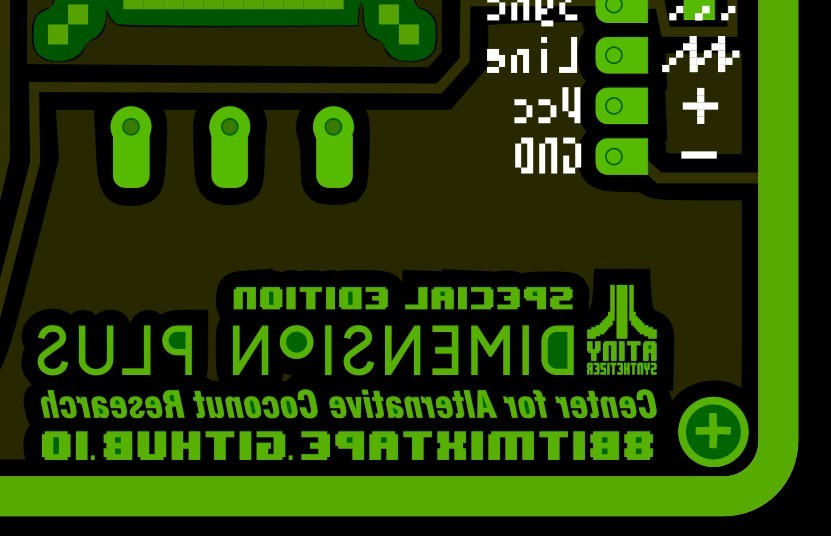
boards/8Bit-Mixtape-NEO_v1/ShenzhenReady/SolderMask_geeking2.jpg
