8BitMixtape/8Bit-Mixtape-NEO/boards/8Bit-Mixtape-NEO_v1/ShenzhenReady/SolderMask_geeking.jpg

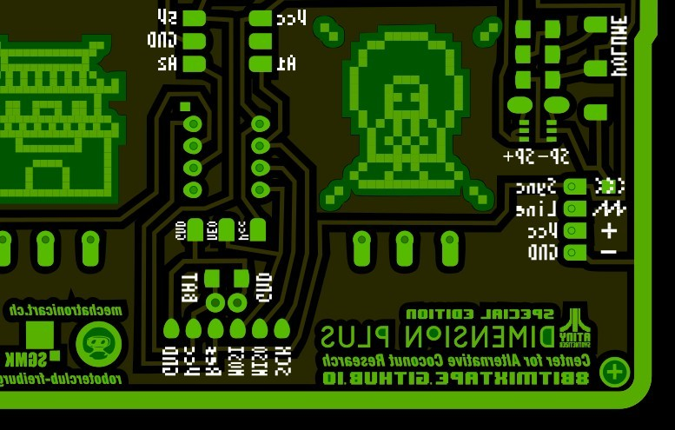
boards/8Bit-Mixtape-NEO_v1/ShenzhenReady/SolderMask_geeking.jpg
