8BitMixtape/8Bit-Mixtape-NEO/boards/DIMI-8/MakingOf/IMG_20170317_015808_HDR.jpg

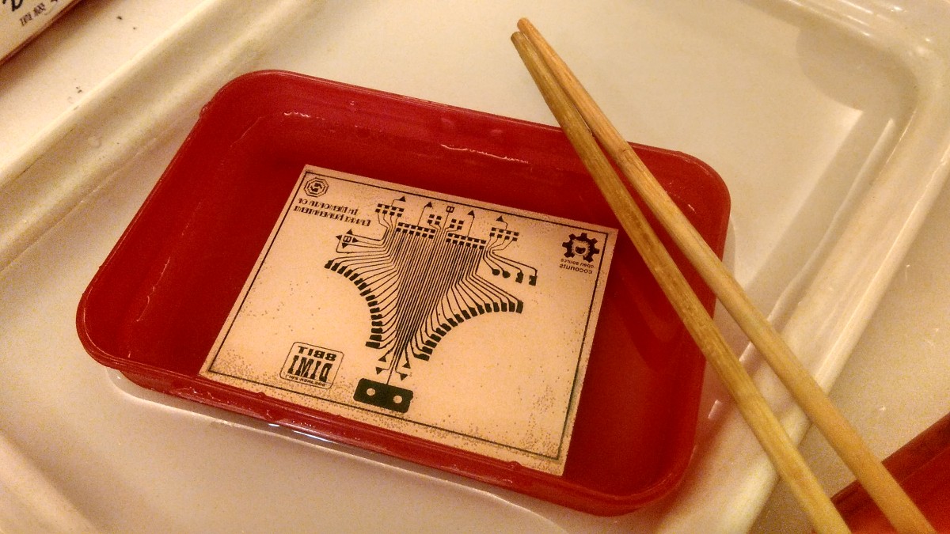
boards/DIMI-8/MakingOf/IMG_20170317_015808_HDR.jpg
