8BitMixtape/8Bit-Mixtape-NEO/boards/DIMI-8/MakingOf/IMG_20170317_022459.jpg

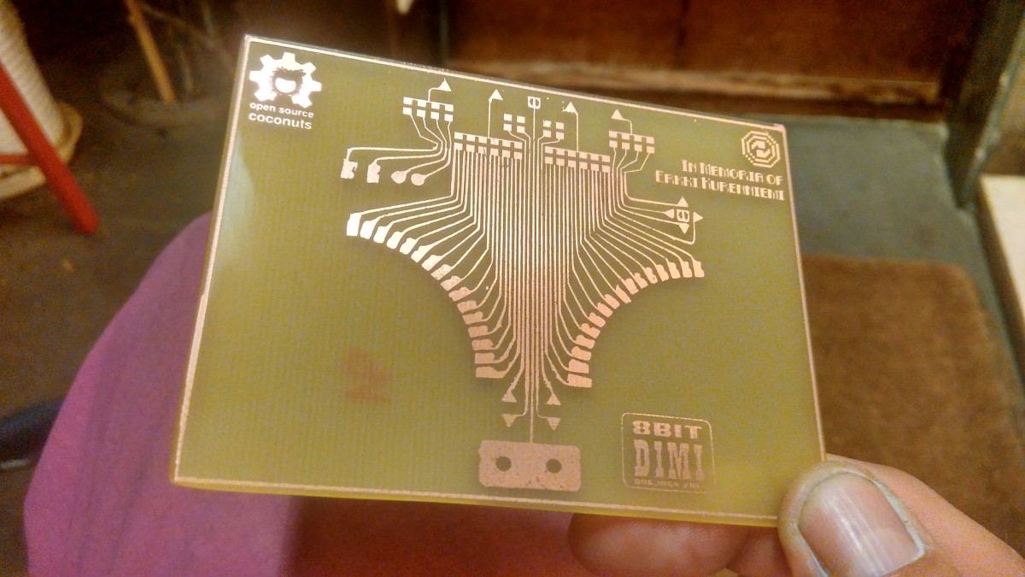
boards/DIMI-8/MakingOf/IMG_20170317_022459.jpg
