8BitMixtape/8Bit-Mixtape-NEO/boards/DIMI-8/MakingOf/IMG_20170317_045715.jpg

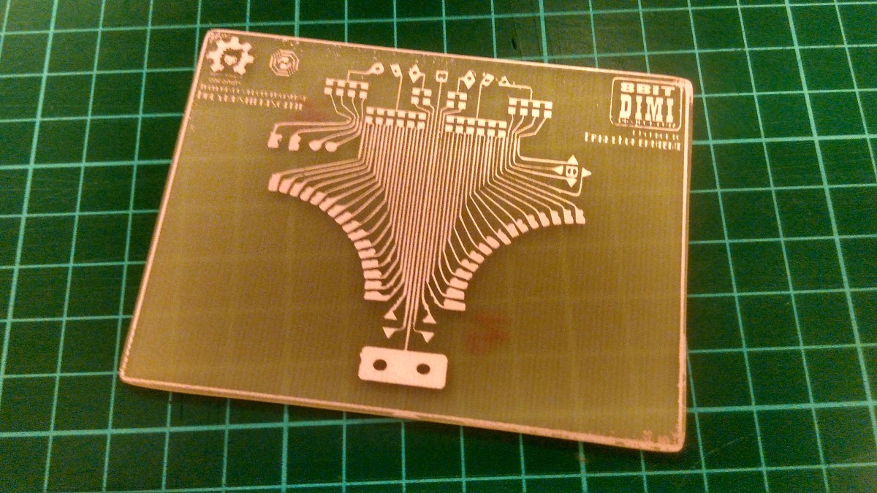
boards/DIMI-8/MakingOf/IMG_20170317_045715.jpg
