8BitMixtape/8Bit-Mixtape-NEO/boards/images_schematics/making_of_etchedBoards.png

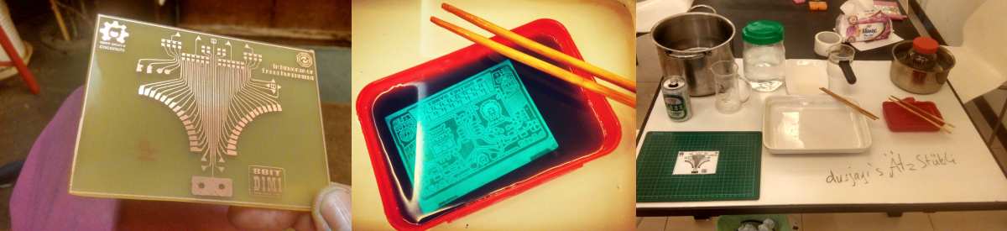
boards/images_schematics/making_of_etchedBoards.png
