8BitMixtape/8Bit-Mixtape-NEO/boards/MakeYourOwn_MASK_v01.png

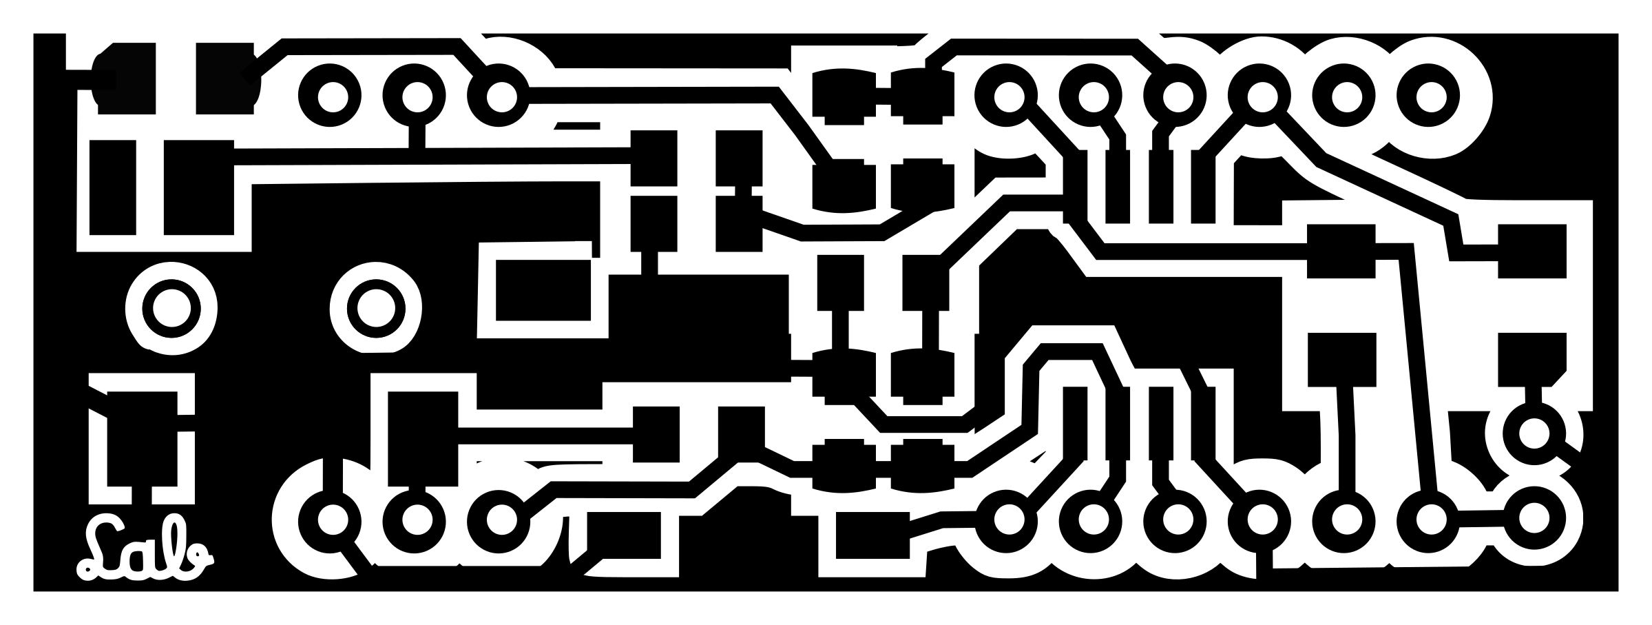
boards/MakeYourOwn_MASK_v01.png
