8BitMixtape/8Bit-Mixtape-NEO/boards/MakeYourOwn_PerfBoardEdition.jpg

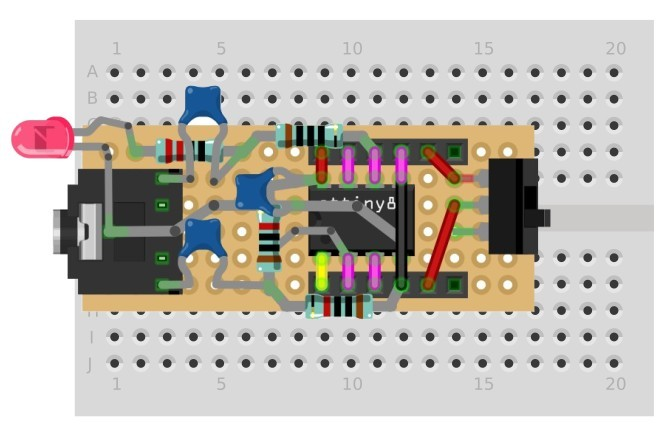
boards/MakeYourOwn_PerfBoardEdition.jpg
