8BitMixtape/8Bit-Mixtape-NEO/boards/MakeYourOwn_SMD_Edition.jpg

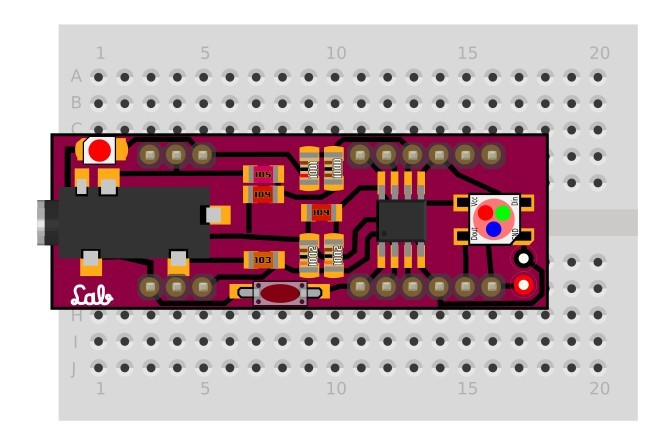
boards/MakeYourOwn_SMD_Edition.jpg
