8BitMixtape/8Bit-Mixtape-NEO/boards/8Bit-Mixtape-NEO_v1/NEO_kit-packaging_testing.jpg

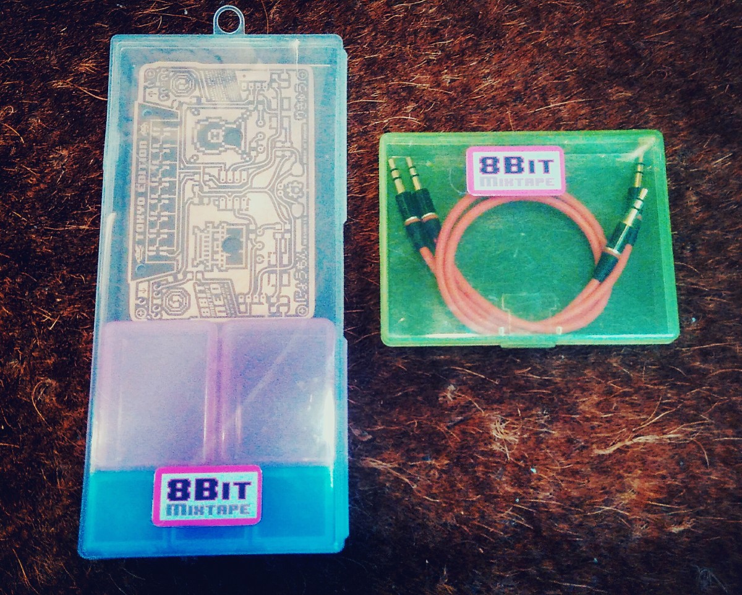
boards/8Bit-Mixtape-NEO_v1/NEO_kit-packaging_testing.jpg
