8BitMixtape/8Bit-Mixtape-NEO/boards/8Bit-Mixtape-NEO_v1/ShenzhenReady/Testing_layer_style.png

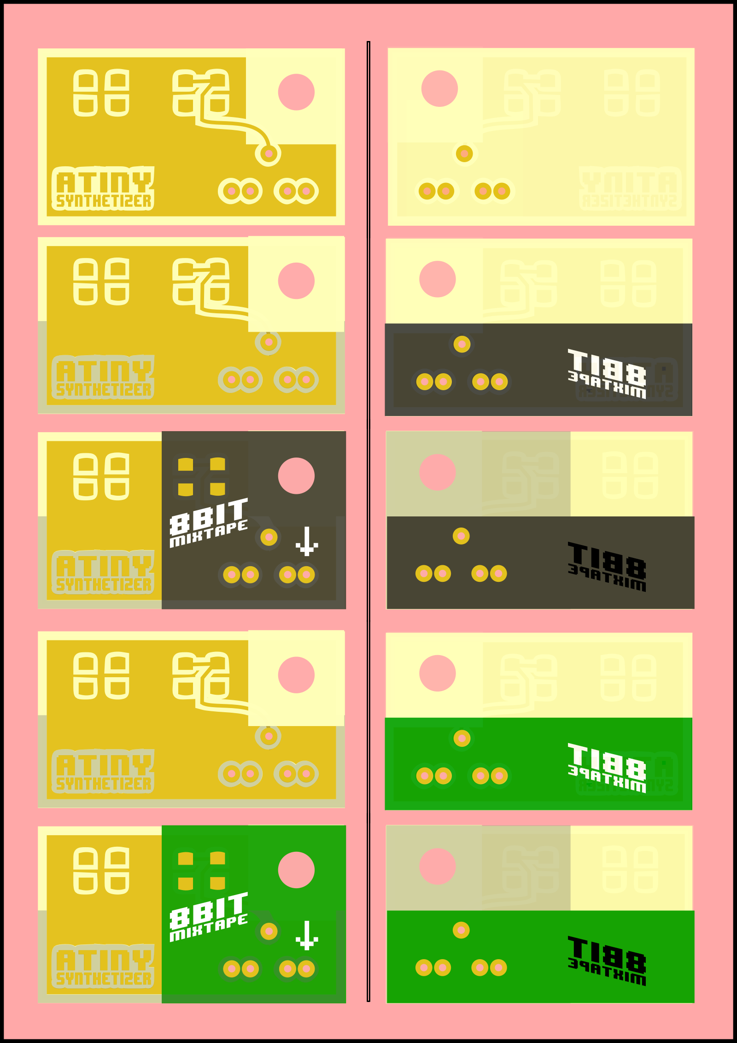
boards/8Bit-Mixtape-NEO_v1/ShenzhenReady/Testing_layer_style.png
