8BitMixtape/8Bit-Mixtape-NEO/boards/images_schematics/irg054_test_santiago.jpg

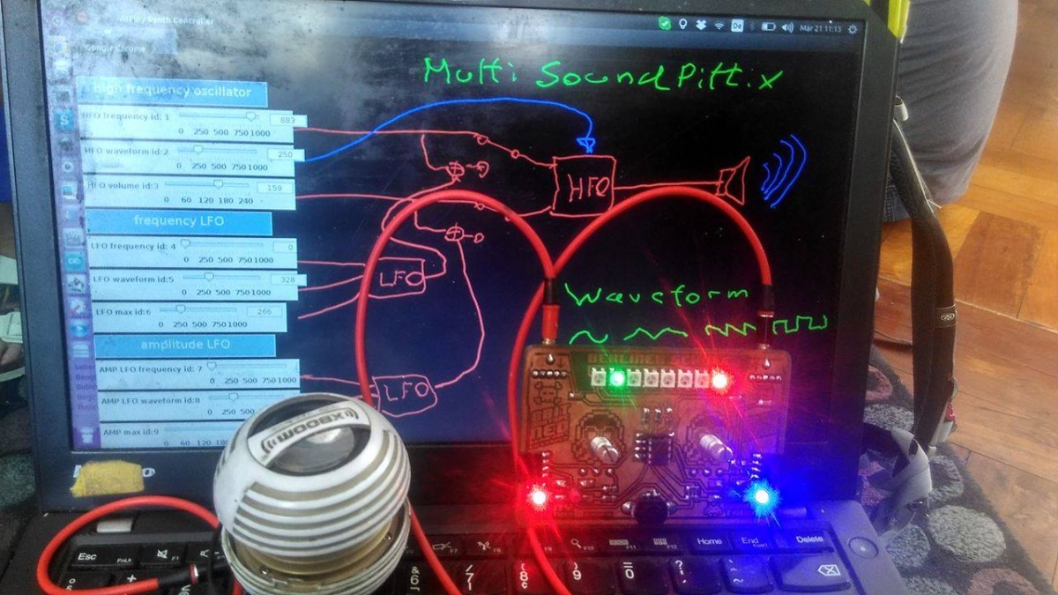
boards/images_schematics/irg054_test_santiago.jpg
