8BitMixtape/8Bit-Mixtape-NEO/boards/8Bit-Mixtape-NEO_v1/ShenzhenReady/Mixtape_Manufacture_design_possibilities.pdf

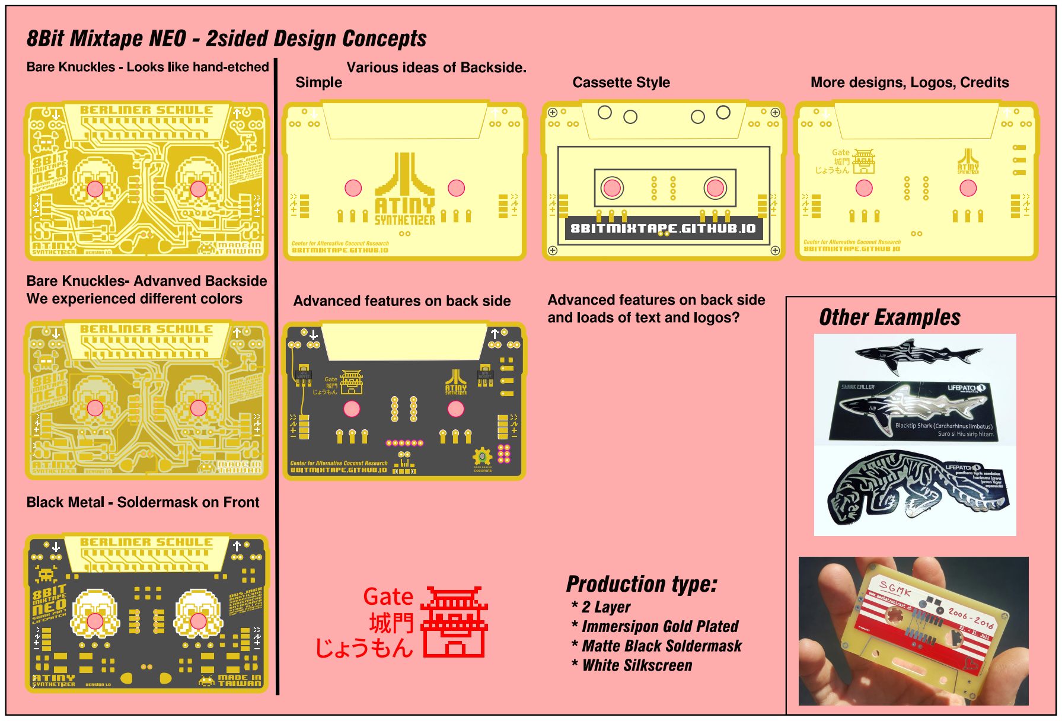
[picture p210: page 1]
