8BitMixtape/8Bit-Mixtape-NEO/boards/3d-files/case_mixtape_4056_2.pdf

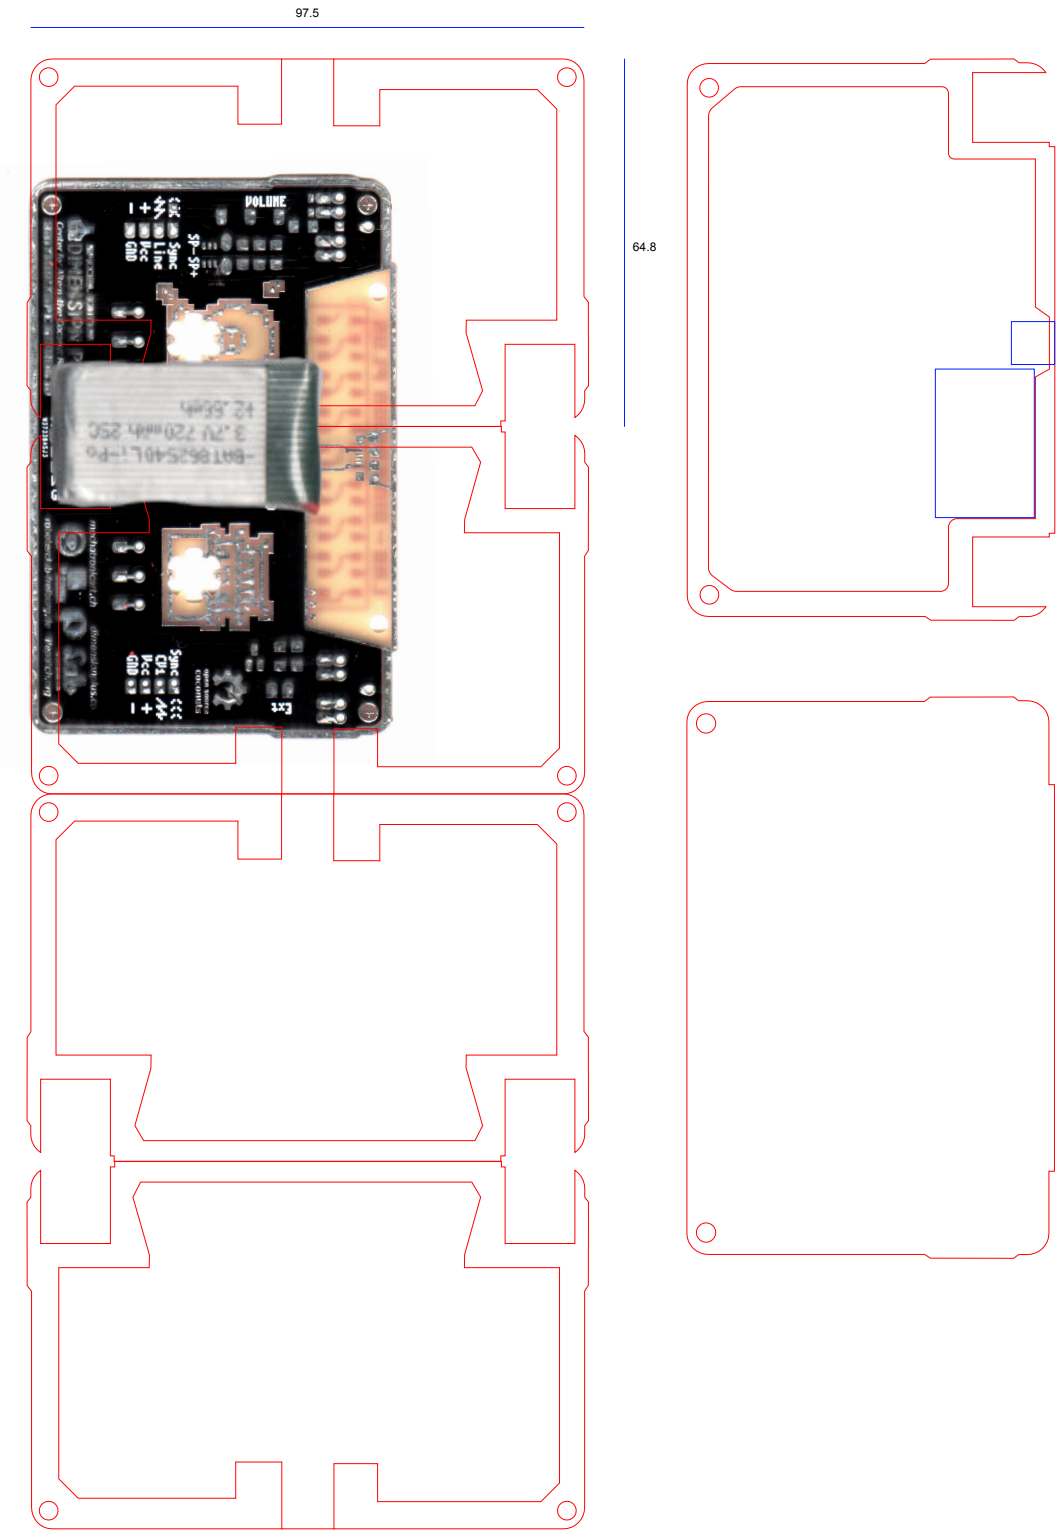
[picture p211: page 1]
