8BitMixtape/8Bit-Mixtape-NEO/boards/3d-files/case_mixtape_pdf.pdf

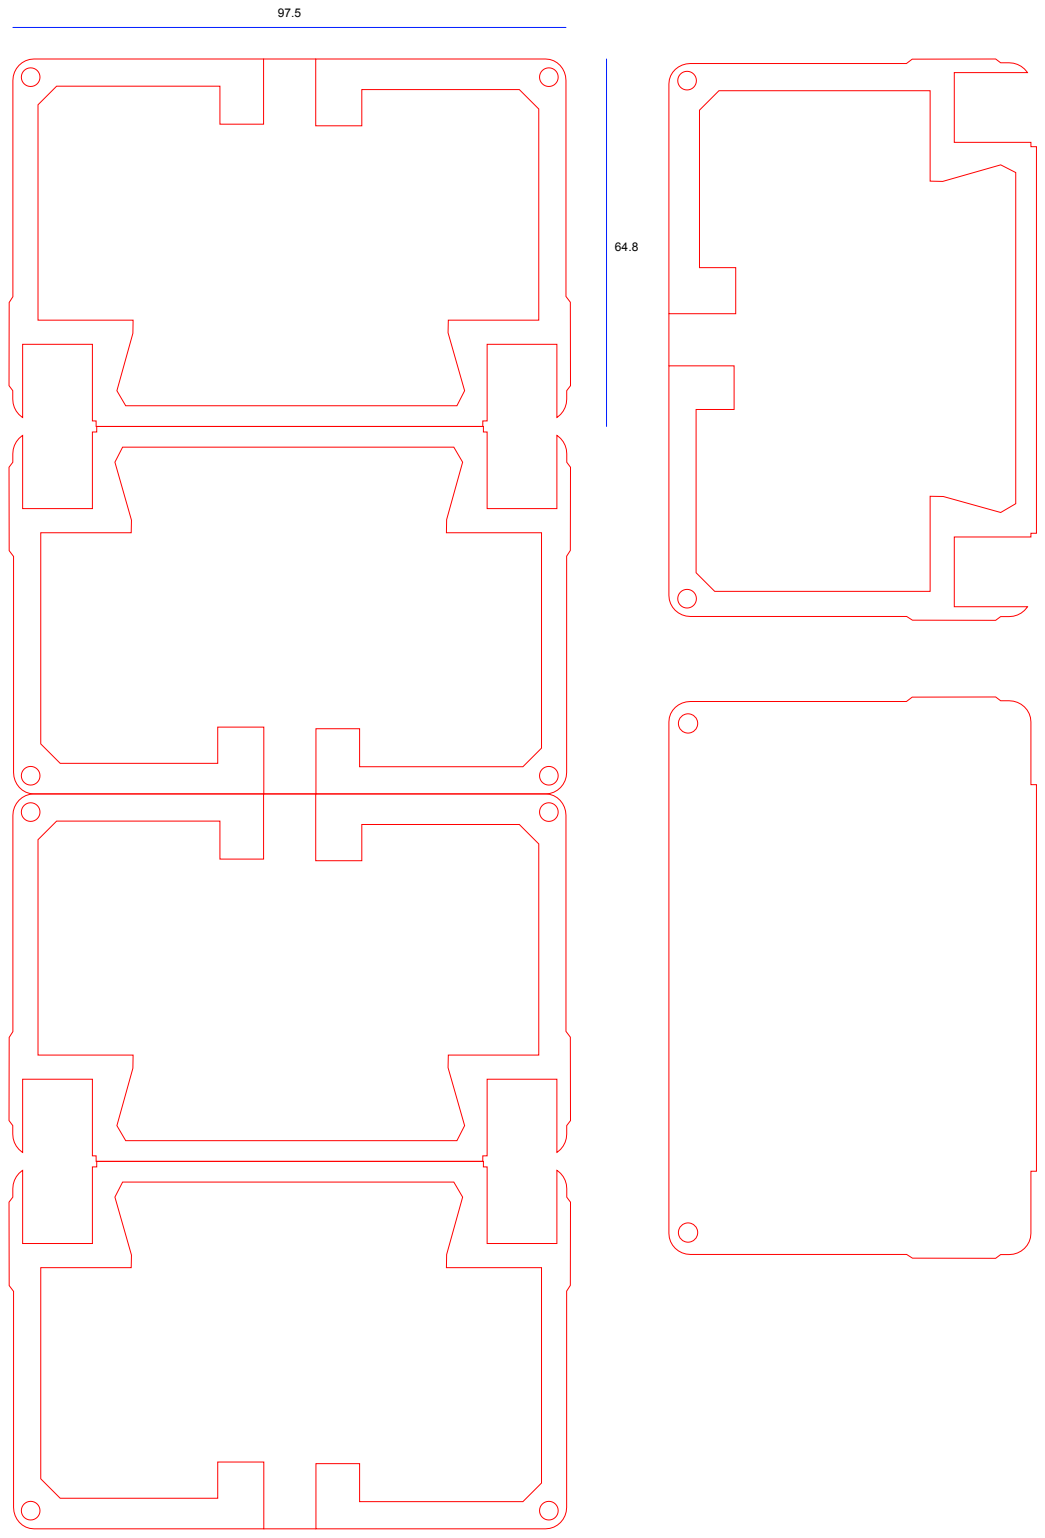
[picture p212: page 1]
