8BitMixtape/8Bit-Mixtape-NEO/boards/DIMI-8/DIMI-8_v10.pdf

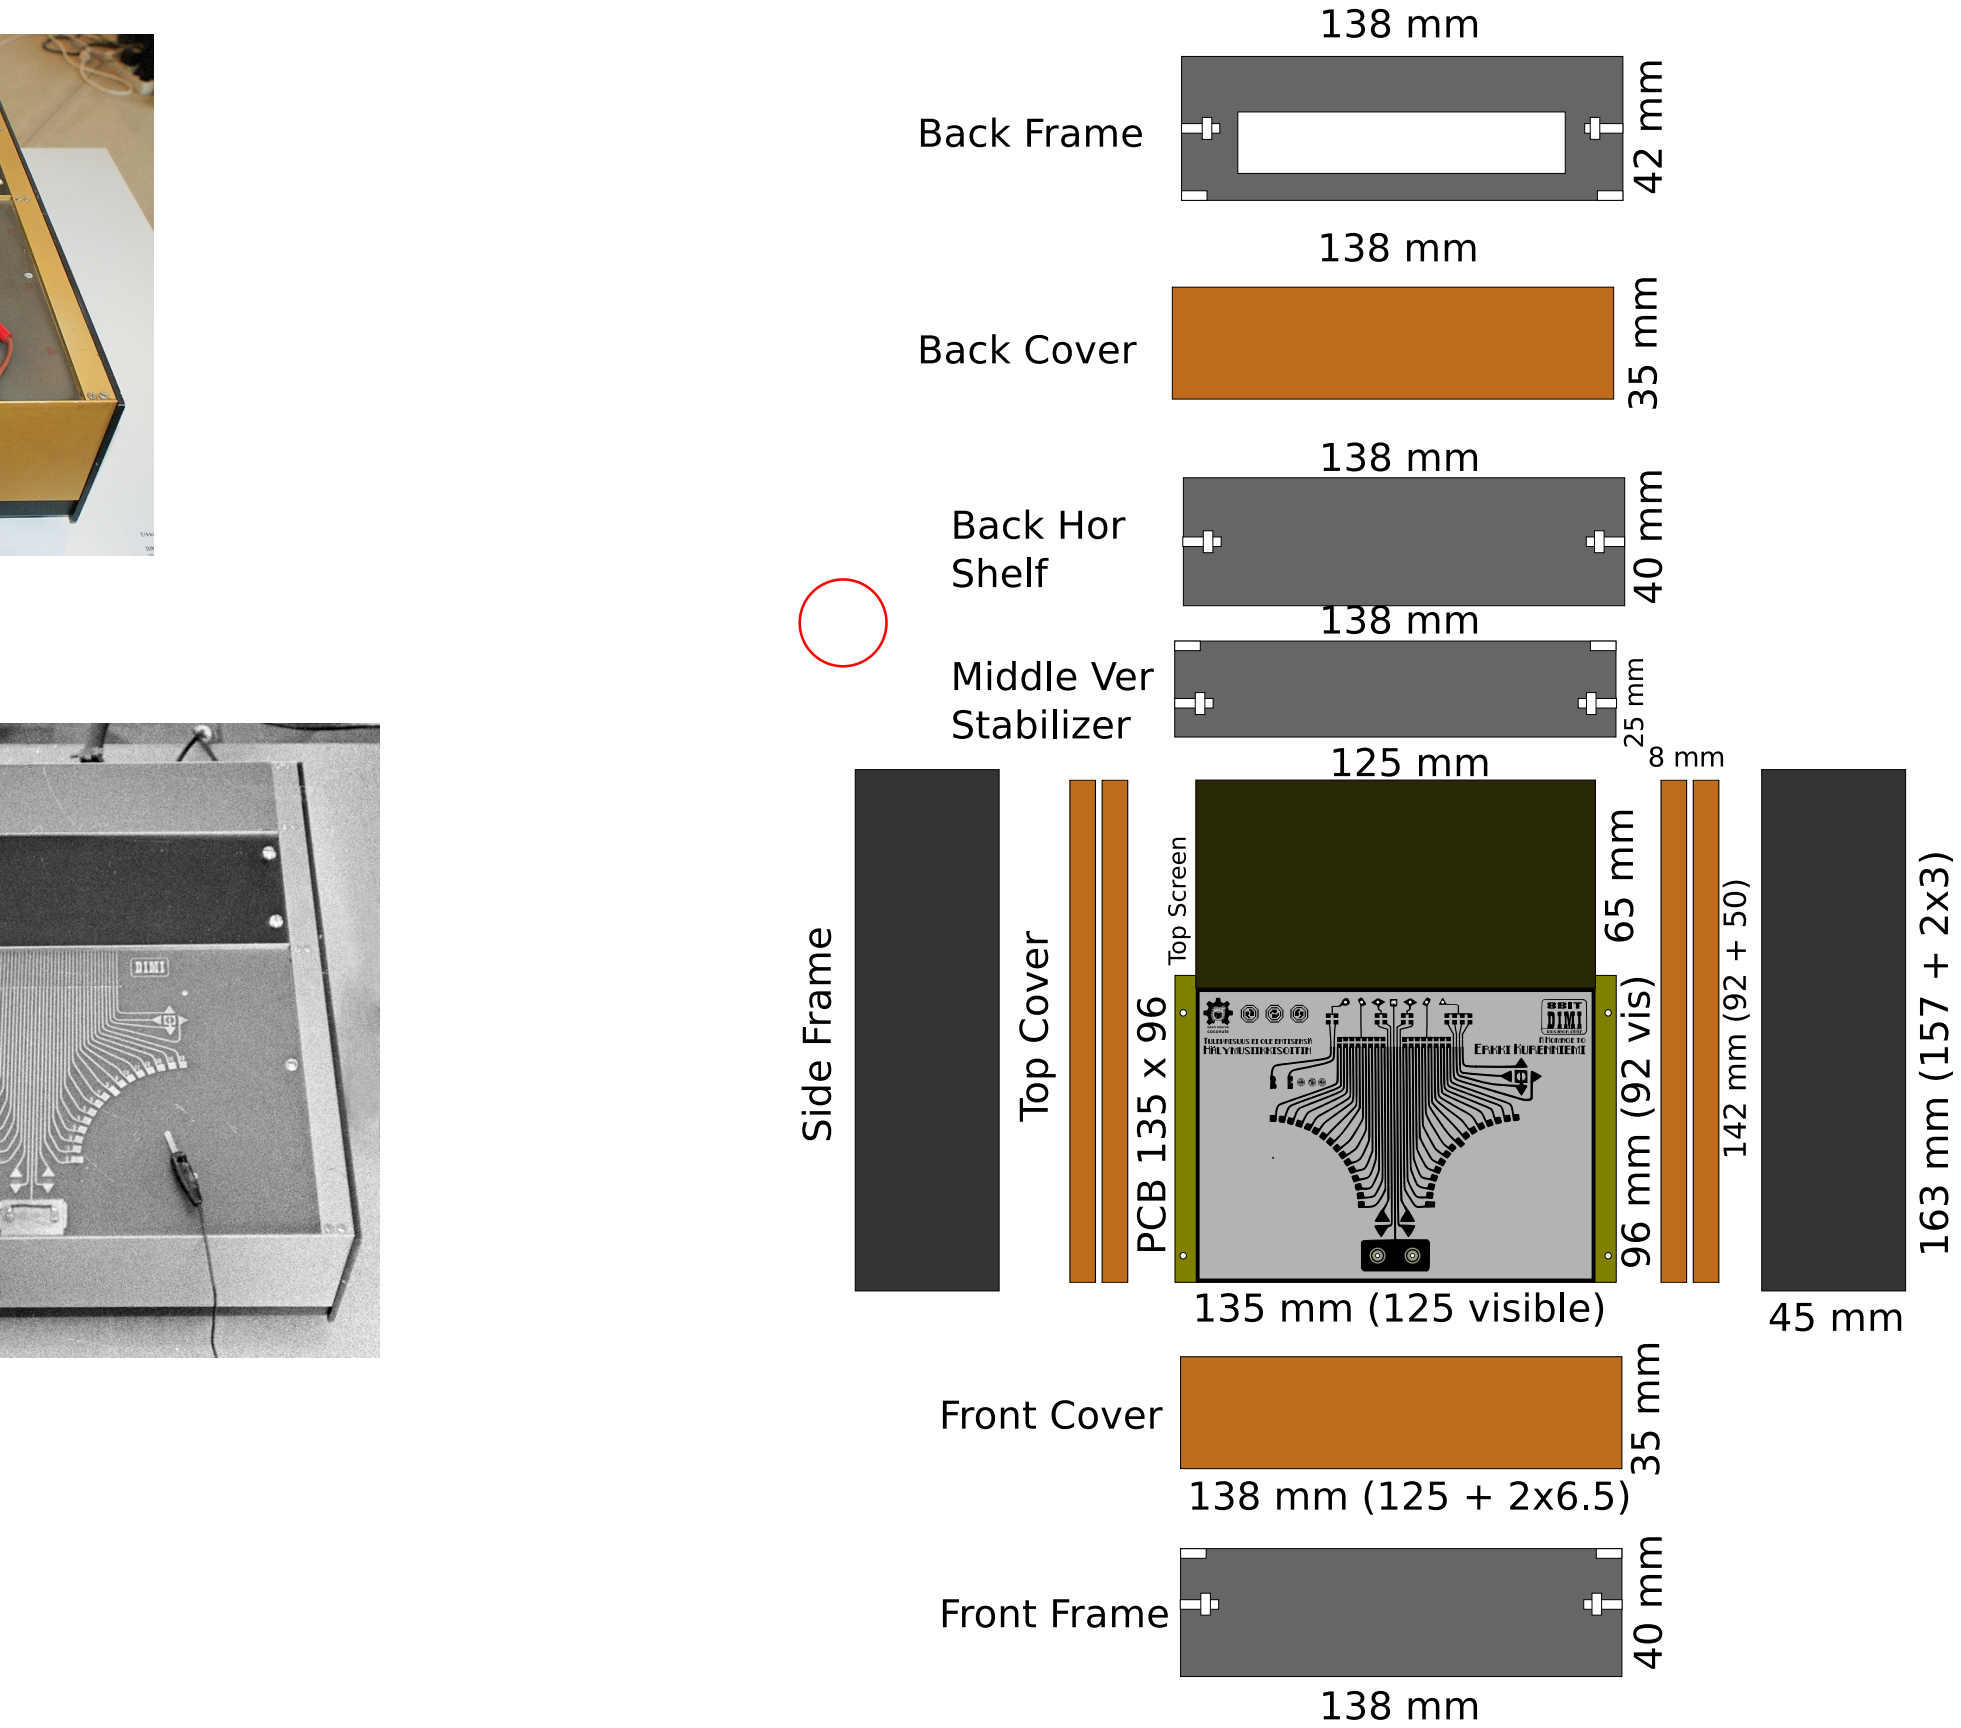
[picture p213: page 1]
