8BitMixtape/8Bit-Mixtape-NEO/boards/DIMI-8/DIMI-8_v10_anyma.pdf

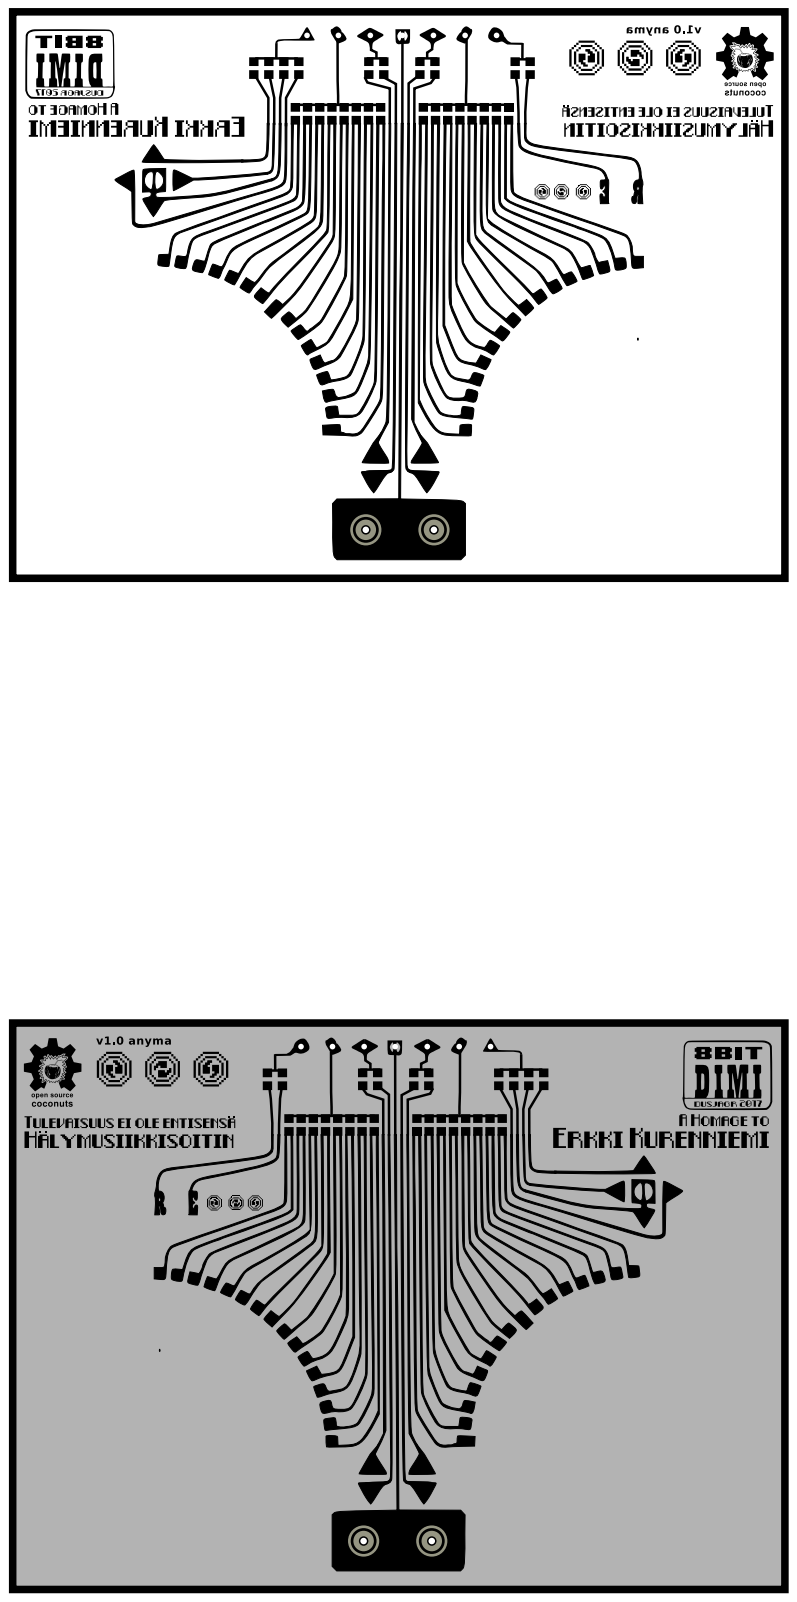
[picture p214: page 1]
