8BitMixtape/8Bit-Mixtape-NEO/boards/DIMI-8/DIMI-8_v12_anyma_MASK.pdf

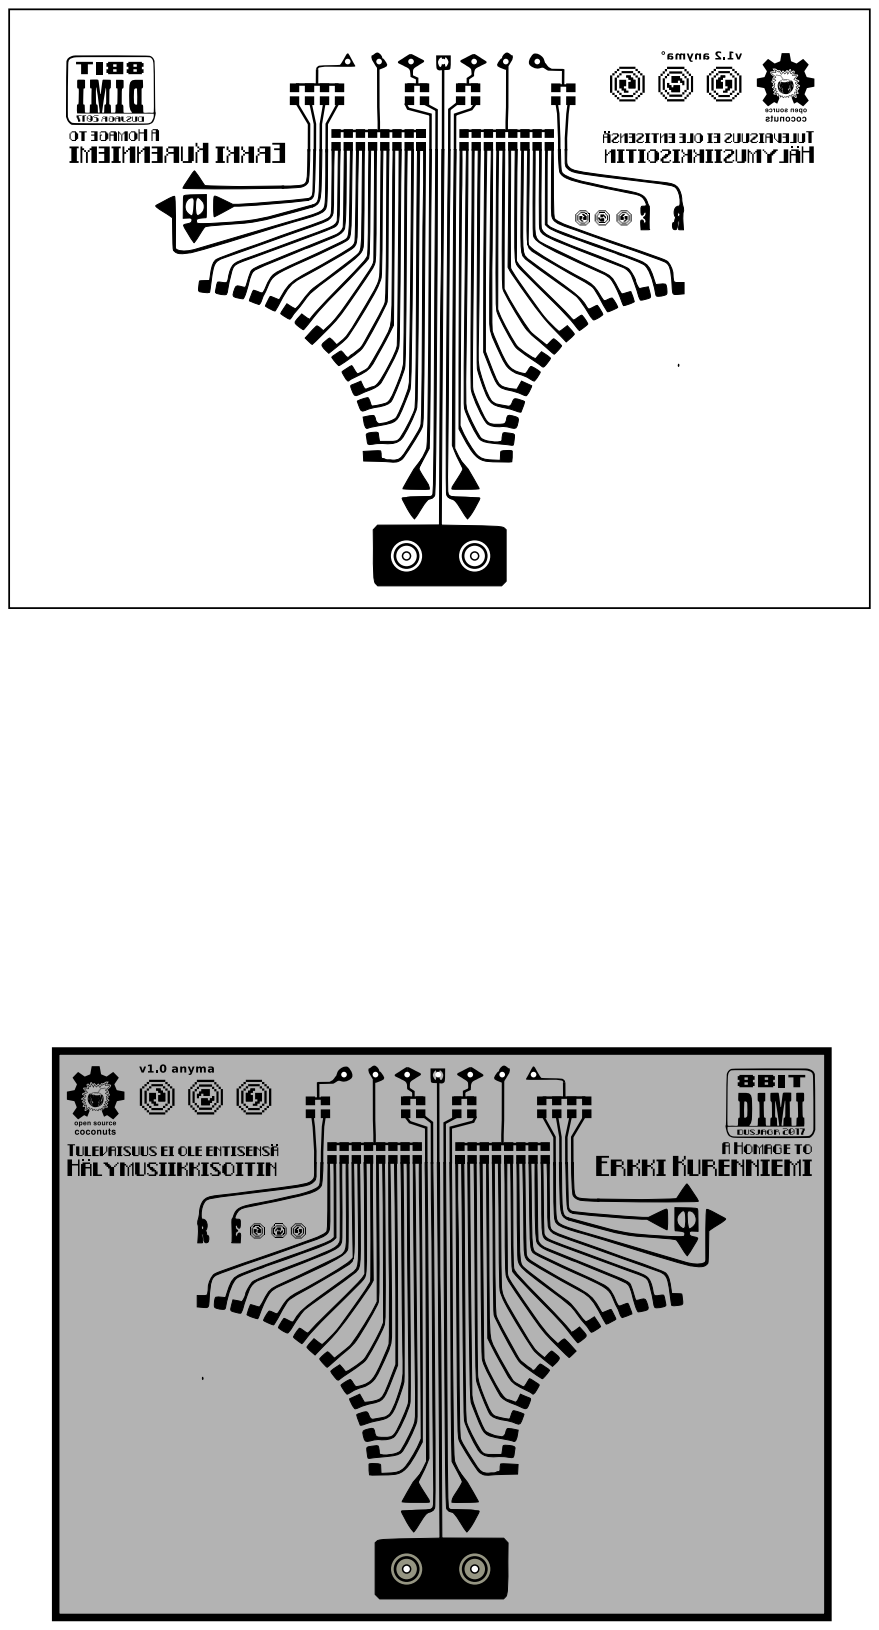
[picture p215: page 1]
