8BitMixtape/8Bit-Mixtape-NEO/boards/DIMI-8/DIMI-8_v02_MASK.pdf

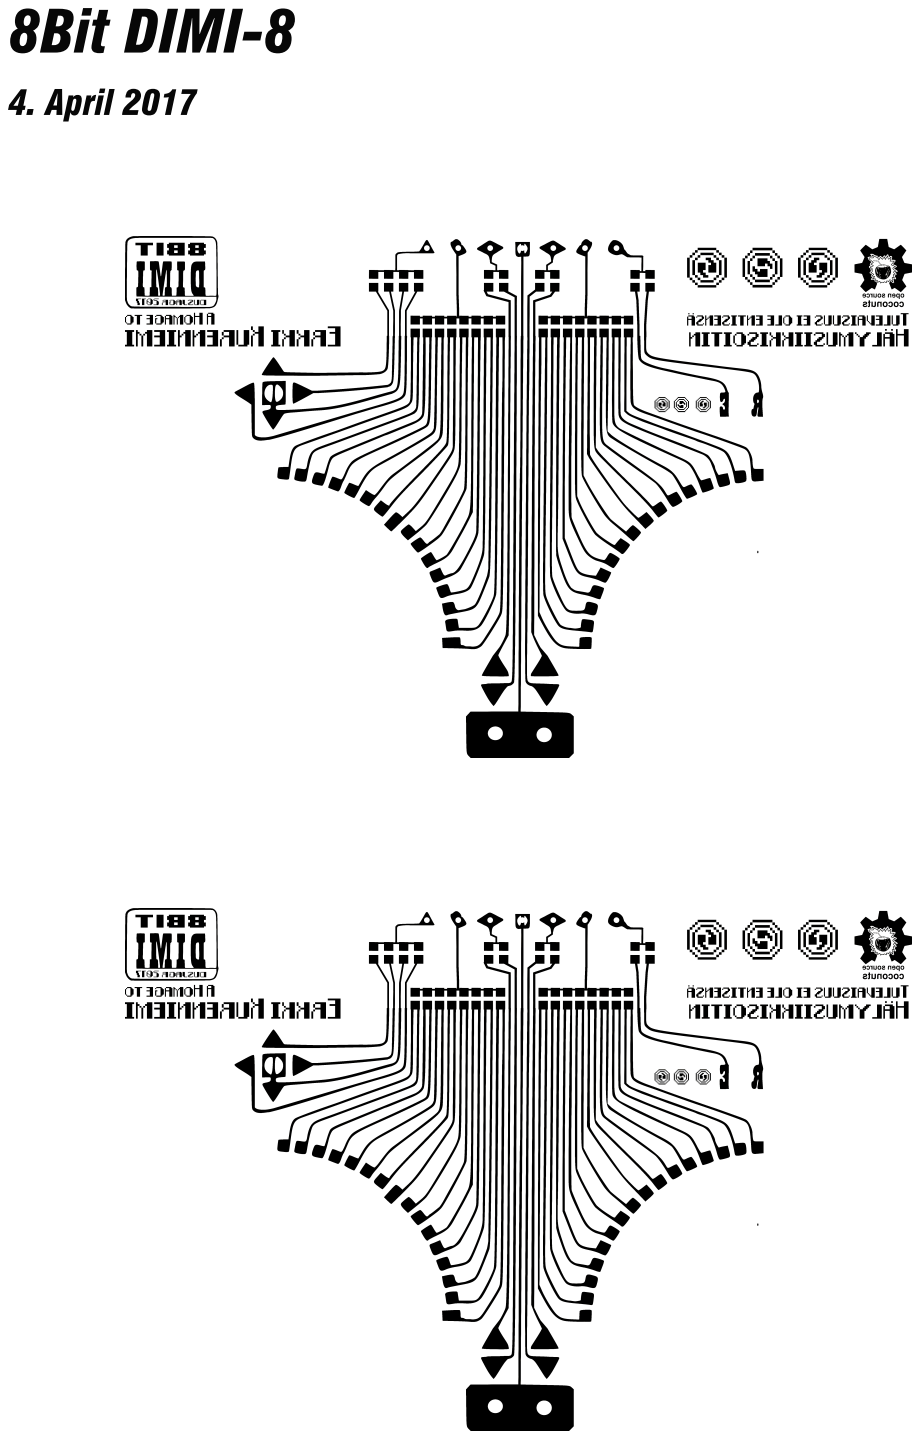
[picture p216: page 1]
