8BitMixtape/8Bit-Mixtape-NEO/boards/NEO-Coconut/GärLämpli_laminates_CU-scaling.pdf

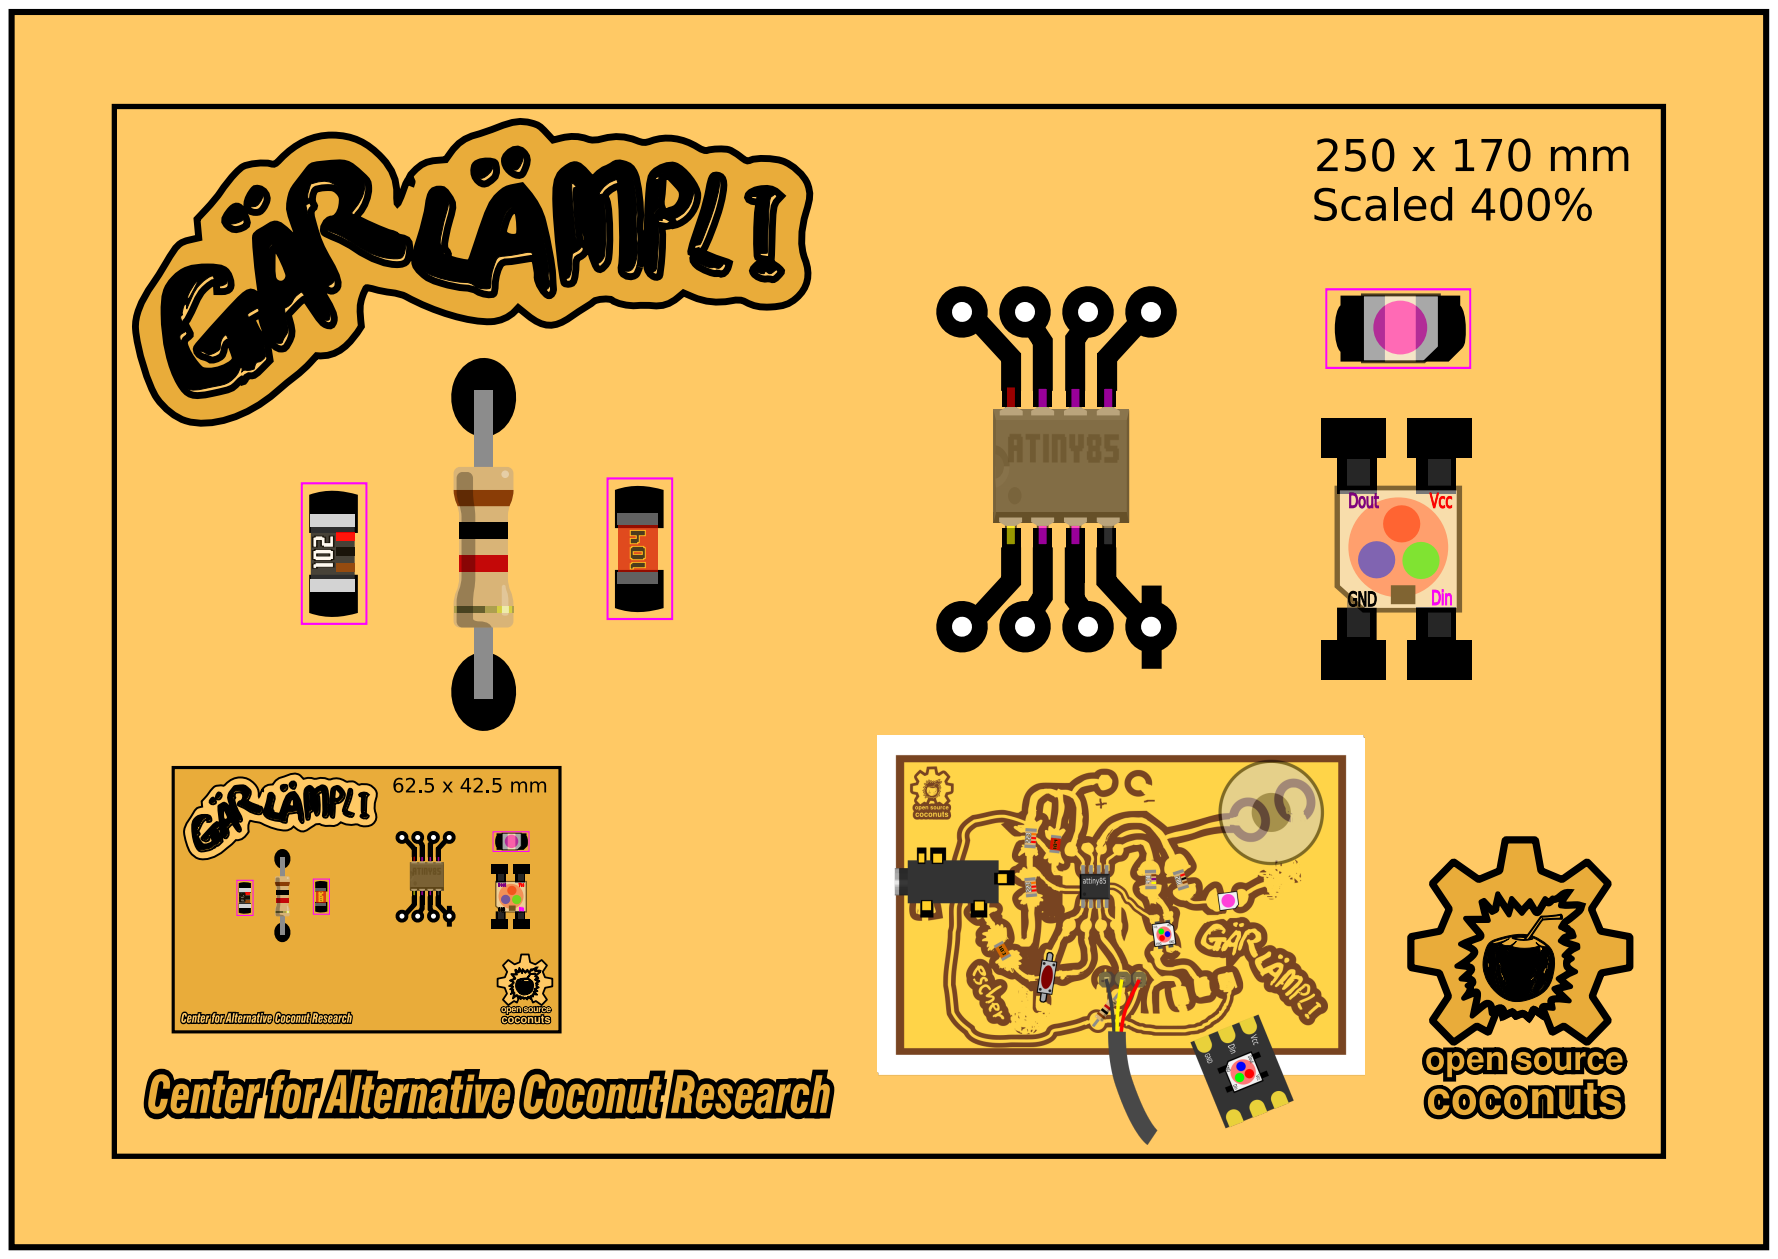
[picture p217: page 1]
