8BitMixtape/8Bit-Mixtape-NEO/boards/NEO-Coconut/GärLämpli_laminates_bigparts.pdf

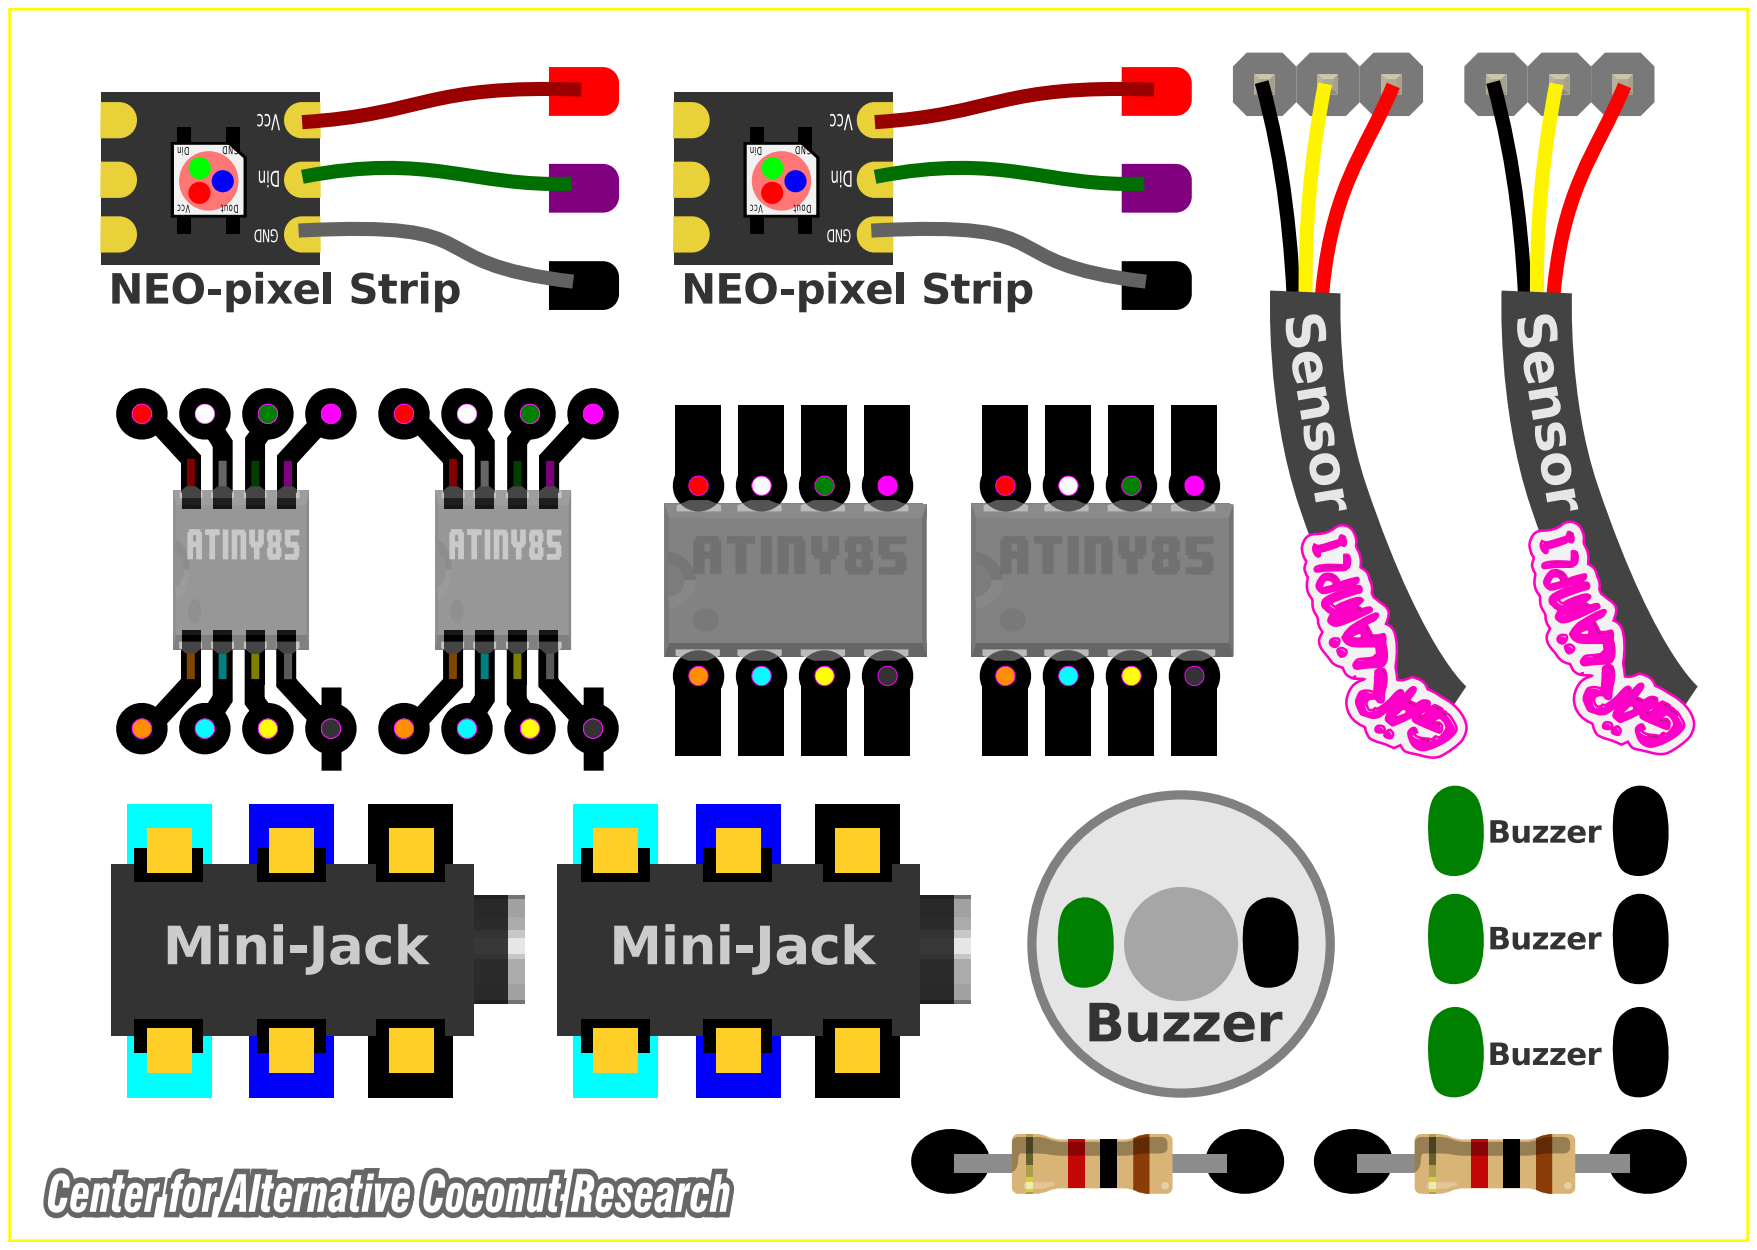
[picture p218: page 1]
