8BitMixtape/8Bit-Mixtape-NEO/boards/NEO-Coconut/GärLämpli_laminates_breadboard.pdf

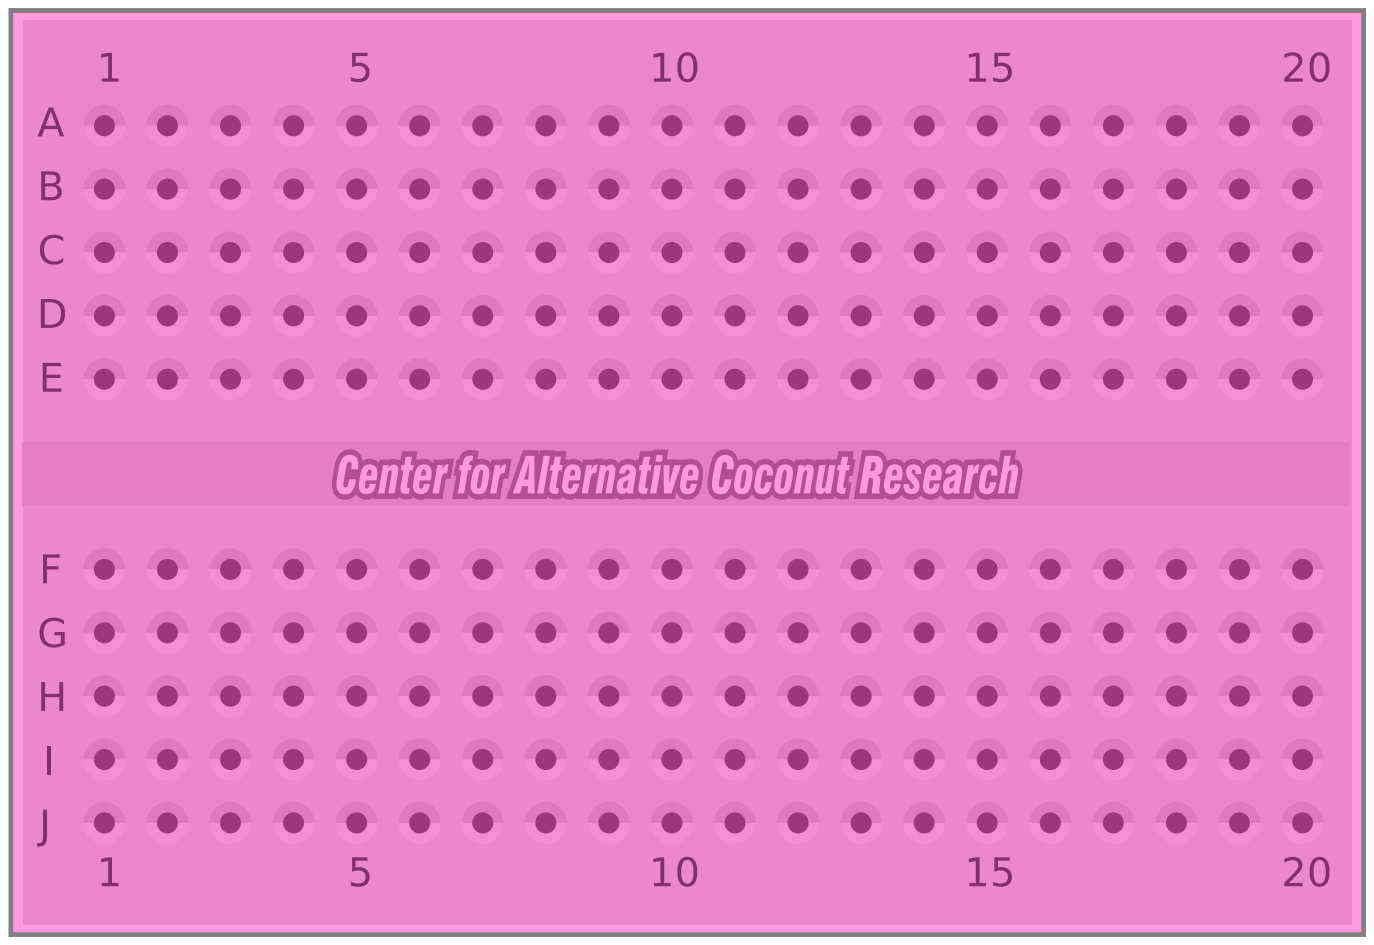
[picture p219: page 1]
