8BitMixtape/8Bit-Mixtape-NEO/boards/NEO-Coconut/GärLämpli_laminates_workspace.pdf

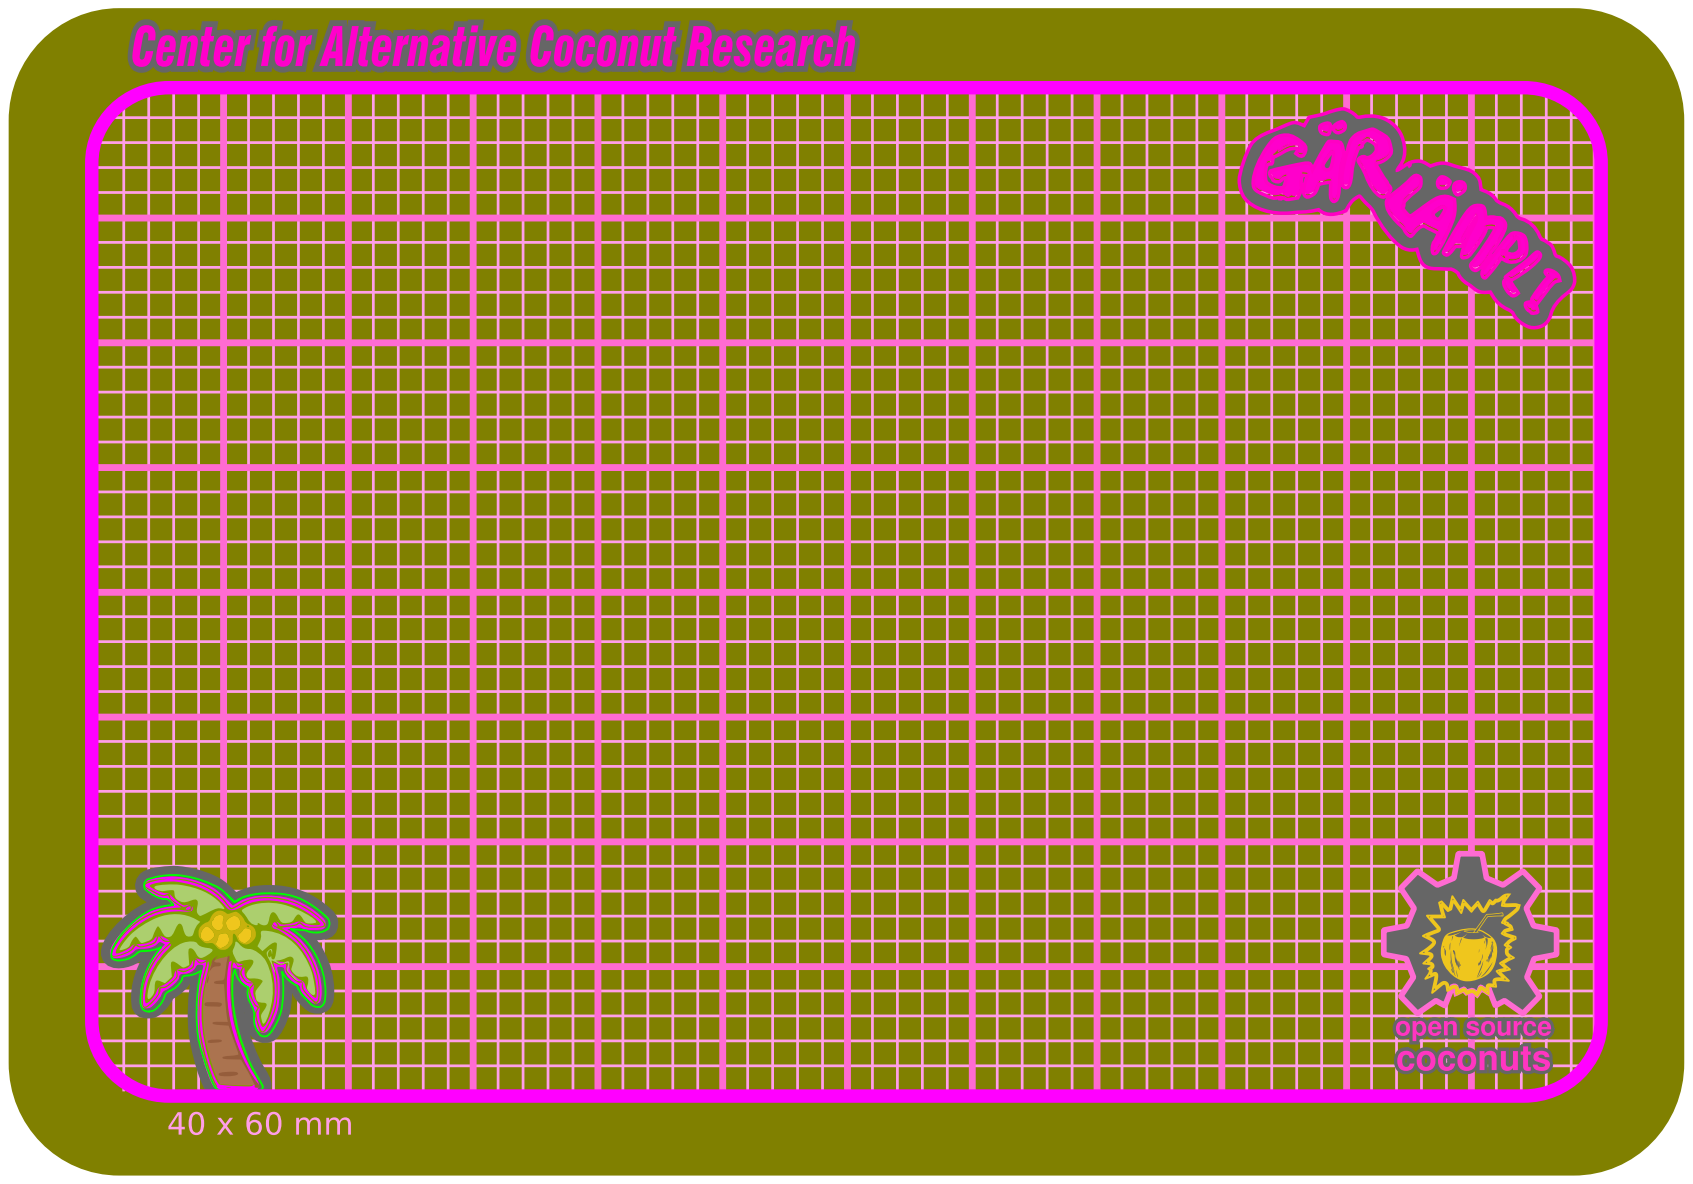
[picture p220: page 1]
