8BitMixtape/8Bit-Mixtape-NEO/boards/NEO-Coconut/GärLämpli_GridBoard.pdf

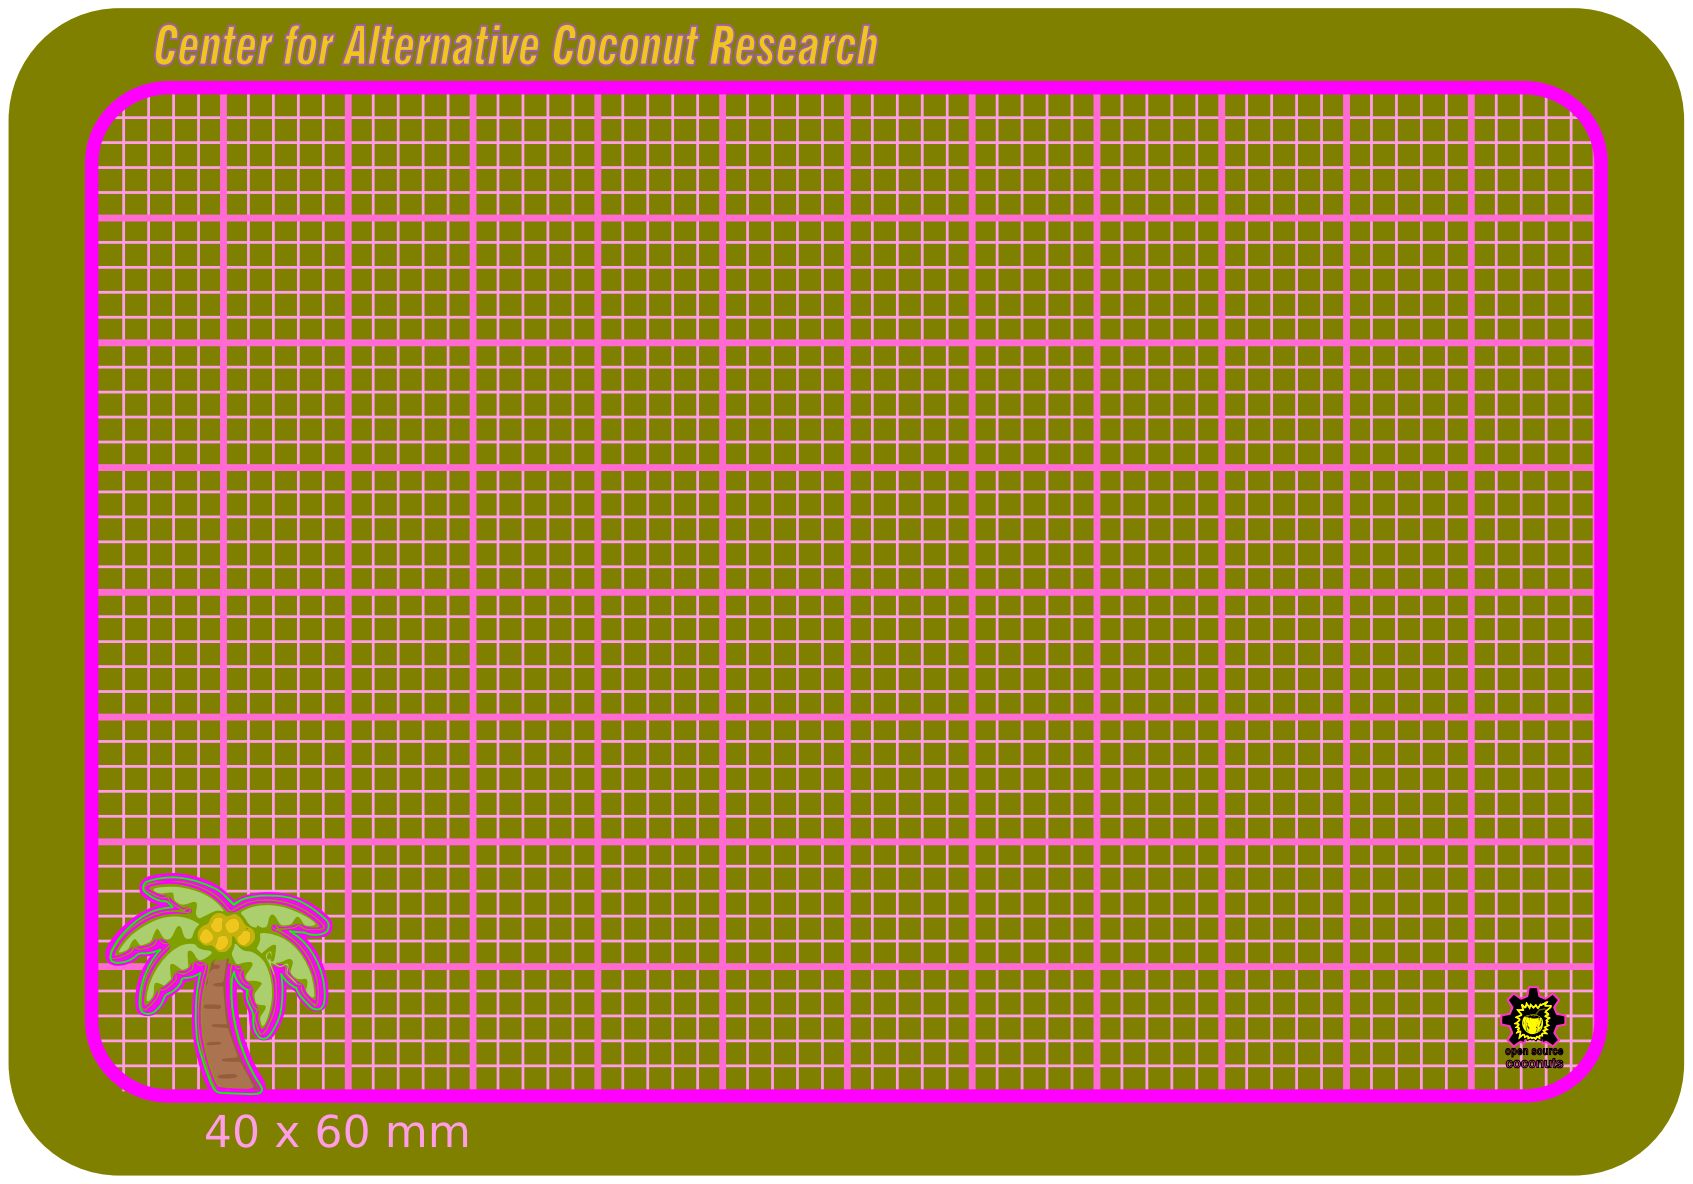
[picture p222: page 1]
