8BitMixtape/8Bit-Mixtape-NEO/boards/8Bit-Mixtape-NEO_v1/8BitMixtapeNEO_v13_dimension_edition.pdf

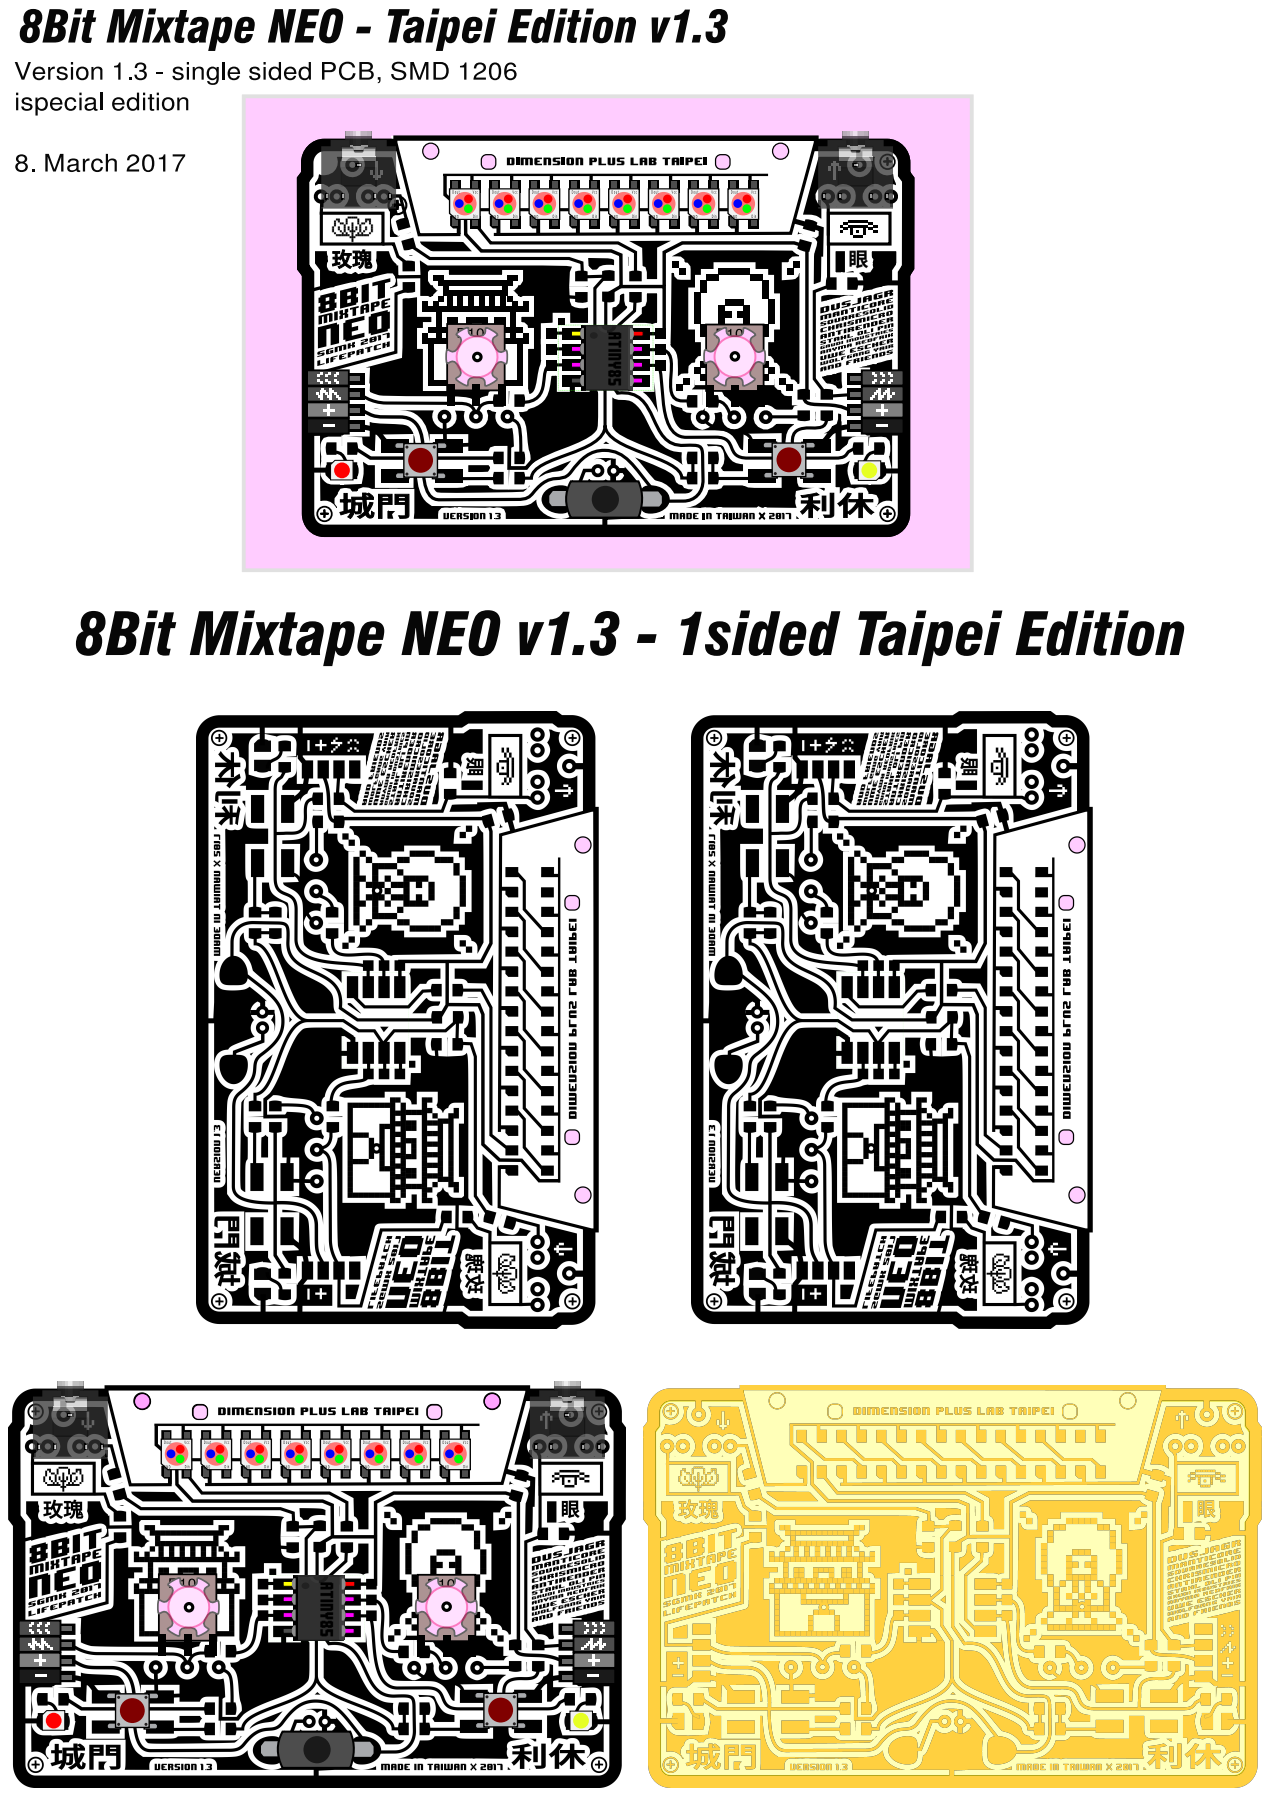
[picture p223: page 1]
