8BitMixtape/8Bit-Mixtape-NEO/boards/8Bit-Mixtape-NEO_v1/DIY_Board/8BitMixtape_DIY_Edition_25_MASK.pdf

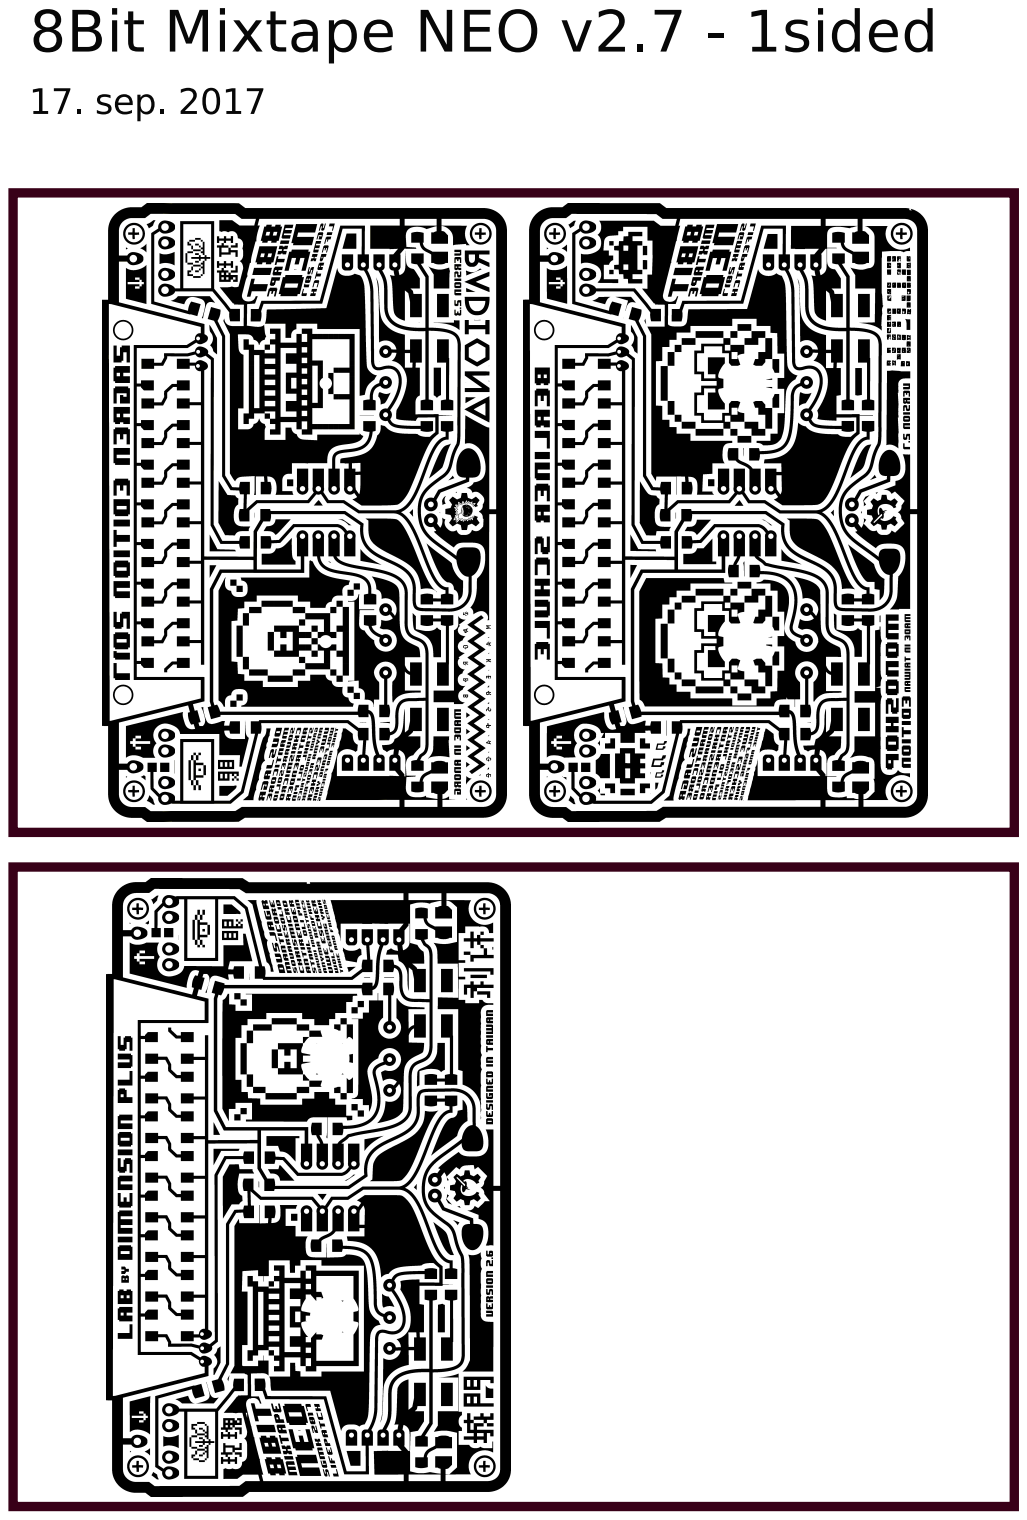
[picture p225: page 1]
