8BitMixtape/8Bit-Mixtape-NEO/boards/8Bit-Mixtape-NEO_v1/ShenzhenReady/8BitMixtapeNEO_v14_dimension_edition.pdf

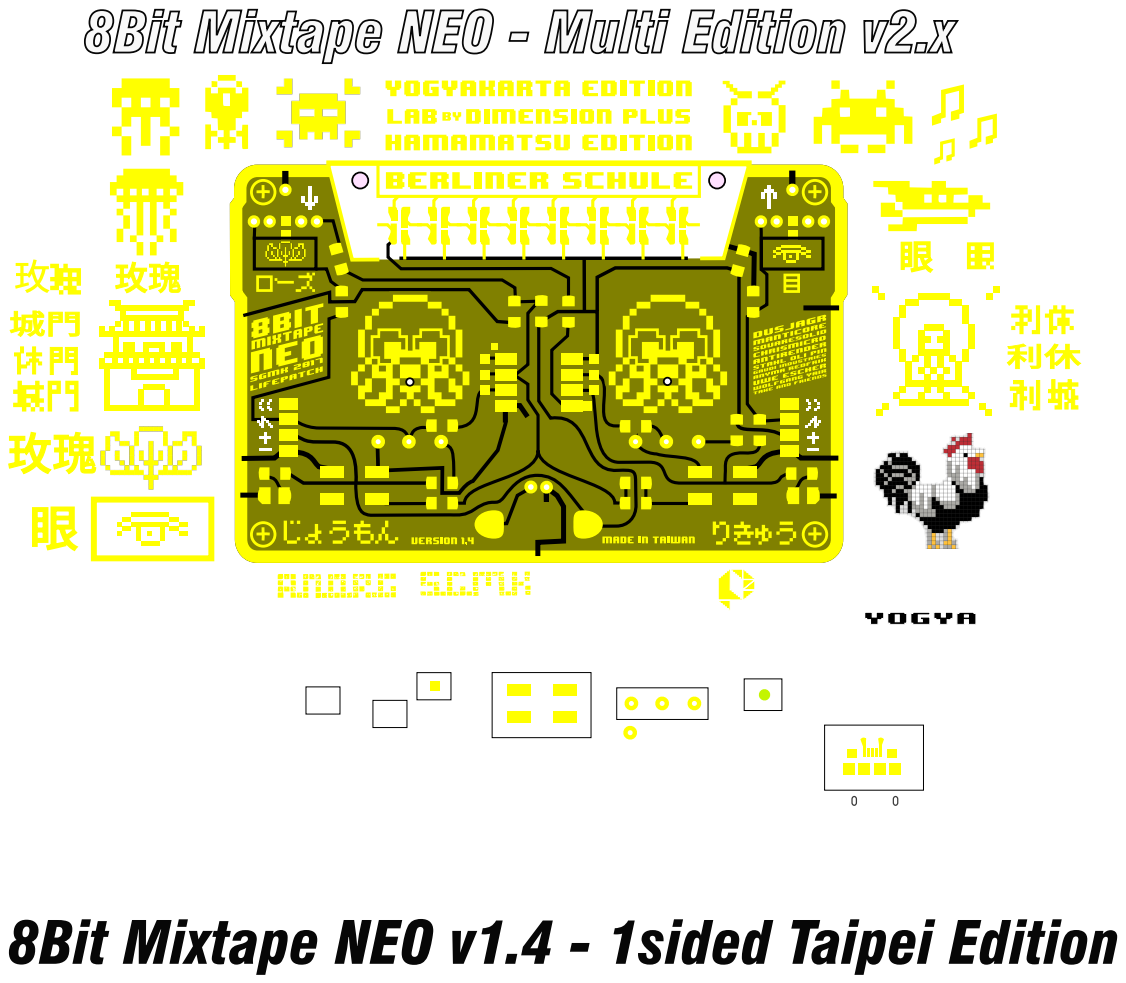
[picture p226: page 1]
