8BitMixtape/8Bit-Mixtape-NEO/boards/NEO-Coconut/MakeYourOwn_v02.pdf

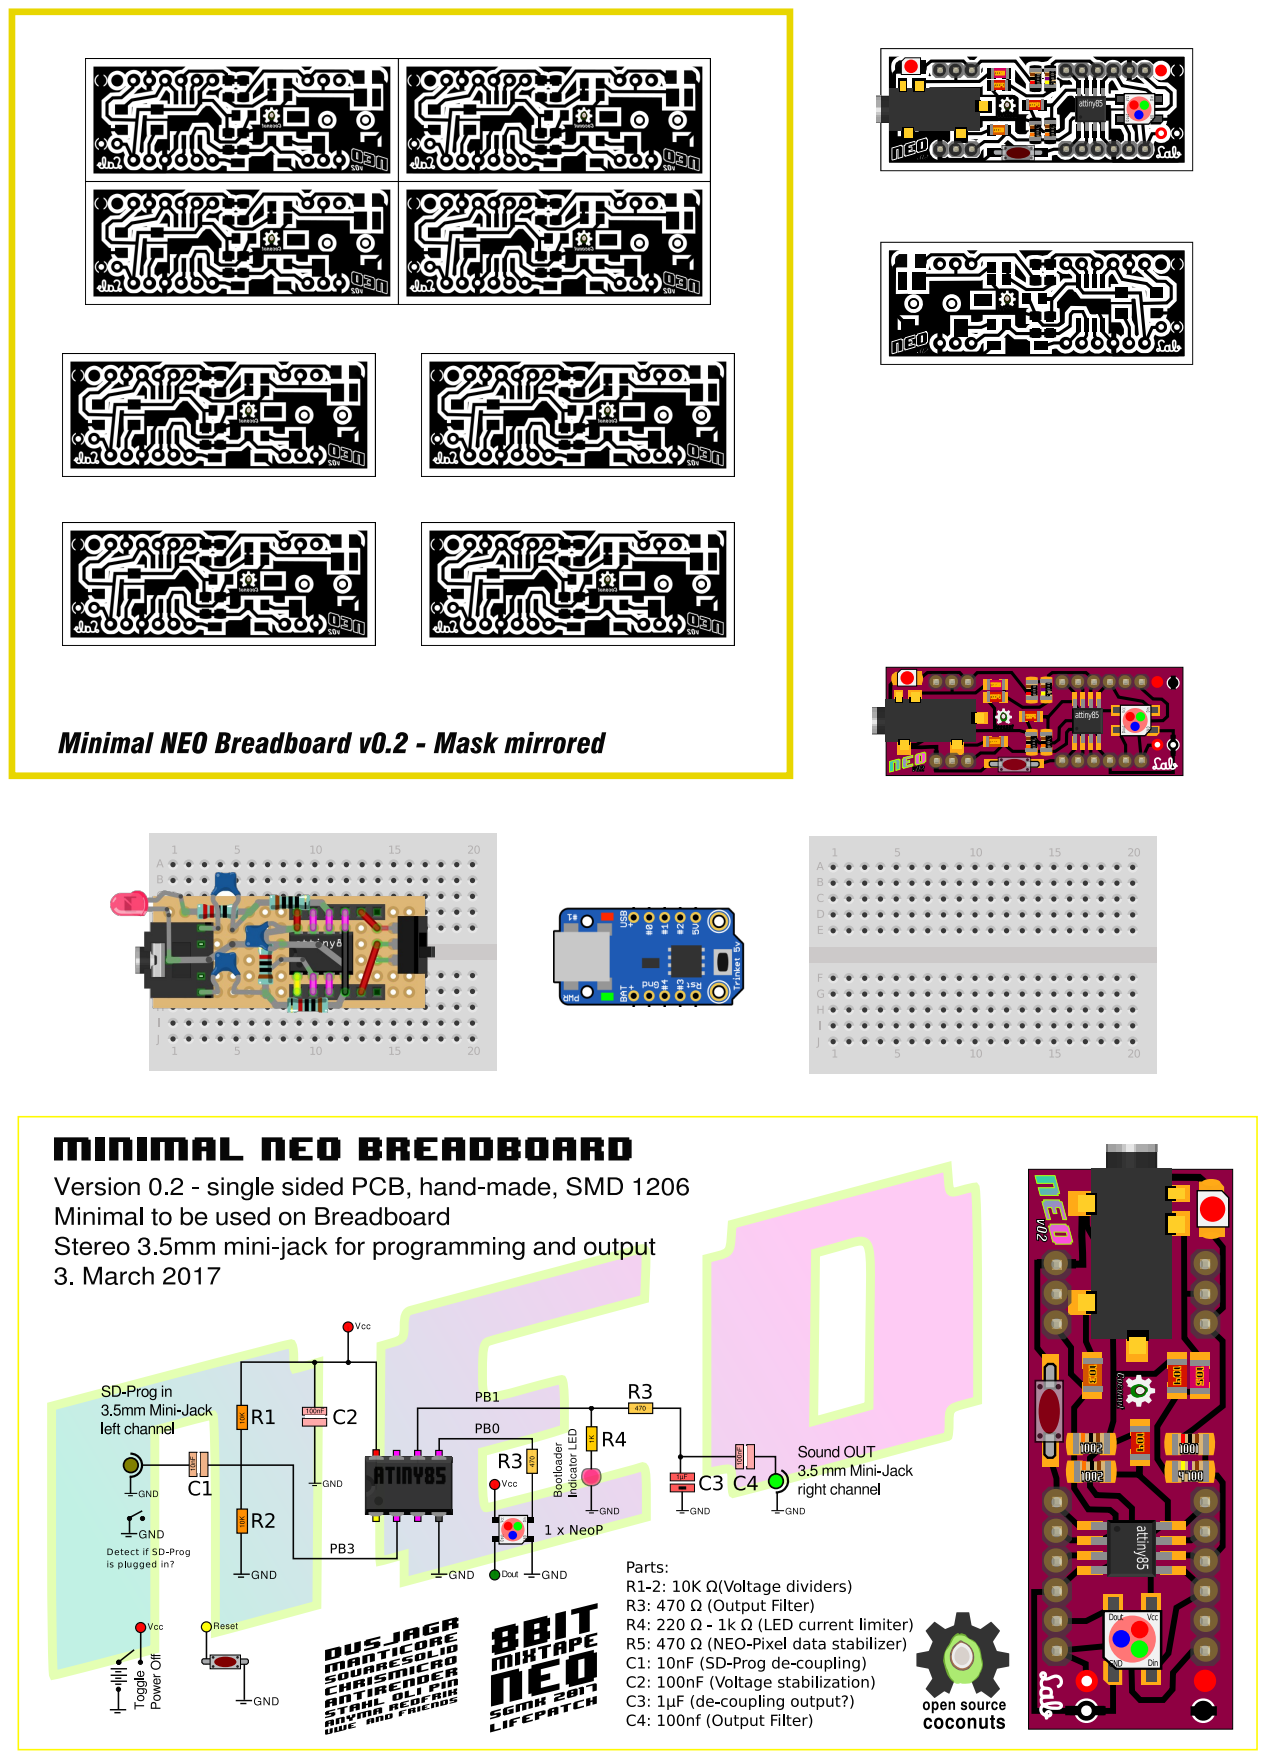
[picture p228: page 1]
