8BitMixtape/8Bit-Mixtape-NEO/boards/DIMI-8/DIMI-8_v11_anyma_MASK.pdf

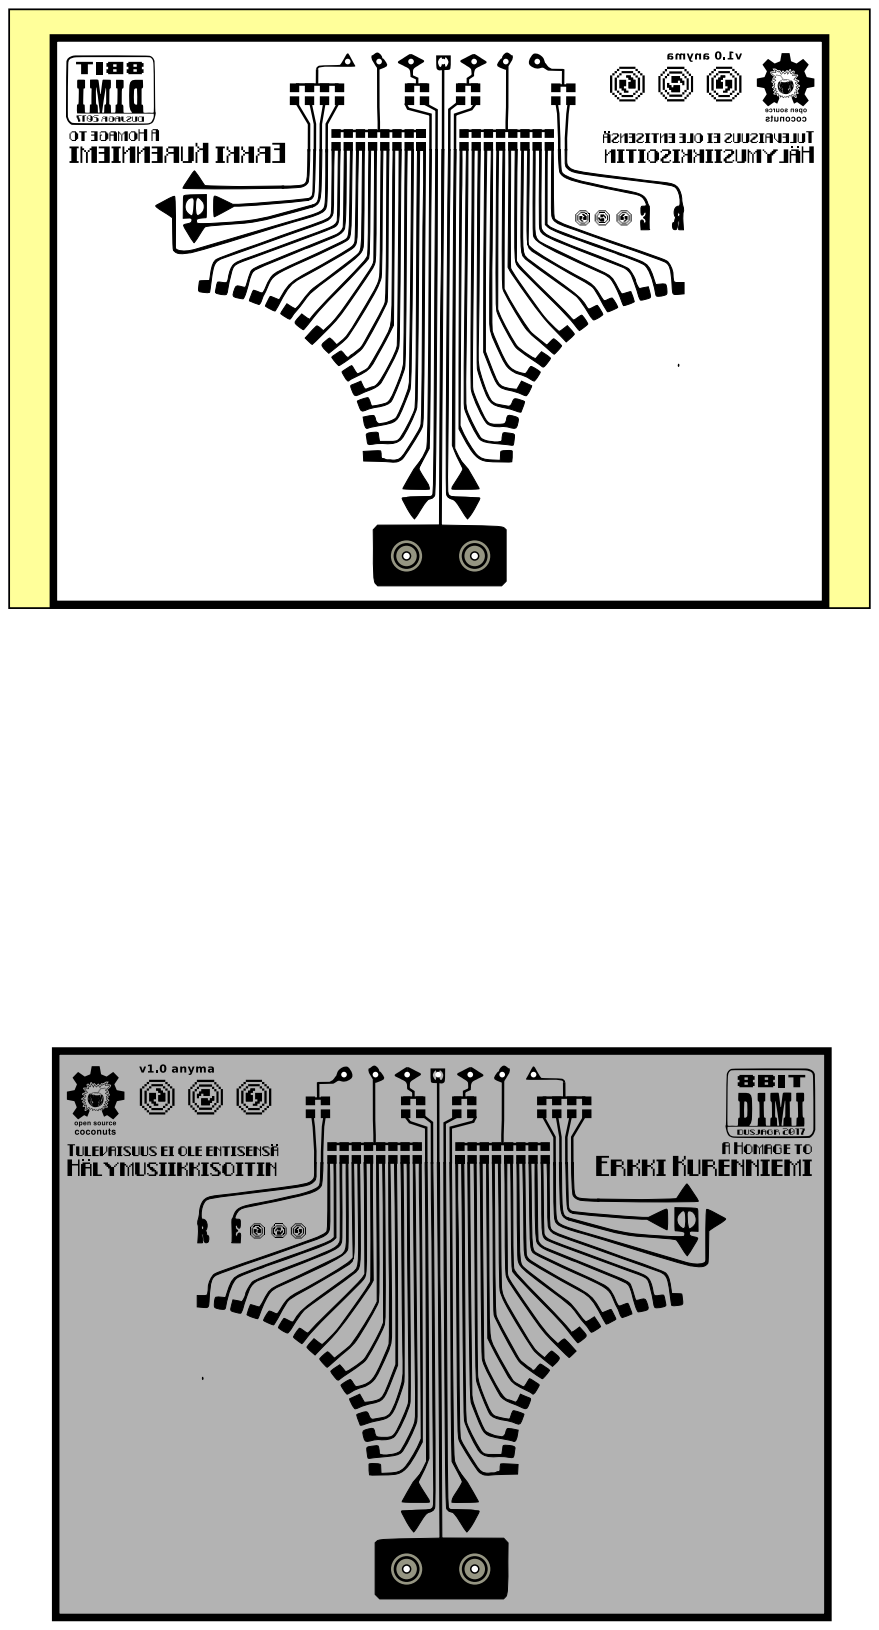
[picture p229: page 1]
