8BitMixtape/8Bit-Mixtape-NEO/boards/DIMI-8/DIMI-8.pdf

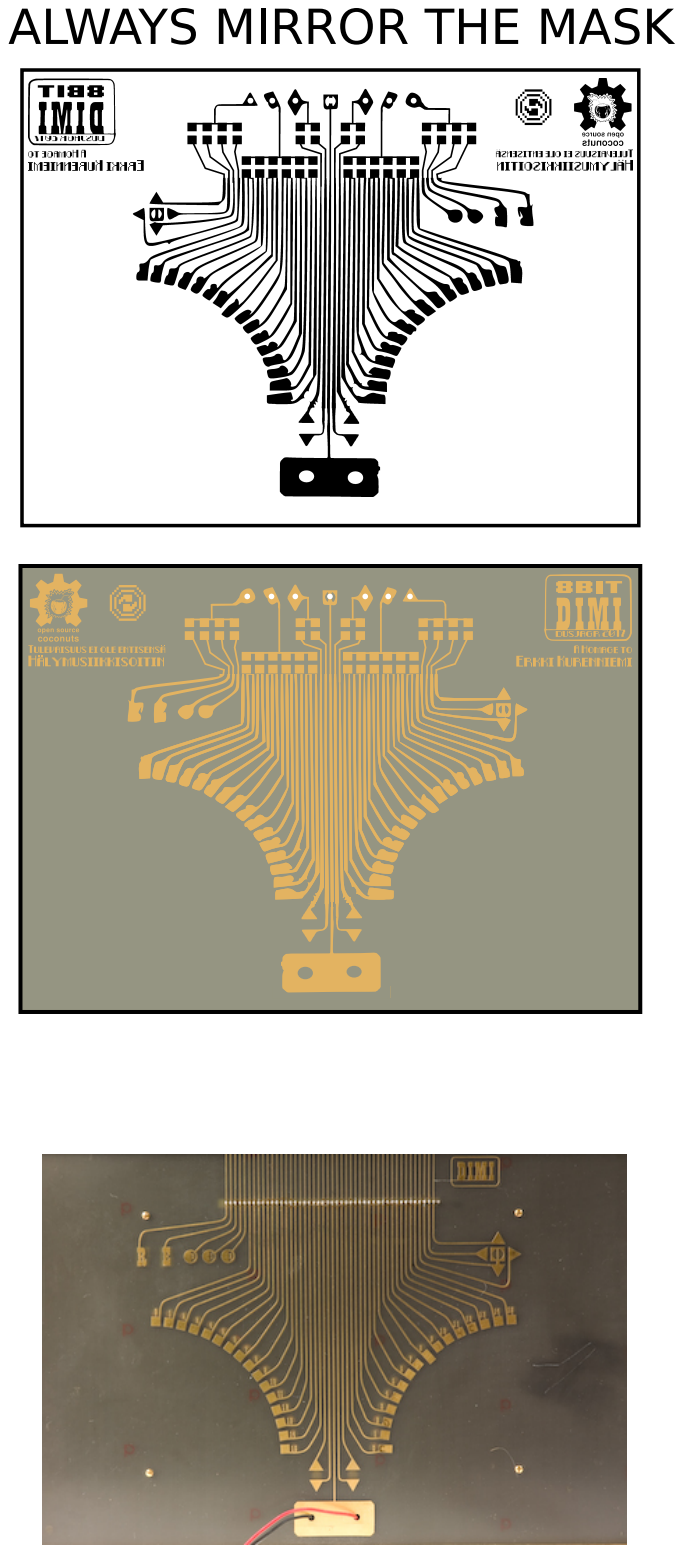
[picture p230: page 1]
