8BitMixtape/8Bit-Mixtape-NEO/Code/NEO_062_Sequencer_syncOut-PO/Pt1.cpp

/*
 * Pt1.cpp
 *
 * Created: 20.02.2017 05:46:16
 * 
 * ChrisMicro
 */ 

#include "Pt1.h"


Pt1::Pt1(uint16_t t)
{
	T_param=t;
	K_param=0x100;

	y_old=0;

}

void Pt1::setT(uint16_t t)
{
	T_param=t;	
}

void Pt1::setOutput(int16_t y)
{
	y_old=y*0x10000;
}

int16_t Pt1::filter(int16_t input)
{
	int32_t x;
	int32_t temp;

	x=input;

	int16_t y;

	// low pass filter
	y=y_old>>16;
	temp=y_old+T_param*(x-y);
	y_old=temp;	
	
	y=y_old>>16;
	
	return ((int32_t)y*K_param)>>8;

}
